newaetech/sonata-pcb/sonata-one/sonata_kicad_project/Analog_Conversion.kicad_sch

## KiCad design sonata-one/sonata_kicad_project/Analog_Conversion.kicad_sch (2025-01-31)

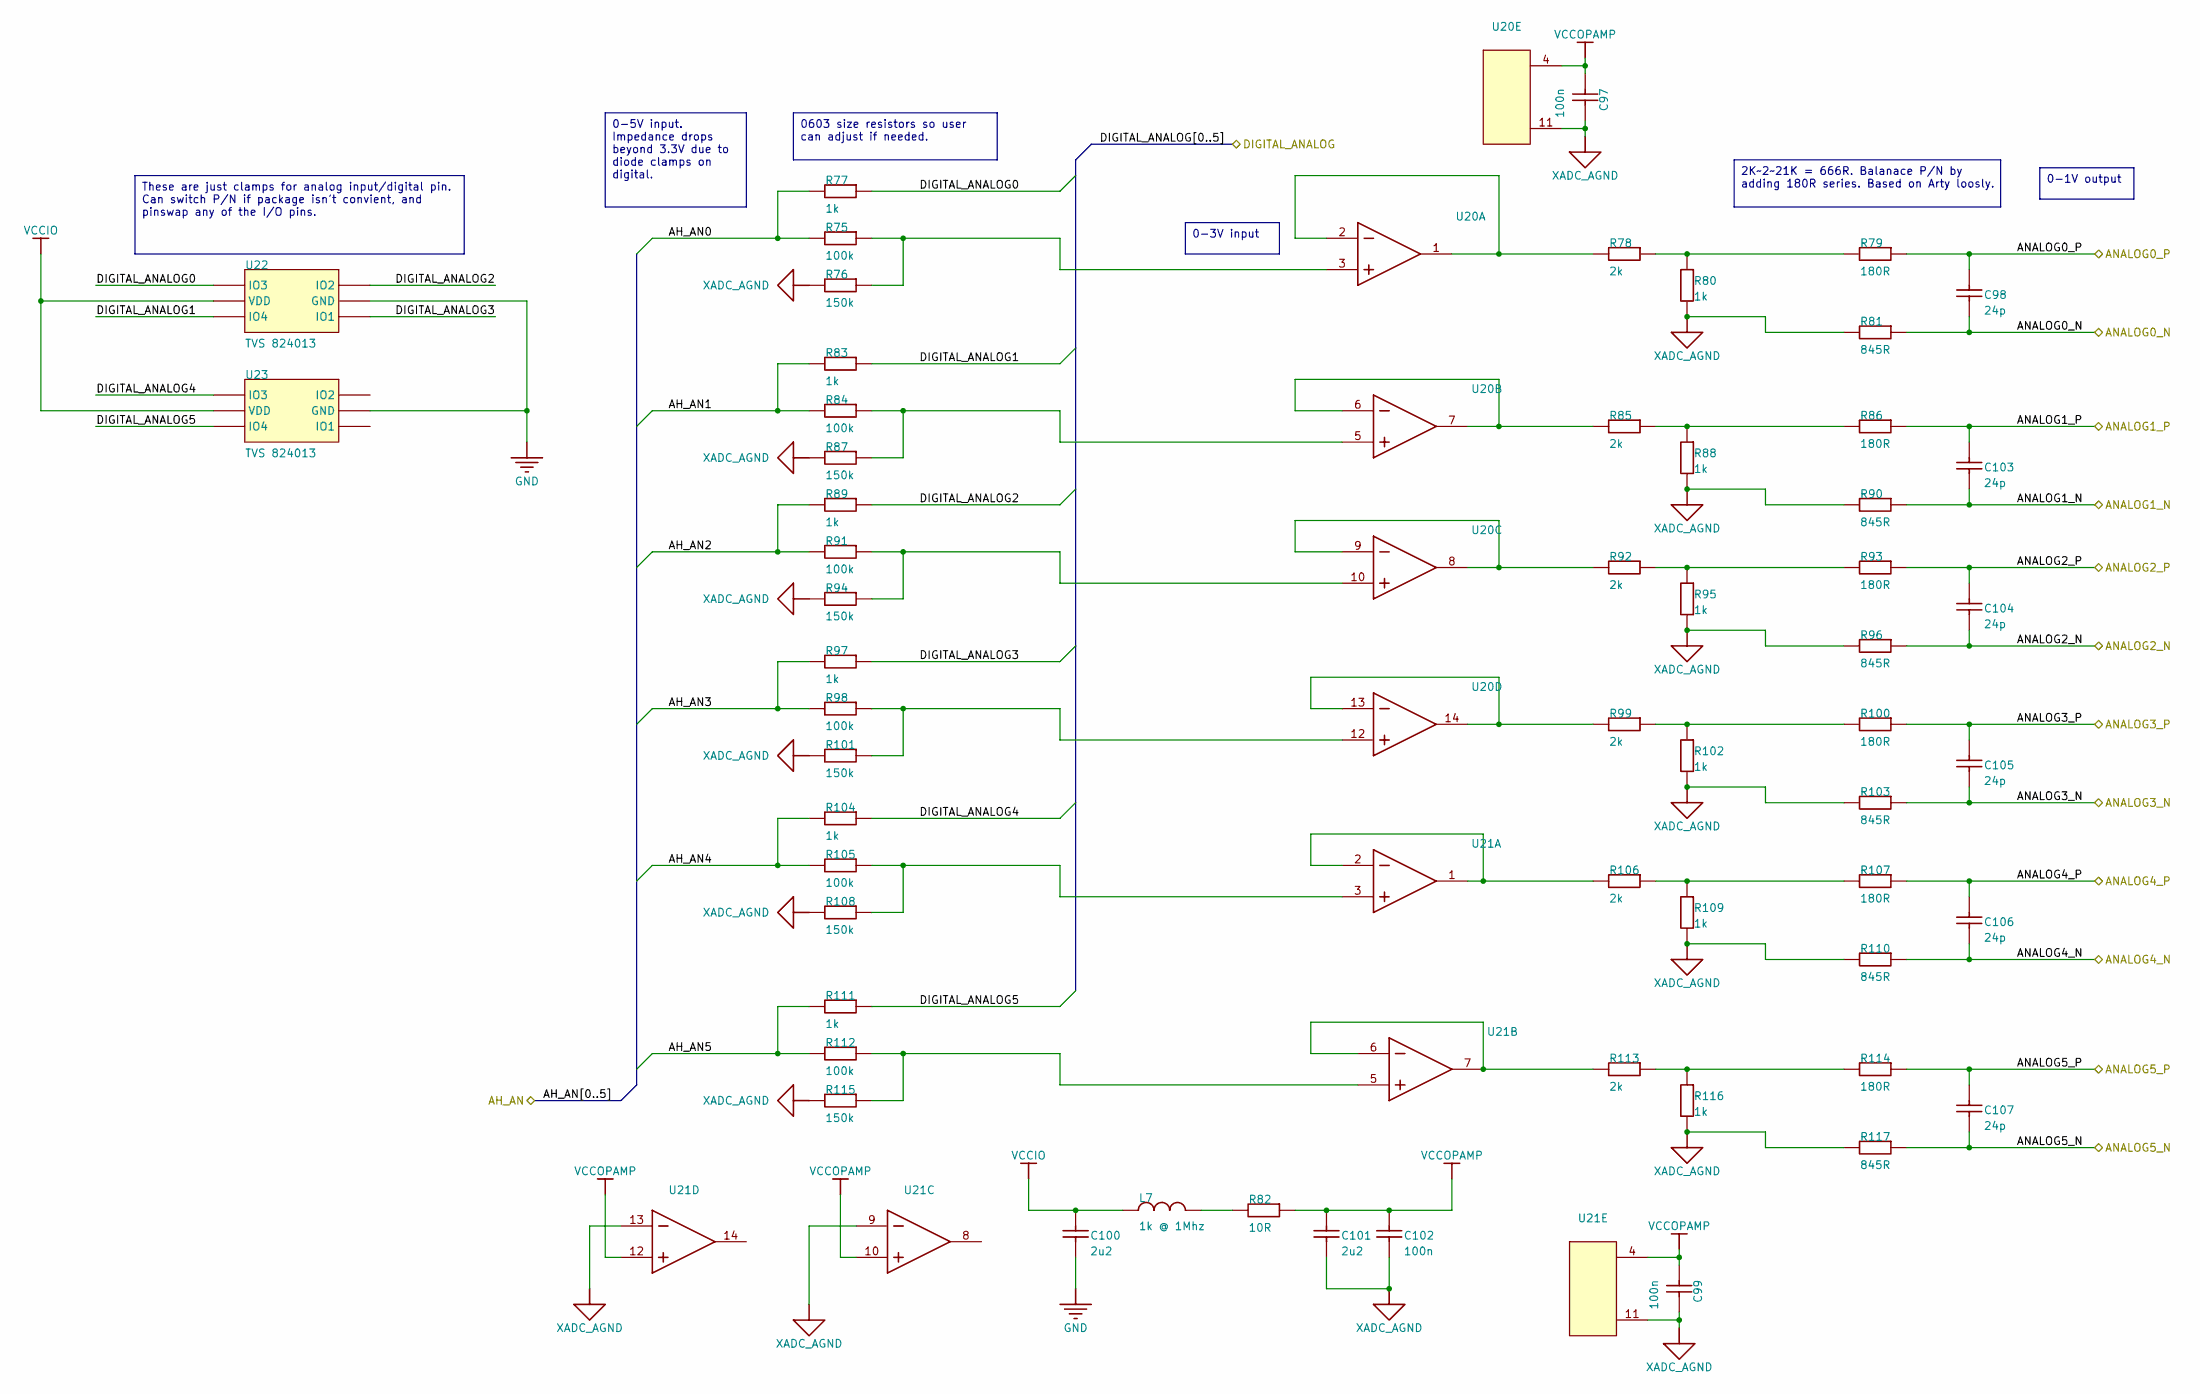
[picture p4: schematic Analog_Conversion.kicad_sch]

Parts:
C97, C99, C102: 100n; CAPC0402_M; MANUFACTURE PART NUMBER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 CGA2B3X7R1V104K050BB
C98, C103, C104, C105, C106, C107: 24p; CAPC0402_M; MANUFACTURE PART NUMBER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 GCM1555C1H240FA16D
C100, C101: 2u2; CAPC0603_M; MANUFACTURE PART NUMBER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 CL10B225KP8NNNC
L7: 1k @ 1Mhz; IND_0603; MANUFACTURE PART NUMBER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 FBMH1608HM102-T FBMH1608HM102-T FBMH160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
R75, R84, R91, R98, R105, R112: 100k; RESC1608X55N; MANUFACTURE PART NUMBER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 RC0603FR-07100KL
R76, R87, R94, R101, R108, R115: 150k; RESC1608X55N; MANUFACTURE PART NUMBER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 RC0603FR-07150KL
R77, R83, R89, R97, R104, R111: 1k; RESC1608X55N; MANUFACTURE PART NUMBER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 RC0603FR-071KL
R78, R85, R92, R99, R106, R113: 2k; RESC1005X40N; MANUFACTURE PART NUMBER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 RC0402FR-072KL
R79, R86, R93, R100, R107, R114: 180R; RESC1005X40N; MANUFACTURE PART NUMBER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 RC0402FR-07180RL
R80, R88, R95, R102, R109, R116: 1k; RESC1005X40N; MANUFACTURE PART NUMBER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 RC0402FR-071KL
R81, R90, R96, R103, R110, R117: 845R; RESC1005X40N; MANUFACTURE PART NUMBER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 RC0402FR-07845RL
R82: 10R; RESC1608X55N; MANUFACTURE PART NUMBER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 RC0603FR-0710RL
U20, U21: TSSOP-ST14_M
U22, U23: TVS 824013; SOT95P280X145-6N; MANUFACTURE PART NUMBER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 824013

Connections:
AH_AN0: R75.1, R77.1
AH_AN1: R83.1, R84.1
AH_AN2: R89.1, R91.1
AH_AN3: R97.1, R98.1
AH_AN4: R104.1, R105.1
AH_AN5: R111.1, R112.1
ANALOG0_N: C98.2, R81.2
ANALOG0_P: C98.1, R79.2
ANALOG1_N: C103.2, R90.2
ANALOG1_P: C103.1, R86.2
ANALOG2_N: C104.2, R96.2
ANALOG2_P: C104.1, R93.2
ANALOG3_N: C105.2, R103.2
ANALOG3_P: C105.1, R100.2
ANALOG4_N: C106.2, R110.2
ANALOG4_P: C106.1, R107.2
ANALOG5_N: C107.2, R117.2
ANALOG5_P: C107.1, R114.2
DIGITAL_ANALOG0: R77.2, U22.4 (IO3)
DIGITAL_ANALOG1: R83.2, U22.6 (IO4)
DIGITAL_ANALOG2: R89.2, U22.3 (IO2)
DIGITAL_ANALOG3: R97.2, U22.1 (IO1)
DIGITAL_ANALOG4: R104.2, U23.4 (IO3)
DIGITAL_ANALOG5: R111.2, U23.6 (IO4)
GND: C100.2, U22.2 (GND), U23.2 (GND)
unnamed: L7.2, R82.1
unnamed: R75.2, R76.2, U20.3 (VINA+)
unnamed: R78.1, U20.1 (VOUTA), U20.2 (VINA-)
unnamed: R78.2, R79.1, R80.1
unnamed: R84.2, R87.2, U20.5 (VINB+)
unnamed: R85.1, U20.6 (VINB-), U20.7 (VOUTB)
unnamed: R85.2, R86.1, R88.1
unnamed: R91.2, R94.2, U20.10 (VINC+)
unnamed: R92.1, U20.8 (VOUTC), U20.9 (VINC-)
unnamed: R92.2, R93.1, R95.1
unnamed: R99.1, U20.13 (VIND-), U20.14 (VOUTD)
unnamed: R99.2, R100.1, R102.1
unnamed: R98.2, R101.2, U20.12 (VIND+)
unnamed: R105.2, R108.2, U21.3 (VINA+)
unnamed: R106.1, U21.1 (VOUTA), U21.2 (VINA-)
unnamed: R106.2, R107.1, R109.1
unnamed: R112.2, R115.2, U21.5 (VINB+)
unnamed: R113.1, U21.6 (VINB-), U21.7 (VOUTB)
unnamed: R113.2, R114.1, R116.1
VCCIO: C100.1, L7.1, U22.5 (VDD), U23.5 (VDD)
VCCOPAMP: C97.1, C99.1, C101.1, C102.1, R82.2, U20.4 (Vin+), U21.4 (Vin+), U21.10 (VINC+), U21.12 (VIND+)
XADC_AGND: C97.2, C99.2, C101.2, C102.2, R76.1, R80.2, R81.1, R87.1, R88.2, R90.1, R94.1, R95.2, R96.1, R101.1, R102.2, R103.1, R108.1, R109.2, R110.1, R115.1, R116.2, R117.1, U20.11 (Vin-), U21.9 (VINC-), U21.11 (Vin-), U21.13 (VIND-)

Notes on the sheet:
0603 size resistors so user can adjust if needed.
2K~2~21K = 666R. Balanace P/N by adding 180R series. Based on Arty loosly.
0-3V input
These are just clamps for analog input/digital pin. Can switch P/N if package isn't convient, and pinswap any of the I/O pins.
0-1V output
0-5V input. Impedance drops beyond 3.3V due to diode clamps on digital.
