newaetech/sonata-pcb/sonata-one/sonata_kicad_project/ETHMAC.kicad_sch

## KiCad design sonata-one/sonata_kicad_project/ETHMAC.kicad_sch (2025-01-31)

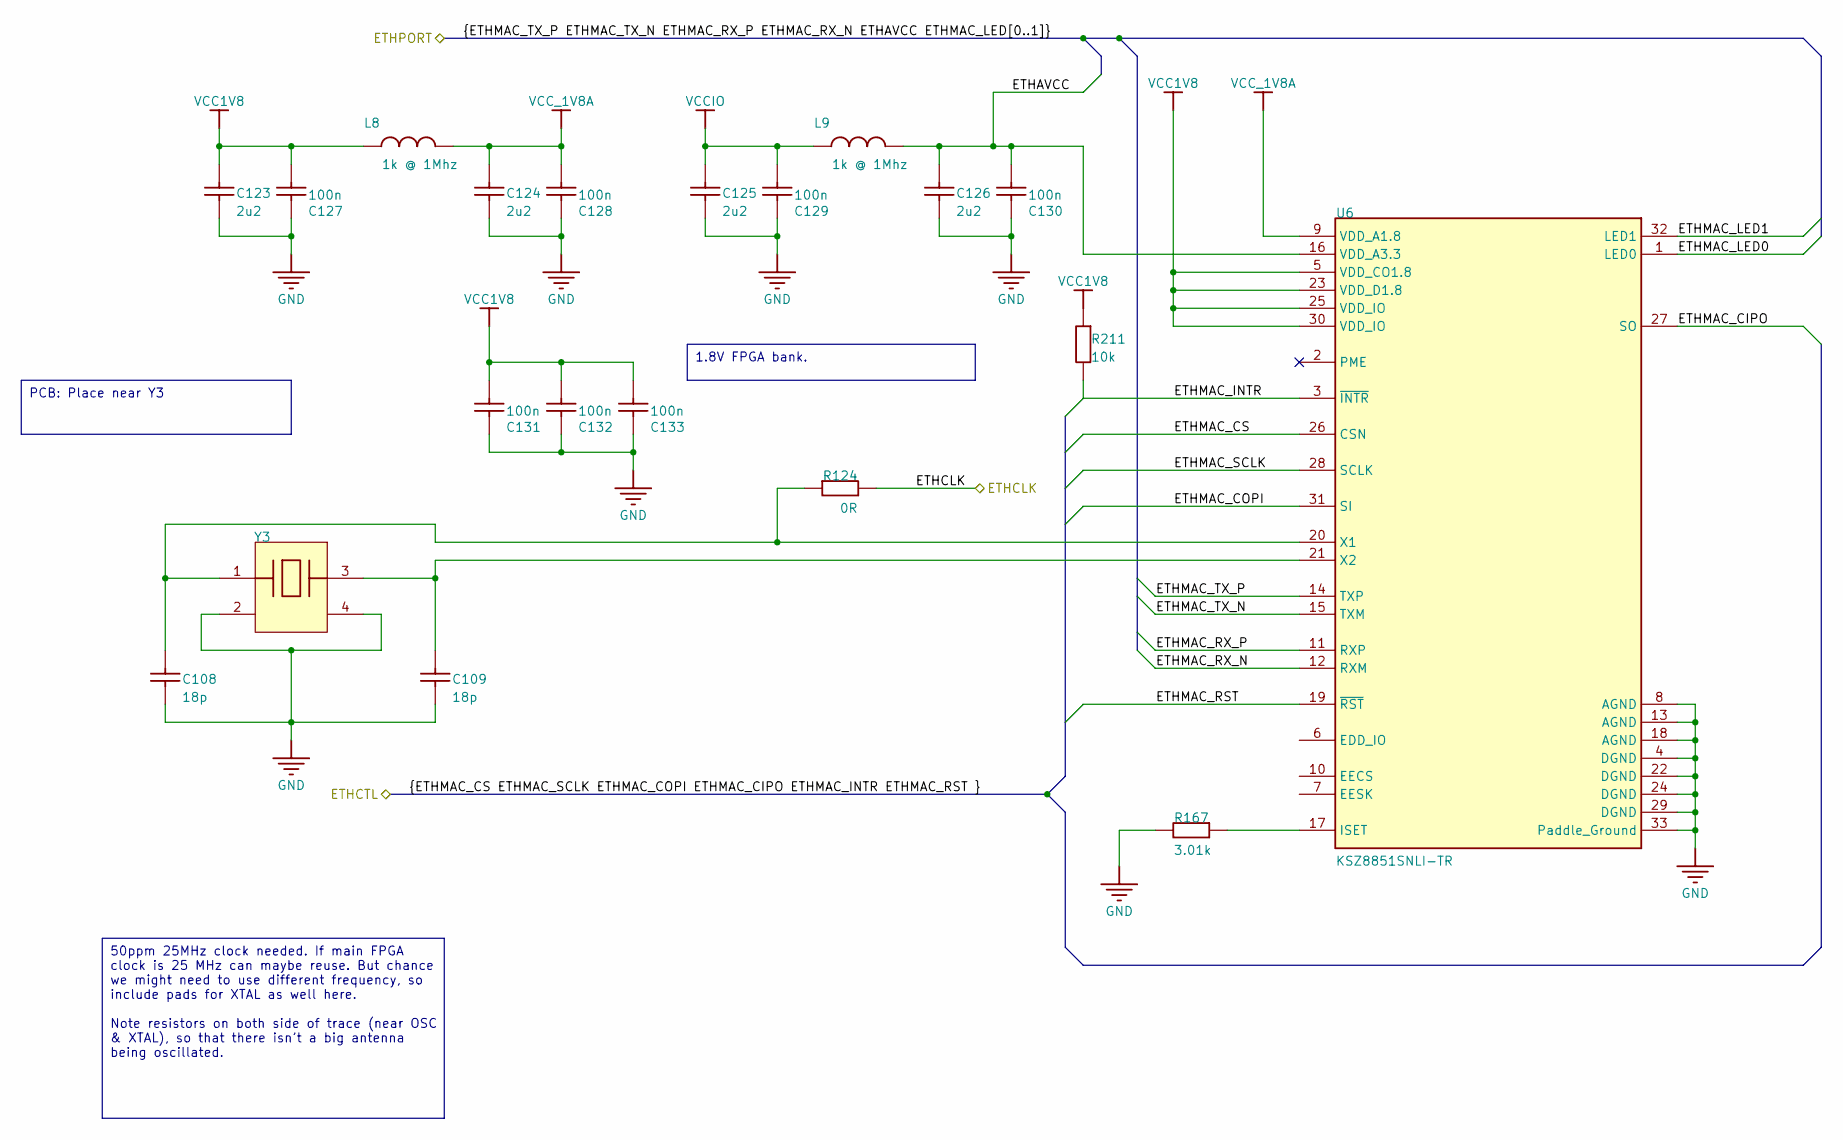
[picture p5: schematic ETHMAC.kicad_sch]

Parts:
C108, C109: 18p; CAPC0402_M; MANUFACTURE PART NUMBER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 GRM1555C1H180JA01D
C123, C124, C125, C126: 2u2; CAPC0603_M; MANUFACTURE PART NUMBER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 CL10B225KP8NNNC
C127, C128, C129, C130, C131, C132, C133: 100n; CAPC0402_M
L8, L9: 1k @ 1Mhz; IND_0603; MANUFACTURE PART NUMBER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 FBMH1608HM102-T FBMH1608HM102-T FBMH160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
R124: 0R; RESC1608X55N; MANUFACTURE PART NUMBER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 RC0603FR-070RL
R167: 3.01k; RESC1005X40N; MANUFACTURE PART NUMBER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 RC0402FR-073K01L
R211: 10k; RESC1005X40N; MANUFACTURE PART NUMBER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 RC0402FR-0710KL
U6: KSZ8851SNLI-TR; FP-QFN55-32LD-PL-5-IPC_C
Y3: H130B-12.000-16-2525-EXT-TR; 5x3.2MM XTAL; MANUFACTURE PART NUMBER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 H130B-25.000-18-1030-EXT-TR

Connections:
ETHAVCC: C126.1, C130.1, L9.2, U6.16 (VDD_A3.3)
ETHCLK: R124.1
ETHMAC_CIPO: U6.27 (SO)
ETHMAC_COPI: U6.31 (SI)
ETHMAC_CS: U6.26 (CSN)
ETHMAC_INTR: R211.2, U6.3 (~INTR)
ETHMAC_LED0: U6.1 (LED0)
ETHMAC_LED1: U6.32 (LED1)
ETHMAC_RST: U6.19 (~RST)
ETHMAC_RX_N: U6.12 (RXM)
ETHMAC_RX_P: U6.11 (RXP)
ETHMAC_SCLK: U6.28 (SCLK)
ETHMAC_TX_N: U6.15 (TXM)
ETHMAC_TX_P: U6.14 (TXP)
GND: C108.2, C109.2, C123.2, C124.2, C125.2, C126.2, C127.2, C128.2, C129.2, C130.2, C131.2, C132.2, C133.2, R167.1, U6.4 (DGND), U6.8 (AGND), U6.13 (AGND), U6.18 (AGND), U6.22 (DGND), U6.24 (DGND), U6.29 (DGND), U6.33 (Paddle_Ground), Y3.2, Y3.4
unnamed: C108.1, R124.2, U6.20 (X1), Y3.1
unnamed: C109.1, U6.21 (X2), Y3.3
unnamed: R167.2, U6.17 (ISET)
VCC1V8: C123.1, C127.1, C131.1, C132.1, C133.1, L8.1, R211.1, U6.5 (VDD_CO1.8), U6.23 (VDD_D1.8), U6.25 (VDD_IO), U6.30 (VDD_IO)
VCCIO: C125.1, C129.1, L9.1
VCC_1V8A: C124.1, C128.1, L8.2, U6.9 (VDD_A1.8)

Notes on the sheet:
50ppm 25MHz clock needed. If main FPGA clock is 25 MHz can maybe reuse. But chance we might need to use different frequency, so include pads for XTAL as well here. Note resistors on both side of trace (near OSC & XTAL), so that there isn't a big antenna being oscillated.
1.8V FPGA bank.
PCB: Place near Y3
