newaetech/sonata-pcb/sonata-one/sonata_kicad_project/FPGA_ANA_1.8V.kicad_sch

## KiCad design sonata-one/sonata_kicad_project/FPGA_ANA_1.8V.kicad_sch (2025-01-31)

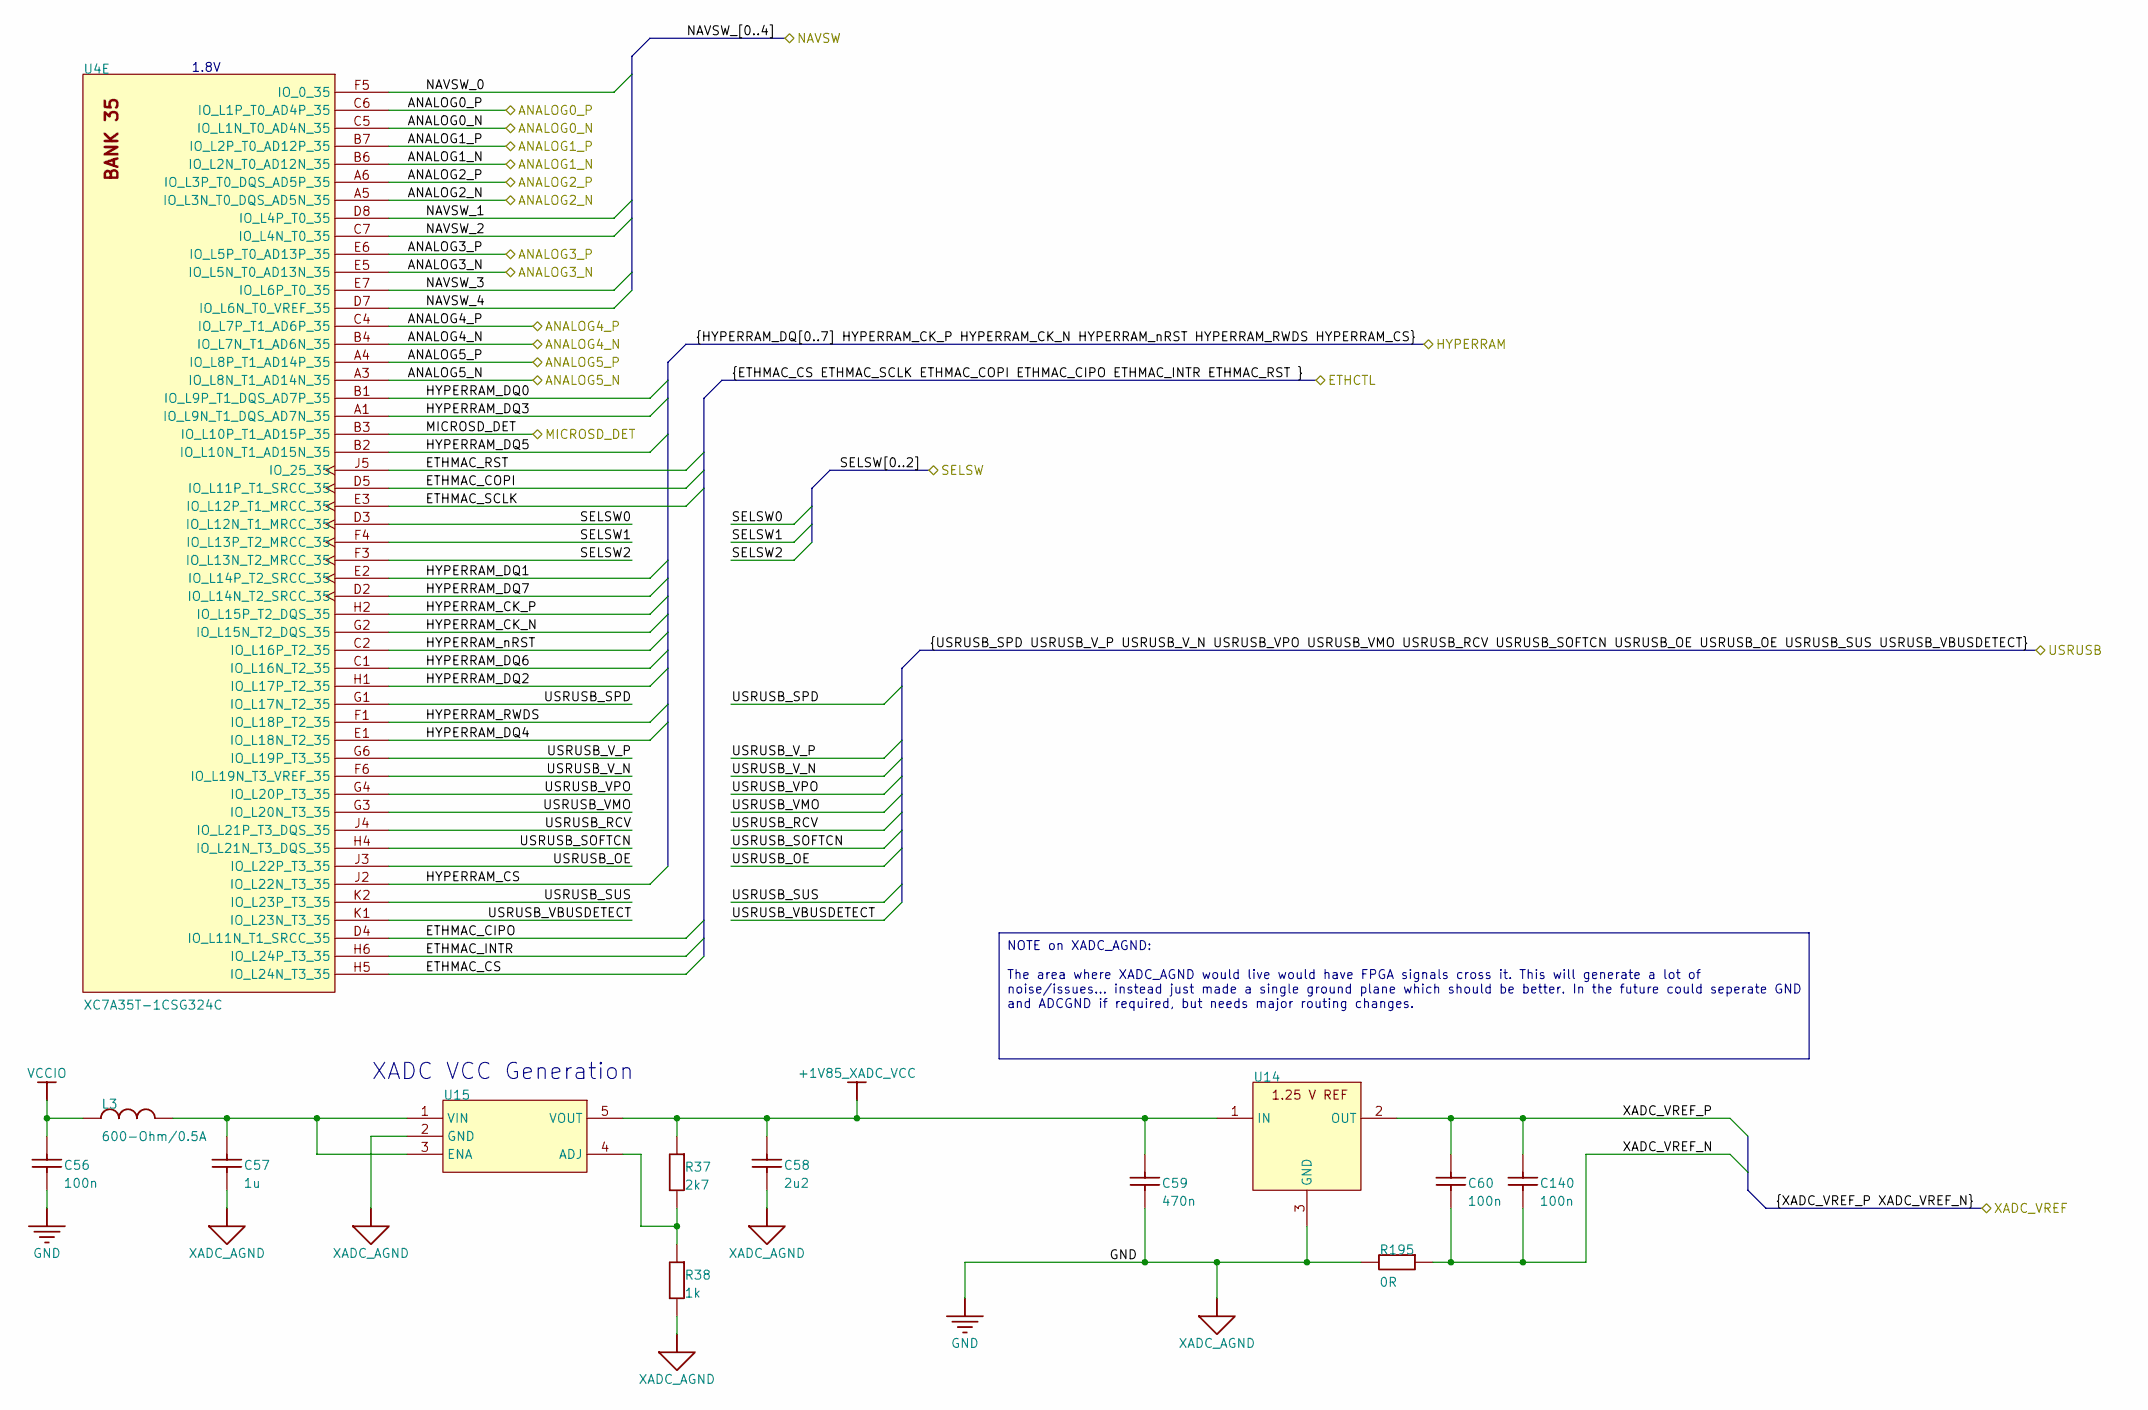
[picture p6: schematic FPGA_ANA_1.8V.kicad_sch]

Parts:
C56, C60, C140: 100n; CAPC0402_M; MANUFACTURE PART NUMBER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 CGA2B3X7R1V104K050BB
C57: 1u; CAPC0603_M; MANUFACTURE PART NUMBER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 CL10A105KB8NNNC
C58: 2u2; CAPC0603_M; MANUFACTURE PART NUMBER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 GRM188R61E225MA12D
C59: 470n; CAPC0603_M; MANUFACTURE PART NUMBER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 UMK107B7474KA-TR
L3: 600-Ohm/0.5A; IND_0603; MANUFACTURE PART NUMBER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 BLM18AG601SN1D
R37: 2k7; RESC1005X40N; MANUFACTURE PART NUMBER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 RC0402FR-072K7L
R38: 1k; RESC1005X40N; MANUFACTURE PART NUMBER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 RC0402FR-071KL
R195: 0R; RESC1005X40N; MANUFACTURE PART NUMBER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 RC0402FR-070RL
U4: XC7A35T-1CSG324C; CSG324
U14: REF3012AIDBZT; SOT95P237X112-3N; MANUFACTURE PART NUMBER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 REF3012AIDBZT
U15: Linear Voltage Regulator IC 1 Output 300mA TSOT-5; SOT23-5P95_285X145L45X40; MANUFACTURE PART NUMBER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 ADP123AUJZ-R7

Connections:
+1V85_XADC_VCC: C58.1, C59.1, R37.1, U14.1 (IN), U15.5 (VOUT)
ANALOG0_N: U4.C5 (IO_L1N_T0_AD4N_35)
ANALOG0_P: U4.C6 (IO_L1P_T0_AD4P_35)
ANALOG1_N: U4.B6 (IO_L2N_T0_AD12N_35)
ANALOG1_P: U4.B7 (IO_L2P_T0_AD12P_35)
ANALOG2_N: U4.A5 (IO_L3N_T0_DQS_AD5N_35)
ANALOG2_P: U4.A6 (IO_L3P_T0_DQS_AD5P_35)
ANALOG3_N: U4.E5 (IO_L5N_T0_AD13N_35)
ANALOG3_P: U4.E6 (IO_L5P_T0_AD13P_35)
ANALOG4_N: U4.B4 (IO_L7N_T1_AD6N_35)
ANALOG4_P: U4.C4 (IO_L7P_T1_AD6P_35)
ANALOG5_N: U4.A3 (IO_L8N_T1_AD14N_35)
ANALOG5_P: U4.A4 (IO_L8P_T1_AD14P_35)
ETHMAC_CIPO: U4.D4 (IO_L11N_T1_SRCC_35)
ETHMAC_COPI: U4.D5 (IO_L11P_T1_SRCC_35)
ETHMAC_CS: U4.H5 (IO_L24N_T3_35)
ETHMAC_INTR: U4.H6 (IO_L24P_T3_35)
ETHMAC_RST: U4.J5 (IO_25_35)
ETHMAC_SCLK: U4.E3 (IO_L12P_T1_MRCC_35)
GND: C56.2, C57.2, C58.2, C59.2, R38.2, R195.1, U14.3 (GND), U15.2 (GND)
HYPERRAM_CK_N: U4.G2 (IO_L15N_T2_DQS_35)
HYPERRAM_CK_P: U4.H2 (IO_L15P_T2_DQS_35)
HYPERRAM_CS: U4.J2 (IO_L22N_T3_35)
HYPERRAM_DQ0: U4.B1 (IO_L9P_T1_DQS_AD7P_35)
HYPERRAM_DQ1: U4.E2 (IO_L14P_T2_SRCC_35)
HYPERRAM_DQ2: U4.H1 (IO_L17P_T2_35)
HYPERRAM_DQ3: U4.A1 (IO_L9N_T1_DQS_AD7N_35)
HYPERRAM_DQ4: U4.E1 (IO_L18N_T2_35)
HYPERRAM_DQ5: U4.B2 (IO_L10N_T1_AD15N_35)
HYPERRAM_DQ6: U4.C1 (IO_L16N_T2_35)
HYPERRAM_DQ7: U4.D2 (IO_L14N_T2_SRCC_35)
HYPERRAM_RWDS: U4.F1 (IO_L18P_T2_35)
HYPERRAM_nRST: U4.C2 (IO_L16P_T2_35)
MICROSD_DET: U4.B3 (IO_L10P_T1_AD15P_35)
NAVSW_0: U4.F5 (IO_0_35)
NAVSW_1: U4.D8 (IO_L4P_T0_35)
NAVSW_2: U4.C7 (IO_L4N_T0_35)
NAVSW_3: U4.E7 (IO_L6P_T0_35)
NAVSW_4: U4.D7 (IO_L6N_T0_VREF_35)
unnamed: C57.1, L3.2, U15.1 (VIN), U15.3 (ENA)
unnamed: R37.2, R38.1, U15.4 (ADJ)
SELSW0: U4.D3 (IO_L12N_T1_MRCC_35)
SELSW1: U4.F4 (IO_L13P_T2_MRCC_35)
SELSW2: U4.F3 (IO_L13N_T2_MRCC_35)
USRUSB_OE: U4.J3 (IO_L22P_T3_35)
USRUSB_RCV: U4.J4 (IO_L21P_T3_DQS_35)
USRUSB_SOFTCN: U4.H4 (IO_L21N_T3_DQS_35)
USRUSB_SPD: U4.G1 (IO_L17N_T2_35)
USRUSB_SUS: U4.K2 (IO_L23P_T3_35)
USRUSB_VBUSDETECT: U4.K1 (IO_L23N_T3_35)
USRUSB_VMO: U4.G3 (IO_L20N_T3_35)
USRUSB_VPO: U4.G4 (IO_L20P_T3_35)
USRUSB_V_N: U4.F6 (IO_L19N_T3_VREF_35)
USRUSB_V_P: U4.G6 (IO_L19P_T3_35)
VCCIO: C56.1, L3.1
XADC_VREF_N: C60.2, C140.2, R195.2
XADC_VREF_P: C60.1, C140.1, U14.2 (OUT)

Notes on the sheet:
NOTE on XADC_AGND: The area where XADC_AGND would live would have FPGA signals cross it. This will generate a lot of noise/issues... instead just made a single ground plane which should be better. In the future could seperate GND and ADCGND if required, but needs major routing changes.
XADC VCC Generation
1.8V
