newaetech/sonata-pcb/sonata-one/sonata_kicad_project/FPGA_Config.kicad_sch

## KiCad design sonata-one/sonata_kicad_project/FPGA_Config.kicad_sch (2025-01-31)

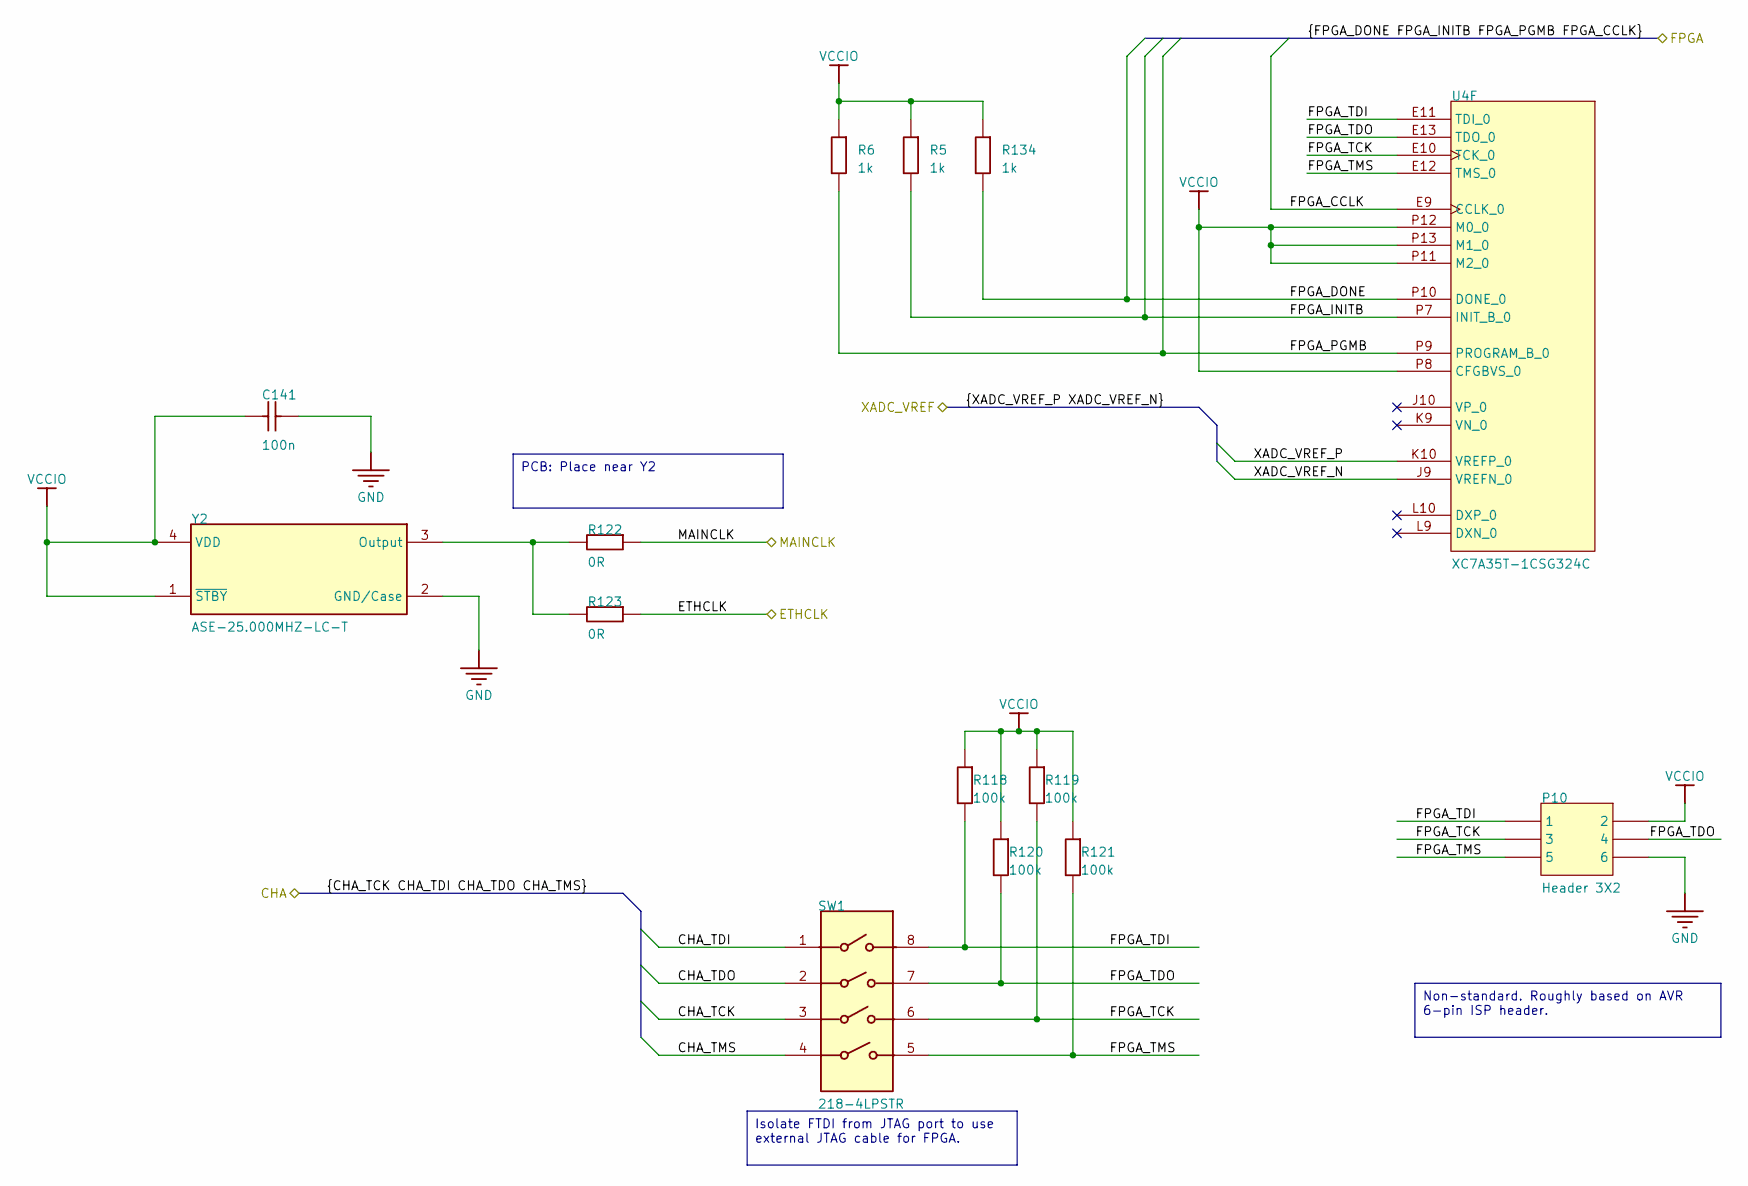
[picture p7: schematic FPGA_Config.kicad_sch]

Parts:
C141: 100n; CAPC0402_M; MANUFACTURE PART NUMBER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 CGA2B3X7R1V104K050BB
P10: Header 3X2; HDR2X3
R5, R6, R134: 1k; RESC1608X55N; MANUFACTURE PART NUMBER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 RC0603FR-071KL
R118, R119, R120, R121: 100k; RESC1005X40N; MANUFACTURE PART NUMBER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 RC0402FR-07100KL
R122, R123: 0R; RESC1608X55N; MANUFACTURE PART NUMBER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 RC0603FR-070RL
SW1: 218-4LPSTR; FP-218-4LPSTR-MFG
U4: XC7A35T-1CSG324C; CSG324
Y2: ASE-25.000MHZ-LC-T; FP-ASE-MFG

Connections:
CHA_TCK: SW1.3
CHA_TDI: SW1.1
CHA_TDO: SW1.2
CHA_TMS: SW1.4
ETHCLK: R123.2
FPGA_CCLK: U4.E9 (CCLK_0)
FPGA_DONE: R134.2, U4.P10 (DONE_0)
FPGA_INITB: R5.2, U4.P7 (INIT_B_0)
FPGA_PGMB: R6.2, U4.P9 (PROGRAM_B_0)
FPGA_TCK: P10.3, R119.2, SW1.6, U4.E10 (TCK_0)
FPGA_TDI: P10.1, R118.2, SW1.8, U4.E11 (TDI_0)
FPGA_TDO: P10.4, R120.2, SW1.7, U4.E13 (TDO_0)
FPGA_TMS: P10.5, R121.2, SW1.5, U4.E12 (TMS_0)
GND: C141.2, P10.6, Y2.2 (GND/Case)
MAINCLK: R122.2
unnamed: R122.1, R123.1, Y2.3 (Output)
VCCIO: C141.1, P10.2, R5.1, R6.1, R118.1, R119.1, R120.1, R121.1, R134.1, U4.P8 (CFGBVS_0), U4.P11 (M2_0), U4.P12 (M0_0), U4.P13 (M1_0), Y2.1 (~STBY), Y2.4 (VDD)
XADC_VREF_N: U4.J9 (VREFN_0)
XADC_VREF_P: U4.K10 (VREFP_0)

Notes on the sheet:
Non-standard. Roughly based on AVR 6-pin ISP header.
PCB: Place near Y2
Isolate FTDI from JTAG port to use external JTAG cable for FPGA.
