newaetech/sonata-pcb/sonata-one/sonata_kicad_project/FPGA_IO14_34_Flash.kicad_sch

## KiCad design sonata-one/sonata_kicad_project/FPGA_IO14_34_Flash.kicad_sch (2025-01-31)

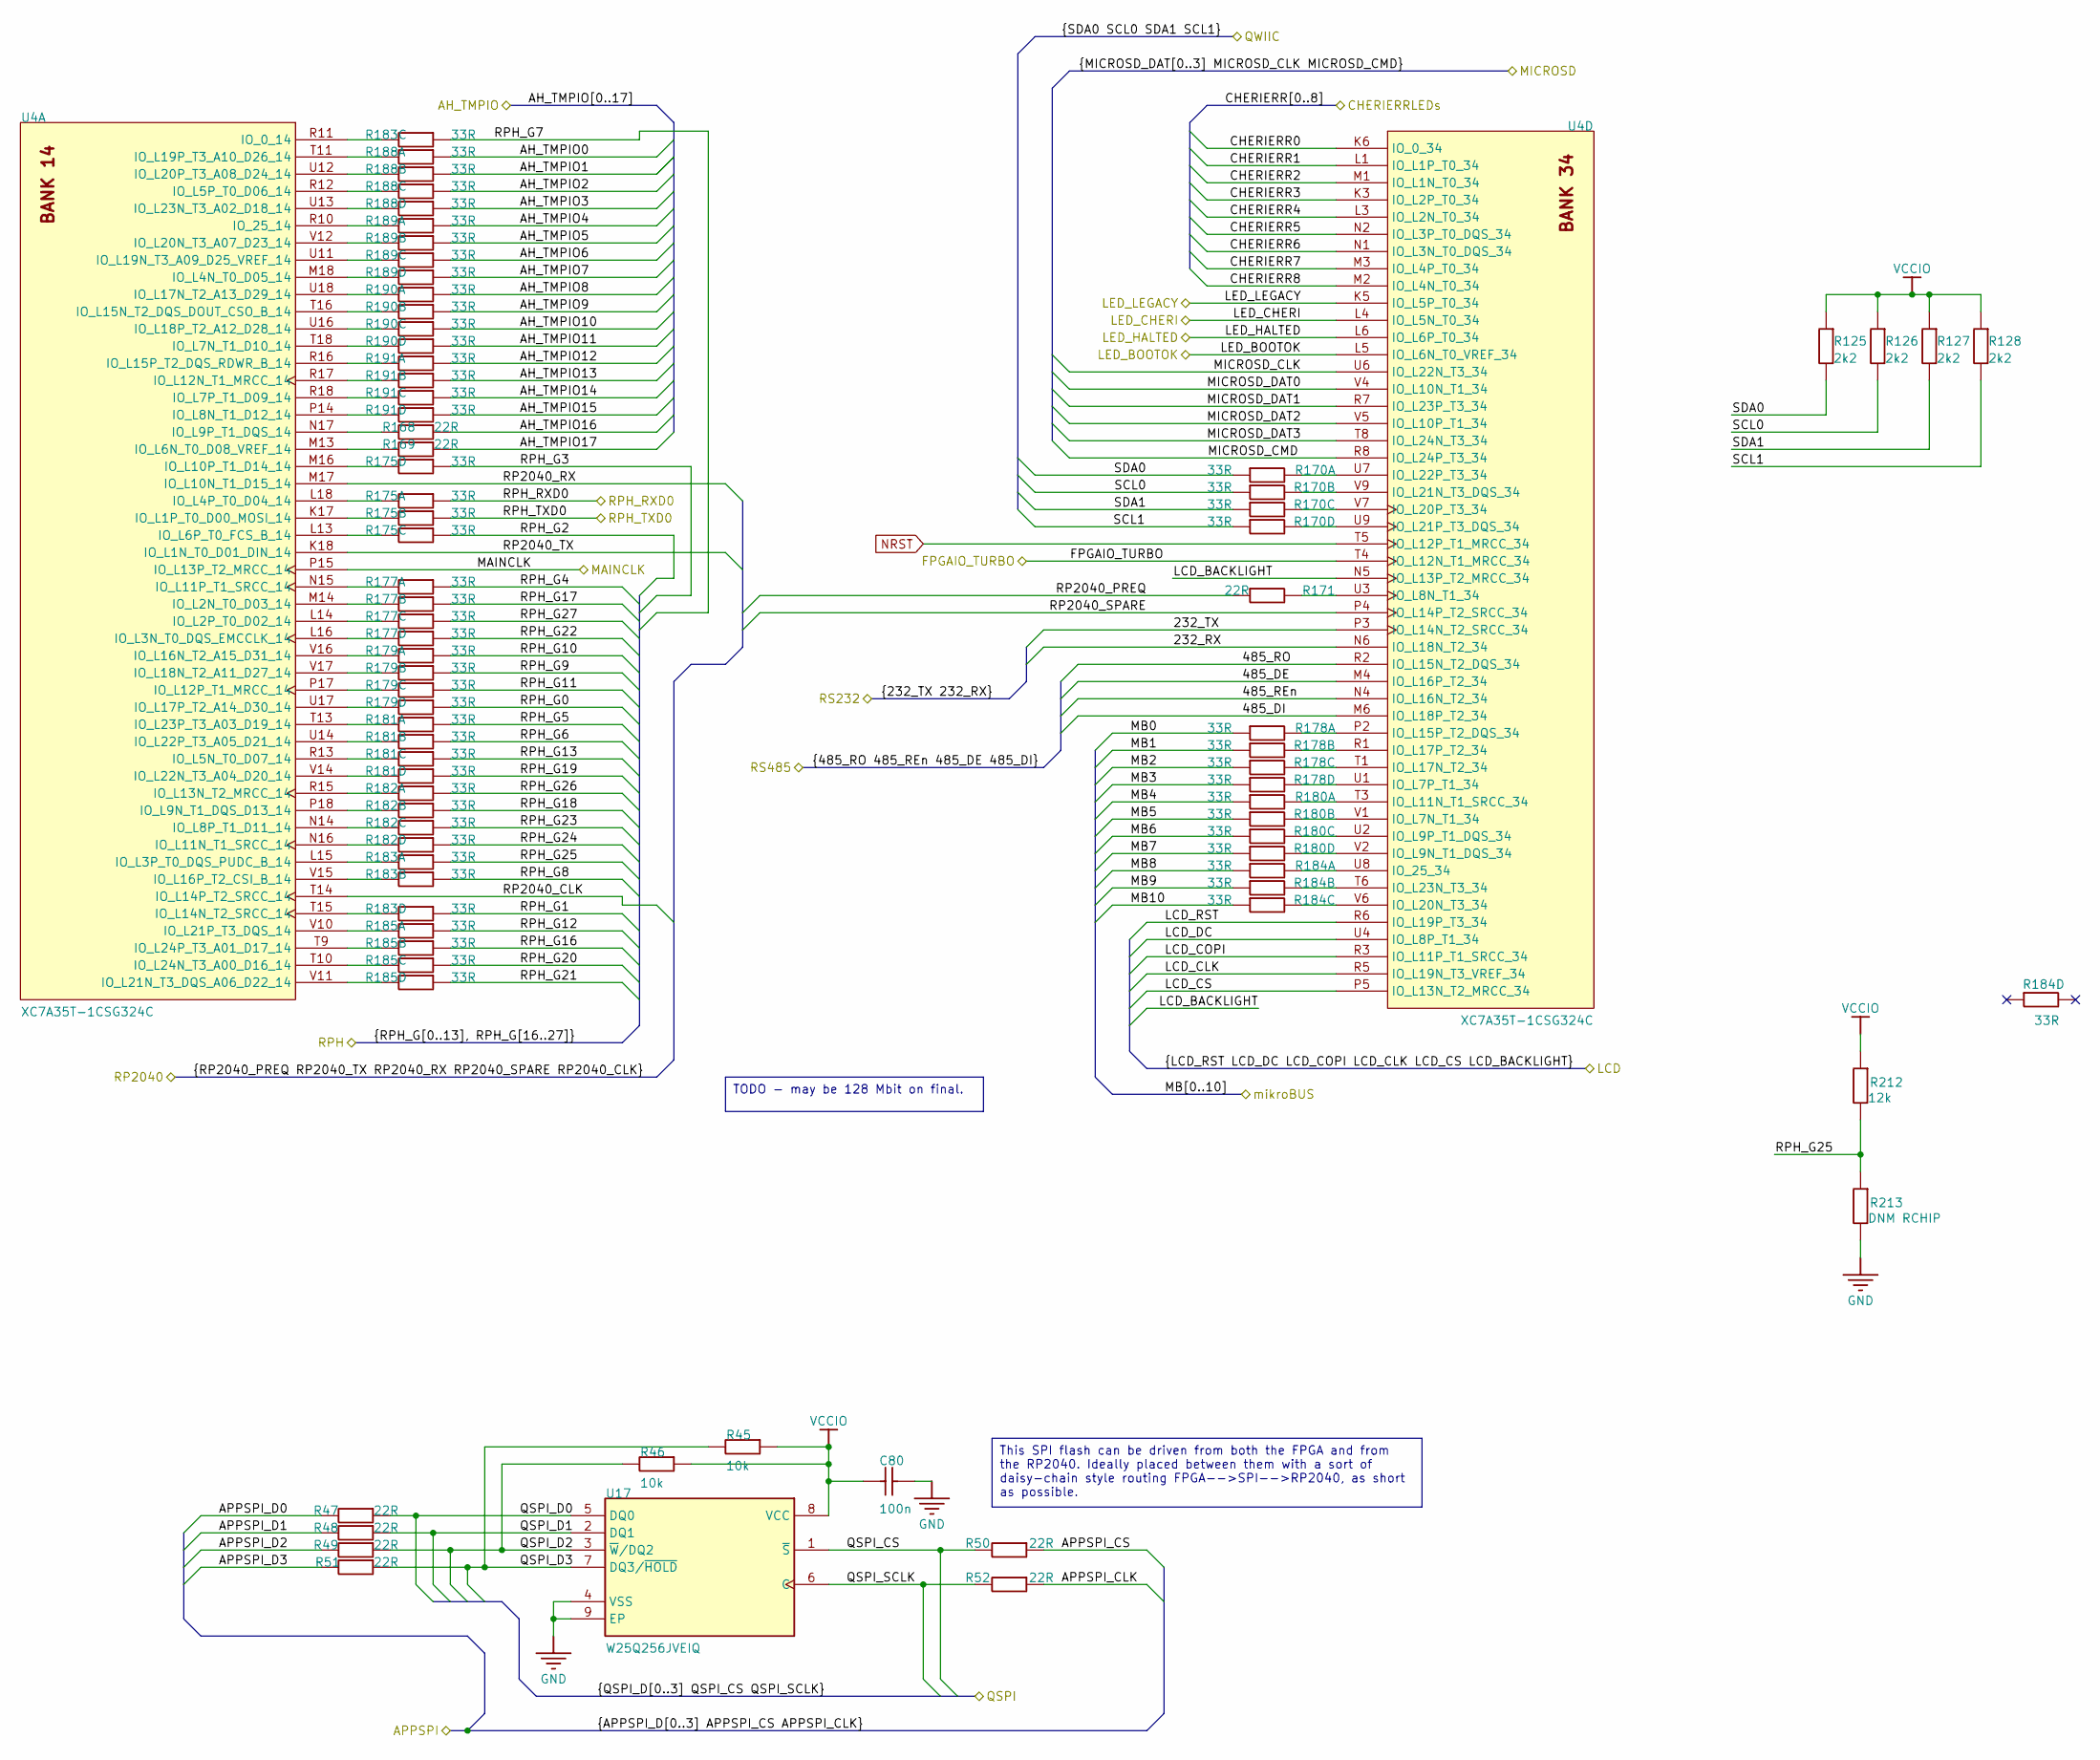
[picture p8: schematic FPGA_IO14_34_Flash.kicad_sch]

Parts:
C80: 100n; CAPC0402_M; MANUFACTURE PART NUMBER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 CGA2B3X7R1V104K050BB
R45, R46: 10k; RESC1005X40N; MANUFACTURE PART NUMBER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 RC0402FR-0710KL
R47, R48, R49, R50, R51, R52, R168, R169, R171: 22R; RESC1005X40N; MANUFACTURE PART NUMBER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 RC0402FR-0722RL
R125, R126, R127, R128: 2k2; RESC1608X55N; MANUFACTURE PART NUMBER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 RC0603FR-072K2L
R170, R175, R177, R178, R179, R180, R181, R182, R183, R184, R185, R188, R189, R190, R191: 33R; 741C083; MANUFACTURE PART NUMBER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 741C083330JP
R212: 12k; RESC1608X55N; MANUFACTURE PART NUMBER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 RC0603FR-0712KL
R213: DNM RCHIP; RESC1608X55N
U4: XC7A35T-1CSG324C; CSG324
U17: W25Q256JVEIQ; WSON68_Micron; MANUFACTURE PART NUMBER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 W25Q256JVEIQ

Connections:
232_RX: U4.N6 (IO_L18N_T2_34)
232_TX: U4.P3 (IO_L14N_T2_SRCC_34)
485_DE: U4.M4 (IO_L16P_T2_34)
485_DI: U4.M6 (IO_L18P_T2_34)
485_REn: U4.N4 (IO_L16N_T2_34)
485_RO: U4.R2 (IO_L15N_T2_DQS_34)
AH_TMPIO0: R188.1B
AH_TMPIO1: R188.2B
AH_TMPIO2: R188.3B
AH_TMPIO3: R188.4B
AH_TMPIO4: R189.1B
AH_TMPIO5: R189.2B
AH_TMPIO6: R189.3B
AH_TMPIO7: R189.4B
AH_TMPIO8: R190.1B
AH_TMPIO9: R190.2B
AH_TMPIO10: R190.3B
AH_TMPIO11: R190.4B
AH_TMPIO12: R191.1B
AH_TMPIO13: R191.2B
AH_TMPIO14: R191.3B
AH_TMPIO15: R191.4B
AH_TMPIO16: R168.2
AH_TMPIO17: R169.2
APPSPI_CLK: R52.2
APPSPI_CS: R50.2
APPSPI_D0: R47.1
APPSPI_D1: R48.1
APPSPI_D2: R49.1
APPSPI_D3: R51.1
CHERIERR0: U4.K6 (IO_0_34)
CHERIERR1: U4.L1 (IO_L1P_T0_34)
CHERIERR2: U4.M1 (IO_L1N_T0_34)
CHERIERR3: U4.K3 (IO_L2P_T0_34)
CHERIERR4: U4.L3 (IO_L2N_T0_34)
CHERIERR5: U4.N2 (IO_L3P_T0_DQS_34)
CHERIERR6: U4.N1 (IO_L3N_T0_DQS_34)
CHERIERR7: U4.M3 (IO_L4P_T0_34)
CHERIERR8: U4.M2 (IO_L4N_T0_34)
FPGAIO_TURBO: U4.T4 (IO_L12N_T1_MRCC_34)
GND: C80.2, R213.1, U17.4 (VSS), U17.9 (EP)
LCD_BACKLIGHT: U4.N5 (IO_L13P_T2_MRCC_34)
LCD_CLK: U4.R5 (IO_L19N_T3_VREF_34)
LCD_COPI: U4.R3 (IO_L11P_T1_SRCC_34)
LCD_CS: U4.P5 (IO_L13N_T2_MRCC_34)
LCD_DC: U4.U4 (IO_L8P_T1_34)
LCD_RST: U4.R6 (IO_L19P_T3_34)
LED_BOOTOK: U4.L5 (IO_L6N_T0_VREF_34)
LED_CHERI: U4.L4 (IO_L5N_T0_34)
LED_HALTED: U4.L6 (IO_L6P_T0_34)
LED_LEGACY: U4.K5 (IO_L5P_T0_34)
MAINCLK: U4.P15 (IO_L13P_T2_MRCC_14)
MB0: R178.1B
MB1: R178.2B
MB2: R178.3B
MB3: R178.4B
MB4: R180.1B
MB5: R180.2B
MB6: R180.3B
MB7: R180.4B
MB8: R184.1B
MB9: R184.2B
MB10: R184.3B
MICROSD_CLK: U4.U6 (IO_L22N_T3_34)
MICROSD_CMD: U4.R8 (IO_L24P_T3_34)
MICROSD_DAT0: U4.V4 (IO_L10N_T1_34)
MICROSD_DAT1: U4.R7 (IO_L23P_T3_34)
MICROSD_DAT2: U4.V5 (IO_L10P_T1_34)
MICROSD_DAT3: U4.T8 (IO_L24N_T3_34)
NRST: U4.T5 (IO_L12P_T1_MRCC_34)
unnamed: R168.1, U4.N17 (IO_L9P_T1_DQS_14)
unnamed: R169.1, U4.M13 (IO_L6N_T0_D08_VREF_14)
unnamed: R170.1A, U4.U7 (IO_L22P_T3_34)
unnamed: R170.2A, U4.V9 (IO_L21N_T3_DQS_34)
unnamed: R170.3A, U4.V7 (IO_L20P_T3_34)
unnamed: R170.4A, U4.U9 (IO_L21P_T3_DQS_34)
unnamed: R171.1, U4.U3 (IO_L8N_T1_34)
unnamed: R175.1A, U4.L18 (IO_L4P_T0_D04_14)
unnamed: R175.2A, U4.K17 (IO_L1P_T0_D00_MOSI_14)
unnamed: R175.3A, U4.L13 (IO_L6P_T0_FCS_B_14)
unnamed: R175.4A, U4.M16 (IO_L10P_T1_D14_14)
unnamed: R177.1A, U4.N15 (IO_L11P_T1_SRCC_14)
unnamed: R177.2A, U4.M14 (IO_L2N_T0_D03_14)
unnamed: R177.3A, U4.L14 (IO_L2P_T0_D02_14)
unnamed: R177.4A, U4.L16 (IO_L3N_T0_DQS_EMCCLK_14)
unnamed: R178.1A, U4.P2 (IO_L15P_T2_DQS_34)
unnamed: R178.2A, U4.R1 (IO_L17P_T2_34)
unnamed: R178.3A, U4.T1 (IO_L17N_T2_34)
unnamed: R178.4A, U4.U1 (IO_L7P_T1_34)
unnamed: R179.1A, U4.V16 (IO_L16N_T2_A15_D31_14)
unnamed: R179.2A, U4.V17 (IO_L18N_T2_A11_D27_14)
unnamed: R179.3A, U4.P17 (IO_L12P_T1_MRCC_14)
unnamed: R179.4A, U4.U17 (IO_L17P_T2_A14_D30_14)
unnamed: R180.1A, U4.T3 (IO_L11N_T1_SRCC_34)
unnamed: R180.2A, U4.V1 (IO_L7N_T1_34)
unnamed: R180.3A, U4.U2 (IO_L9P_T1_DQS_34)
unnamed: R180.4A, U4.V2 (IO_L9N_T1_DQS_34)
unnamed: R181.1A, U4.T13 (IO_L23P_T3_A03_D19_14)
unnamed: R181.2A, U4.U14 (IO_L22P_T3_A05_D21_14)
unnamed: R181.3A, U4.R13 (IO_L5N_T0_D07_14)
unnamed: R181.4A, U4.V14 (IO_L22N_T3_A04_D20_14)
unnamed: R182.1A, U4.R15 (IO_L13N_T2_MRCC_14)
unnamed: R182.2A, U4.P18 (IO_L9N_T1_DQS_D13_14)
unnamed: R182.3A, U4.N14 (IO_L8P_T1_D11_14)
unnamed: R182.4A, U4.N16 (IO_L11N_T1_SRCC_14)
unnamed: R183.1A, U4.L15 (IO_L3P_T0_DQS_PUDC_B_14)
unnamed: R183.2A, U4.V15 (IO_L16P_T2_CSI_B_14)
unnamed: R183.3A, U4.R11 (IO_0_14)
unnamed: R183.4A, U4.T15 (IO_L14N_T2_SRCC_14)
unnamed: R184.1A, U4.U8 (IO_25_34)
unnamed: R184.2A, U4.T6 (IO_L23N_T3_34)
unnamed: R184.3A, U4.V6 (IO_L20N_T3_34)
unnamed: R185.1A, U4.V10 (IO_L21P_T3_DQS_14)
unnamed: R185.2A, U4.T9 (IO_L24P_T3_A01_D17_14)
unnamed: R185.3A, U4.T10 (IO_L24N_T3_A00_D16_14)
unnamed: R185.4A, U4.V11 (IO_L21N_T3_DQS_A06_D22_14)
unnamed: R188.1A, U4.T11 (IO_L19P_T3_A10_D26_14)
unnamed: R188.2A, U4.U12 (IO_L20P_T3_A08_D24_14)
unnamed: R188.3A, U4.R12 (IO_L5P_T0_D06_14)
unnamed: R188.4A, U4.U13 (IO_L23N_T3_A02_D18_14)
unnamed: R189.1A, U4.R10 (IO_25_14)
unnamed: R189.2A, U4.V12 (IO_L20N_T3_A07_D23_14)
unnamed: R189.3A, U4.U11 (IO_L19N_T3_A09_D25_VREF_14)
unnamed: R189.4A, U4.M18 (IO_L4N_T0_D05_14)
unnamed: R190.1A, U4.U18 (IO_L17N_T2_A13_D29_14)
unnamed: R190.2A, U4.T16 (IO_L15N_T2_DQS_DOUT_CSO_B_14)
unnamed: R190.3A, U4.U16 (IO_L18P_T2_A12_D28_14)
unnamed: R190.4A, U4.T18 (IO_L7N_T1_D10_14)
unnamed: R191.1A, U4.R16 (IO_L15P_T2_DQS_RDWR_B_14)
unnamed: R191.2A, U4.R17 (IO_L12N_T1_MRCC_14)
unnamed: R191.3A, U4.R18 (IO_L7P_T1_D09_14)
unnamed: R191.4A, U4.P14 (IO_L8N_T1_D12_14)
QSPI_CS: R50.1, U17.1 (~S)
QSPI_D0: R47.2, U17.5 (DQ0)
QSPI_D1: R48.2, U17.2 (DQ1)
QSPI_D2: R46.2, R49.2, U17.3 (~W/DQ2)
QSPI_D3: R45.2, R51.2, U17.7 (DQ3/~HOLD)
QSPI_SCLK: R52.1, U17.6 (C)
RP2040_CLK: U4.T14 (IO_L14P_T2_SRCC_14)
RP2040_PREQ: R171.2
RP2040_RX: U4.M17 (IO_L10N_T1_D15_14)
RP2040_SPARE: U4.P4 (IO_L14P_T2_SRCC_34)
RP2040_TX: U4.K18 (IO_L1N_T0_D01_DIN_14)
RPH_G0: R179.4B
RPH_G1: R183.4B
RPH_G2: R175.3B
RPH_G3: R175.4B
RPH_G4: R177.1B
RPH_G5: R181.1B
RPH_G6: R181.2B
RPH_G7: R183.3B
RPH_G8: R183.2B
RPH_G9: R179.2B
RPH_G10: R179.1B
RPH_G11: R179.3B
RPH_G12: R185.1B
RPH_G13: R181.3B
RPH_G16: R185.2B
RPH_G17: R177.2B
RPH_G18: R182.2B
RPH_G19: R181.4B
RPH_G20: R185.3B
RPH_G21: R185.4B
RPH_G22: R177.4B
RPH_G23: R182.3B
RPH_G24: R182.4B
RPH_G25: R183.1B, R212.1, R213.2
RPH_G26: R182.1B
RPH_G27: R177.3B
RPH_RXD0: R175.1B
RPH_TXD0: R175.2B
SCL0: R126.2, R170.2B
SCL1: R128.2, R170.4B
SDA0: R125.2, R170.1B
SDA1: R127.2, R170.3B
VCCIO: C80.1, R45.1, R46.1, R125.1, R126.1, R127.1, R128.1, R212.2, U17.8 (VCC)

Notes on the sheet:
TODO - may be 128 Mbit on final.
This SPI flash can be driven from both the FPGA and from the RP2040. Ideally placed between them with a sort of daisy-chain style routing FPGA-->SPI-->RP2040, as short as possible.
