newaetech/sonata-pcb/sonata-one/sonata_kicad_project/FPGA_IO15_16.kicad_sch

## KiCad design sonata-one/sonata_kicad_project/FPGA_IO15_16.kicad_sch (2025-01-31)

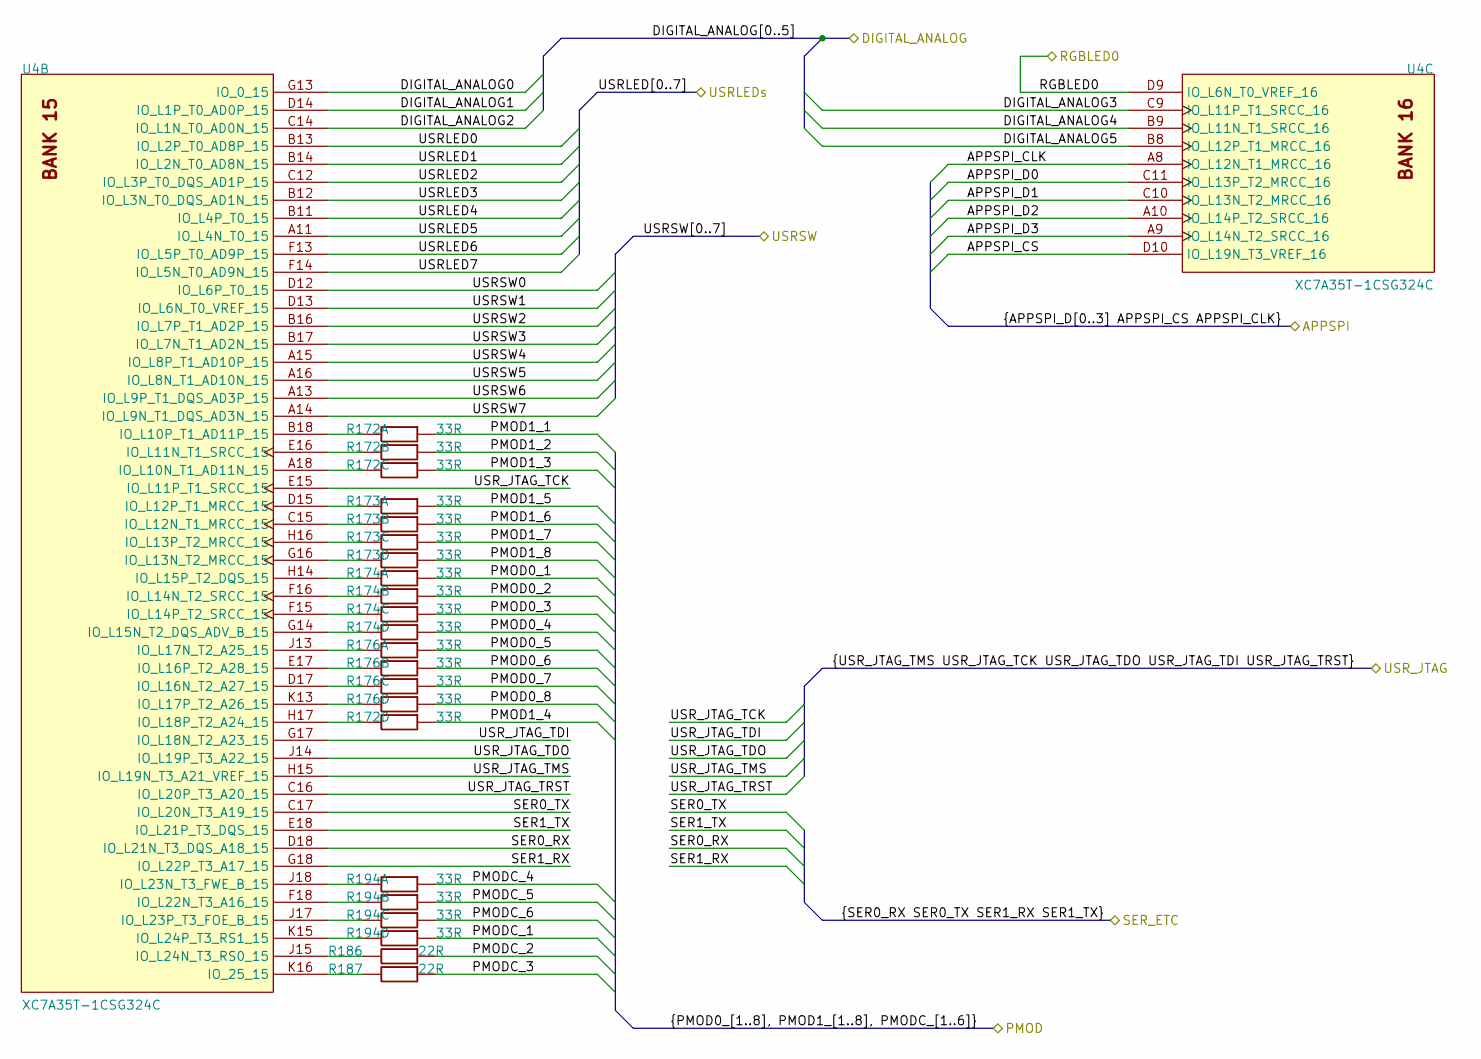
[picture p9: schematic FPGA_IO15_16.kicad_sch]

Parts:
R172, R173, R174, R176, R194: 33R; 741C083; MANUFACTURE PART NUMBER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 741C083330JP
R186, R187: 22R; RESC1005X40N; MANUFACTURE PART NUMBER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 RC0402FR-0722RL
U4: XC7A35T-1CSG324C; CSG324

Connections:
APPSPI_CLK: U4.A8 (IO_L12N_T1_MRCC_16)
APPSPI_CS: U4.D10 (IO_L19N_T3_VREF_16)
APPSPI_D0: U4.C11 (IO_L13P_T2_MRCC_16)
APPSPI_D1: U4.C10 (IO_L13N_T2_MRCC_16)
APPSPI_D2: U4.A10 (IO_L14P_T2_SRCC_16)
APPSPI_D3: U4.A9 (IO_L14N_T2_SRCC_16)
DIGITAL_ANALOG0: U4.G13 (IO_0_15)
DIGITAL_ANALOG1: U4.D14 (IO_L1P_T0_AD0P_15)
DIGITAL_ANALOG2: U4.C14 (IO_L1N_T0_AD0N_15)
DIGITAL_ANALOG3: U4.C9 (IO_L11P_T1_SRCC_16)
DIGITAL_ANALOG4: U4.B9 (IO_L11N_T1_SRCC_16)
DIGITAL_ANALOG5: U4.B8 (IO_L12P_T1_MRCC_16)
unnamed: R172.1A, U4.B18 (IO_L10P_T1_AD11P_15)
unnamed: R172.2A, U4.E16 (IO_L11N_T1_SRCC_15)
unnamed: R172.3A, U4.A18 (IO_L10N_T1_AD11N_15)
unnamed: R172.4A, U4.H17 (IO_L18P_T2_A24_15)
unnamed: R173.1A, U4.D15 (IO_L12P_T1_MRCC_15)
unnamed: R173.2A, U4.C15 (IO_L12N_T1_MRCC_15)
unnamed: R173.3A, U4.H16 (IO_L13P_T2_MRCC_15)
unnamed: R173.4A, U4.G16 (IO_L13N_T2_MRCC_15)
unnamed: R174.1A, U4.H14 (IO_L15P_T2_DQS_15)
unnamed: R174.2A, U4.F16 (IO_L14N_T2_SRCC_15)
unnamed: R174.3A, U4.F15 (IO_L14P_T2_SRCC_15)
unnamed: R174.4A, U4.G14 (IO_L15N_T2_DQS_ADV_B_15)
unnamed: R176.1A, U4.J13 (IO_L17N_T2_A25_15)
unnamed: R176.2A, U4.E17 (IO_L16P_T2_A28_15)
unnamed: R176.3A, U4.D17 (IO_L16N_T2_A27_15)
unnamed: R176.4A, U4.K13 (IO_L17P_T2_A26_15)
unnamed: R186.1, U4.J15 (IO_L24N_T3_RS0_15)
unnamed: R187.1, U4.K16 (IO_25_15)
unnamed: R194.1A, U4.J18 (IO_L23N_T3_FWE_B_15)
unnamed: R194.2A, U4.F18 (IO_L22N_T3_A16_15)
unnamed: R194.3A, U4.J17 (IO_L23P_T3_FOE_B_15)
unnamed: R194.4A, U4.K15 (IO_L24P_T3_RS1_15)
PMOD0_1: R174.1B
PMOD0_2: R174.2B
PMOD0_3: R174.3B
PMOD0_4: R174.4B
PMOD0_5: R176.1B
PMOD0_6: R176.2B
PMOD0_7: R176.3B
PMOD0_8: R176.4B
PMOD1_1: R172.1B
PMOD1_2: R172.2B
PMOD1_3: R172.3B
PMOD1_4: R172.4B
PMOD1_5: R173.1B
PMOD1_6: R173.2B
PMOD1_7: R173.3B
PMOD1_8: R173.4B
PMODC_1: R194.4B
PMODC_2: R186.2
PMODC_3: R187.2
PMODC_4: R194.1B
PMODC_5: R194.2B
PMODC_6: R194.3B
RGBLED0: U4.D9 (IO_L6N_T0_VREF_16)
SER0_RX: U4.D18 (IO_L21N_T3_DQS_A18_15)
SER0_TX: U4.C17 (IO_L20N_T3_A19_15)
SER1_RX: U4.G18 (IO_L22P_T3_A17_15)
SER1_TX: U4.E18 (IO_L21P_T3_DQS_15)
USRLED0: U4.B13 (IO_L2P_T0_AD8P_15)
USRLED1: U4.B14 (IO_L2N_T0_AD8N_15)
USRLED2: U4.C12 (IO_L3P_T0_DQS_AD1P_15)
USRLED3: U4.B12 (IO_L3N_T0_DQS_AD1N_15)
USRLED4: U4.B11 (IO_L4P_T0_15)
USRLED5: U4.A11 (IO_L4N_T0_15)
USRLED6: U4.F13 (IO_L5P_T0_AD9P_15)
USRLED7: U4.F14 (IO_L5N_T0_AD9N_15)
USRSW0: U4.D12 (IO_L6P_T0_15)
USRSW1: U4.D13 (IO_L6N_T0_VREF_15)
USRSW2: U4.B16 (IO_L7P_T1_AD2P_15)
USRSW3: U4.B17 (IO_L7N_T1_AD2N_15)
USRSW4: U4.A15 (IO_L8P_T1_AD10P_15)
USRSW5: U4.A16 (IO_L8N_T1_AD10N_15)
USRSW6: U4.A13 (IO_L9P_T1_DQS_AD3P_15)
USRSW7: U4.A14 (IO_L9N_T1_DQS_AD3N_15)
USR_JTAG_TCK: U4.E15 (IO_L11P_T1_SRCC_15)
USR_JTAG_TDI: U4.G17 (IO_L18N_T2_A23_15)
USR_JTAG_TDO: U4.J14 (IO_L19P_T3_A22_15)
USR_JTAG_TMS: U4.H15 (IO_L19N_T3_A21_VREF_15)
USR_JTAG_TRST: U4.C16 (IO_L20P_T3_A20_15)
