newaetech/sonata-pcb/sonata-one/sonata_kicad_project/FPGA_PWR.kicad_sch

## KiCad design sonata-one/sonata_kicad_project/FPGA_PWR.kicad_sch (2025-01-31)

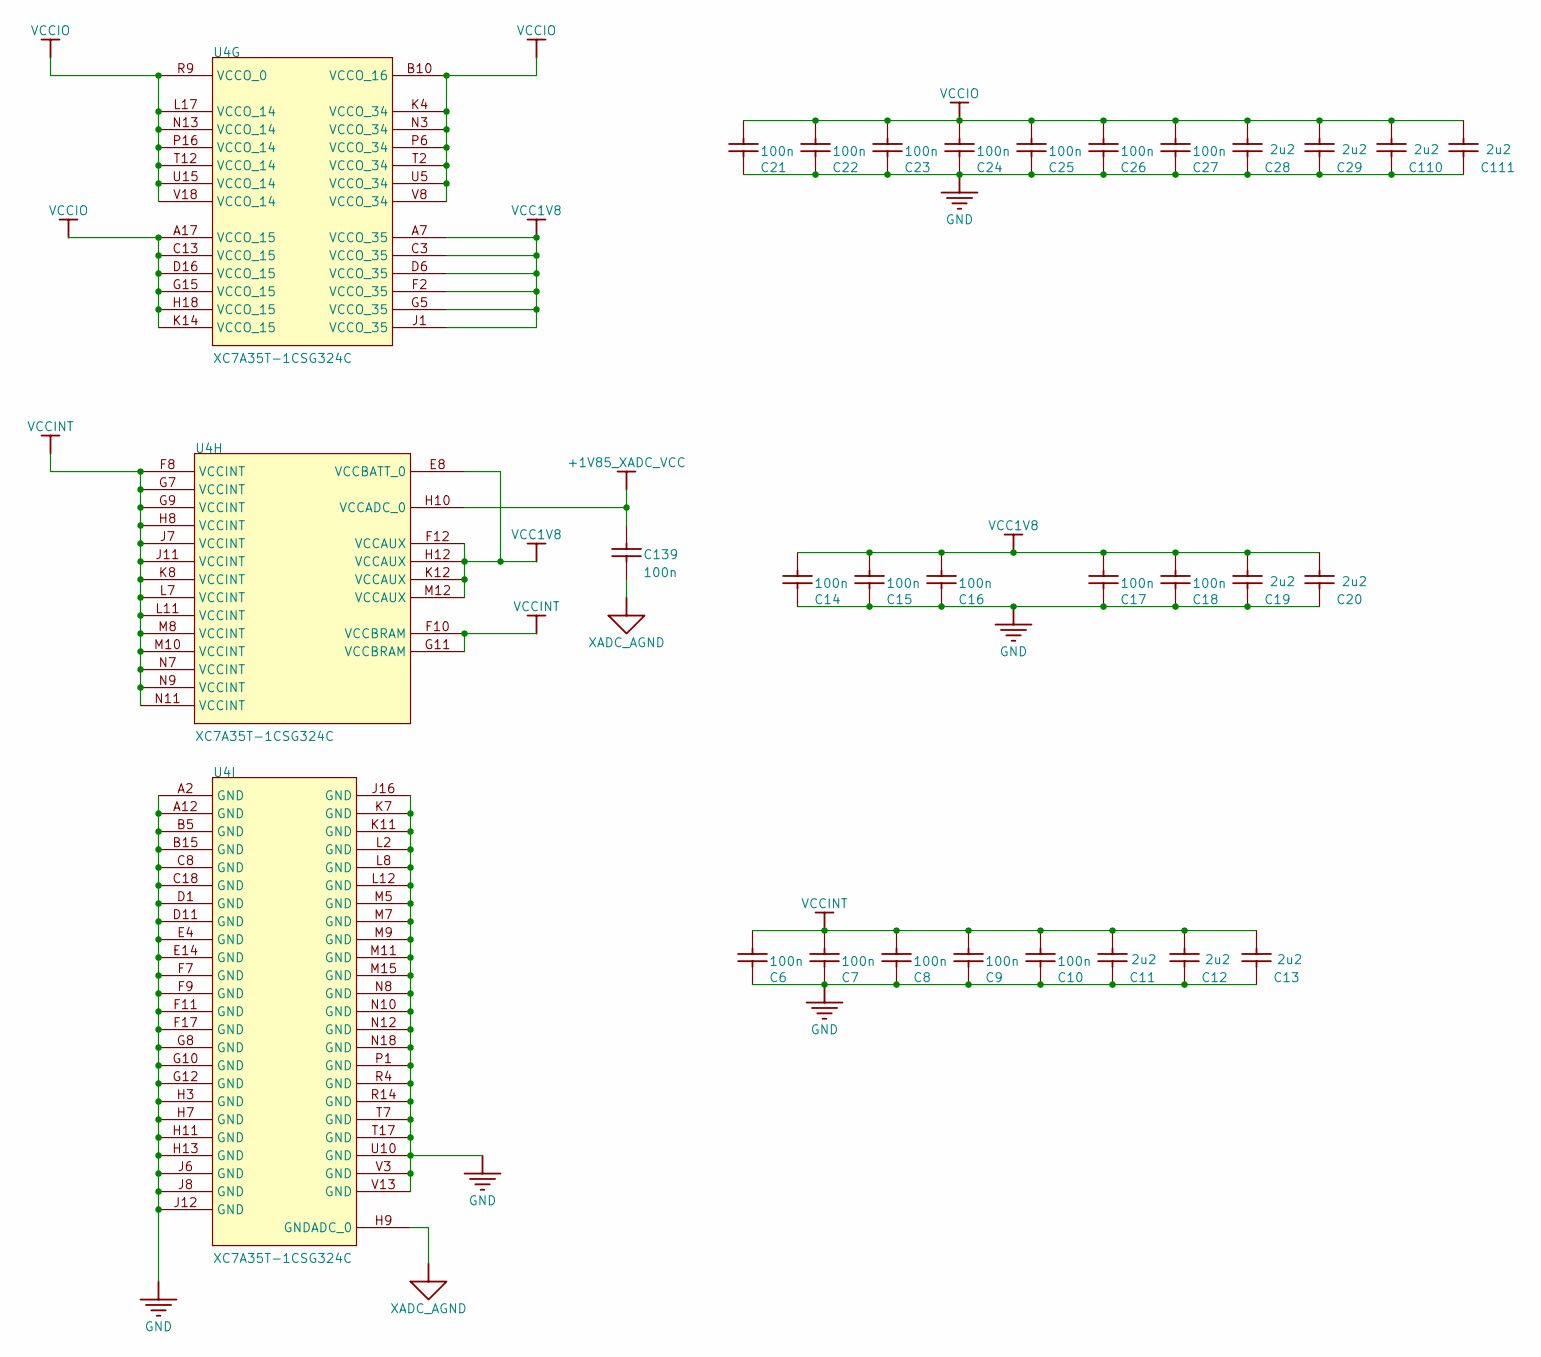
[picture p10: schematic FPGA_PWR.kicad_sch]

Parts:
C6, C7, C8, C9, C10, C14, C15, C16, C17, C18, C21, C22, C23, C24, C25, C26, C27, C139: 100n; CAPC0402_M; MANUFACTURE PART NUMBER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 CGA2B3X7R1V104K050BB
C11, C12, C13, C19, C20, C28, C29, C110, C111: 2u2; CAPC0603_M; MANUFACTURE PART NUMBER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 CL10B225KP8NNNC
U4: XC7A35T-1CSG324C; CSG324

Connections:
+1V85_XADC_VCC: C139.1, U4.H10 (VCCADC_0)
GND: C6.2, C7.2, C8.2, C9.2, C10.2, C11.2, C12.2, C13.2, C14.2, C15.2, C16.2, C17.2, C18.2, C19.2, C20.2, C21.2, C22.2, C23.2, C24.2, C25.2, C26.2, C27.2, C28.2, C29.2, C110.2, C111.2, U4.A2 (GND), U4.A12 (GND), U4.B5 (GND), U4.B15 (GND), U4.C8 (GND), U4.C18 (GND), U4.D1 (GND), U4.D11 (GND), U4.E4 (GND), U4.E14 (GND), U4.F7 (GND), U4.F9 (GND), U4.F11 (GND), U4.F17 (GND), U4.G8 (GND), U4.G10 (GND), U4.G12 (GND), U4.H3 (GND), U4.H7 (GND), U4.H11 (GND), U4.H13 (GND), U4.J6 (GND), U4.J8 (GND), U4.J12 (GND), U4.J16 (GND), U4.K7 (GND), U4.K11 (GND), U4.L2 (GND), U4.L8 (GND), U4.L12 (GND), U4.M5 (GND), U4.M7 (GND), U4.M9 (GND), U4.M11 (GND), U4.M15 (GND), U4.N8 (GND), U4.N10 (GND), U4.N12 (GND), U4.N18 (GND), U4.P1 (GND), U4.R4 (GND), U4.R14 (GND), U4.T7 (GND), U4.T17 (GND), U4.U10 (GND), U4.V3 (GND), U4.V13 (GND)
VCC1V8: C14.1, C15.1, C16.1, C17.1, C18.1, C19.1, C20.1, U4.A7 (VCCO_35), U4.C3 (VCCO_35), U4.D6 (VCCO_35), U4.E8 (VCCBATT_0), U4.F2 (VCCO_35), U4.F12 (VCCAUX), U4.G5 (VCCO_35), U4.H12 (VCCAUX), U4.J1 (VCCO_35), U4.K12 (VCCAUX), U4.M12 (VCCAUX)
VCCINT: C6.1, C7.1, C8.1, C9.1, C10.1, C11.1, C12.1, C13.1, U4.F8 (VCCINT), U4.F10 (VCCBRAM), U4.G7 (VCCINT), U4.G9 (VCCINT), U4.G11 (VCCBRAM), U4.H8 (VCCINT), U4.J7 (VCCINT), U4.J11 (VCCINT), U4.K8 (VCCINT), U4.L7 (VCCINT), U4.L11 (VCCINT), U4.M8 (VCCINT), U4.M10 (VCCINT), U4.N7 (VCCINT), U4.N9 (VCCINT), U4.N11 (VCCINT)
VCCIO: C21.1, C22.1, C23.1, C24.1, C25.1, C26.1, C27.1, C28.1, C29.1, C110.1, C111.1, U4.A17 (VCCO_15), U4.B10 (VCCO_16), U4.C13 (VCCO_15), U4.D16 (VCCO_15), U4.G15 (VCCO_15), U4.H18 (VCCO_15), U4.K4 (VCCO_34), U4.K14 (VCCO_15), U4.L17 (VCCO_14), U4.N3 (VCCO_34), U4.N13 (VCCO_14), U4.P6 (VCCO_34), U4.P16 (VCCO_14), U4.R9 (VCCO_0), U4.T2 (VCCO_34), U4.T12 (VCCO_14), U4.U5 (VCCO_34), U4.U15 (VCCO_14), U4.V8 (VCCO_34), U4.V18 (VCCO_14)
XADC_AGND: C139.2, U4.H9 (GNDADC_0)
