newaetech/sonata-pcb/sonata-one/sonata_kicad_project/FTDI_Debug.kicad_sch

## KiCad design sonata-one/sonata_kicad_project/FTDI_Debug.kicad_sch (2025-01-31)

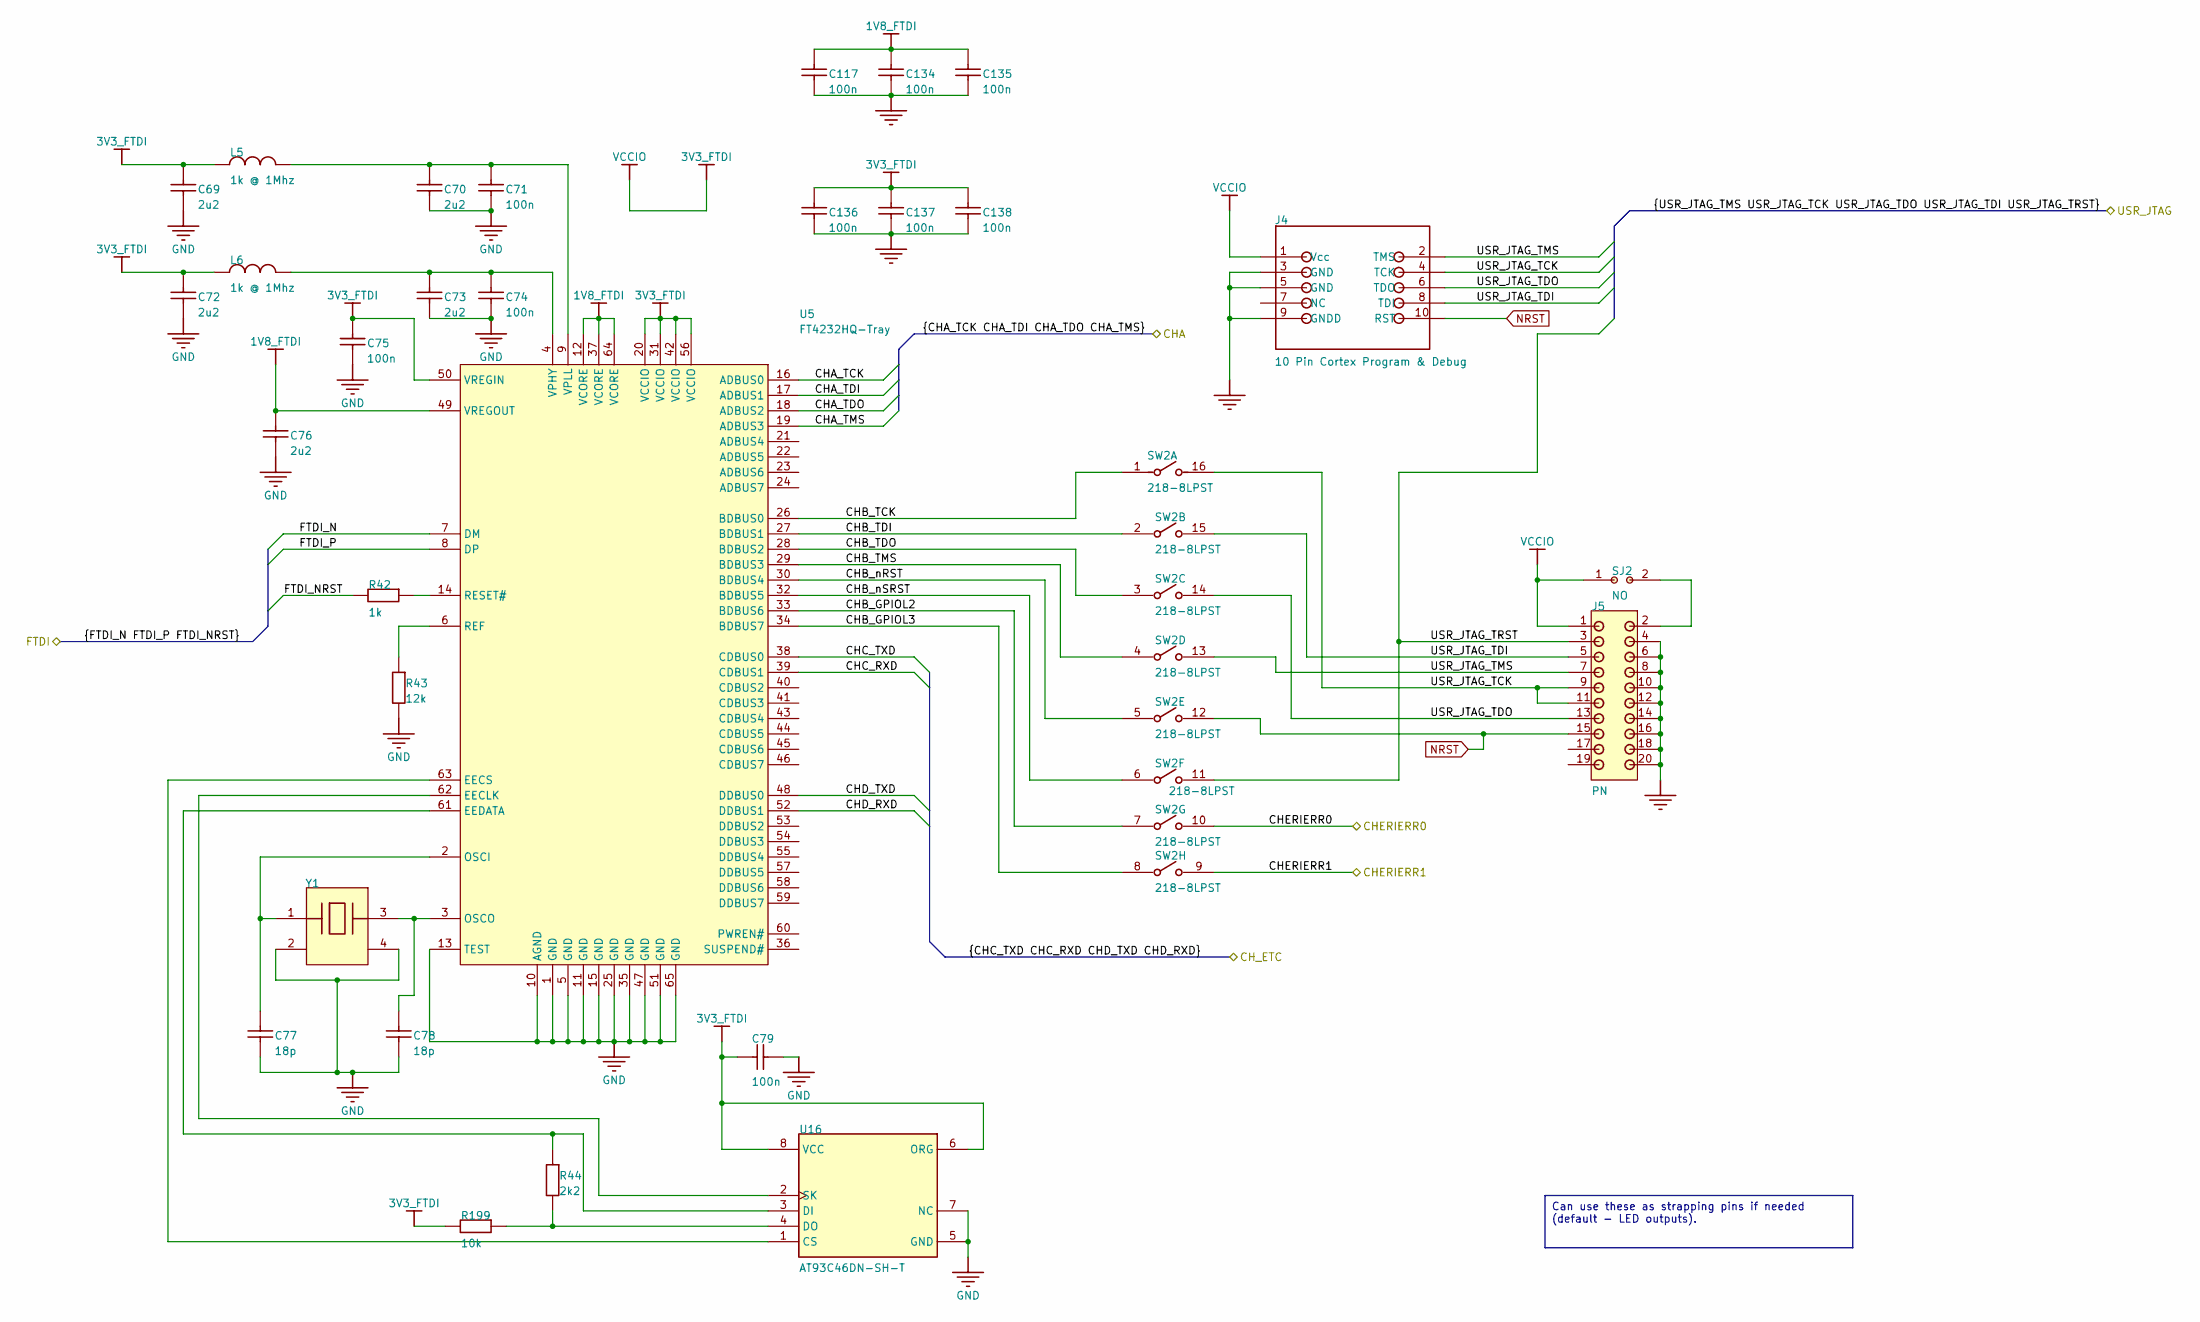
[picture p11: schematic FTDI_Debug.kicad_sch]

Parts:
C69, C70, C72, C73, C76: 2u2; CAPC0603_M; MANUFACTURE PART NUMBER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 CL10B225KP8NNNC
C71, C74, C75, C79, C117, C134, C135, C136, C137, C138: 100n; CAPC0402_M; MANUFACTURE PART NUMBER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 CGA2B3X7R1V104K050BB
C77, C78: 18p; CAPC0402_M; MANUFACTURE PART NUMBER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 GRM1555C1H180JA01D
J4: 10 Pin Cortex Program & Debug; 0.5mm_SMD_Header_5x2; MANUFACTURE PART NUMBER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 20021121-00010C4LF
J5: PN; CONN_10x2_SHROUDED_2.54mm
L5, L6: 1k @ 1Mhz; IND_0603; MANUFACTURE PART NUMBER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 FBMH1608HM102-T FBMH1608HM102-T FBMH160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
R42: 1k; RESC1005X40N; MANUFACTURE PART NUMBER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 RC0402FR-071KL
R43: 12k; RESC1608X55N; MANUFACTURE PART NUMBER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 RC0603FR-0712KL
R44: 2k2; RESC1005X40N; MANUFACTURE PART NUMBER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 RC0402FR-072K2L
R199: 10k; RESC1005X40N; MANUFACTURE PART NUMBER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 RC0402FR-0710KL
SJ2: NO; SJ_2S_NO
SW2: 218-8LPST; FP-218-8LPST-MFG
U5: FT4232HQ-Tray; QFN64_2_N
U16: AT93C46DN-SH-T; FP-C04-057-SN-MFG
Y1: H130B-12.000-16-2525-EXT-TR; 5x3.2MM XTAL; MANUFACTURE PART NUMBER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 H130B-12.000-16-2525-EXT-TR

Connections:
1V8_FTDI: C76.1, C117.1, C134.1, C135.1, U5.12 (VCORE), U5.37 (VCORE), U5.49 (VREGOUT), U5.64 (VCORE)
3V3_FTDI: C69.1, C72.1, C75.1, C79.1, C136.1, C137.1, C138.1, J4.1 (Vcc), J5.1, L5.1, L6.1, R199.1, SJ2.1, U5.20 (VCCIO), U5.31 (VCCIO), U5.42 (VCCIO), U5.50 (VREGIN), U5.56 (VCCIO), U16.6 (ORG), U16.8 (VCC)
CHA_TCK: U5.16 (ADBUS0)
CHA_TDI: U5.17 (ADBUS1)
CHA_TDO: U5.18 (ADBUS2)
CHA_TMS: U5.19 (ADBUS3)
CHB_GPIOL2: SW2.7, U5.33 (BDBUS6)
CHB_GPIOL3: SW2.8, U5.34 (BDBUS7)
CHB_TCK: SW2.1, U5.26 (BDBUS0)
CHB_TDI: SW2.2, U5.27 (BDBUS1)
CHB_TDO: SW2.3, U5.28 (BDBUS2)
CHB_TMS: SW2.4, U5.29 (BDBUS3)
CHB_nRST: SW2.5, U5.30 (BDBUS4)
CHB_nSRST: SW2.6, U5.32 (BDBUS5)
CHC_RXD: U5.39 (CDBUS1)
CHC_TXD: U5.38 (CDBUS0)
CHD_RXD: U5.52 (DDBUS1)
CHD_TXD: U5.48 (DDBUS0)
CHERIERR0: SW2.10
CHERIERR1: SW2.9
FTDI_N: U5.7 (DM)
FTDI_NRST: R42.2
FTDI_P: U5.8 (DP)
GND: C69.2, C70.2, C71.2, C72.2, C73.2, C74.2, C75.2, C76.2, C77.2, C78.2, C79.2, C117.2, C134.2, C135.2, C136.2, C137.2, C138.2, J4.3 (GND), J4.5 (GND), J4.9 (GNDD), J5.4, J5.6, J5.8, J5.10, J5.12 (10), J5.14 (10), J5.16 (10), J5.18 (10), J5.20 (10), R43.2, U5.1 (GND), U5.5 (GND), U5.10 (AGND), U5.11 (GND), U5.13 (TEST), U5.15 (GND), U5.25 (GND), U5.35 (GND), U5.47 (GND), U5.51 (GND), U5.65 (GND), U16.5 (GND), U16.7 (NC), Y1.2, Y1.4
NRST: J4.10 (RST), J5.15 (9), SW2.12
unnamed: C70.1, C71.1, L5.2, U5.9 (VPLL)
unnamed: C73.1, C74.1, L6.2, U5.4 (VPHY)
unnamed: C77.1, U5.2 (OSCI), Y1.1
unnamed: C78.1, U5.3 (OSCO), Y1.3
unnamed: J5.2, SJ2.2
unnamed: R42.1, U5.14 (RESET#)
unnamed: R43.1, U5.6 (REF)
unnamed: R44.1, U5.61 (EEDATA), U16.3 (DI)
unnamed: R44.2, R199.2, U16.4 (DO)
unnamed: U5.63 (EECS), U16.1 (CS)
unnamed: U5.62 (EECLK), U16.2 (SK)
USR_JTAG_TCK: J4.4 (TCK), J5.9, J5.11 (9), SW2.16
USR_JTAG_TDI: J4.8 (TDI), J5.5, SW2.15
USR_JTAG_TDO: J4.6 (TDO), J5.13 (9), SW2.14
USR_JTAG_TMS: J4.2 (TMS), J5.7, SW2.13
USR_JTAG_TRST: J5.3, SW2.11

Notes on the sheet:
Can use these as strapping pins if needed (default - LED outputs).
