newaetech/sonata-pcb/sonata-one/sonata_kicad_project/Header_Pins.kicad_sch

## KiCad design sonata-one/sonata_kicad_project/Header_Pins.kicad_sch (2025-01-31)

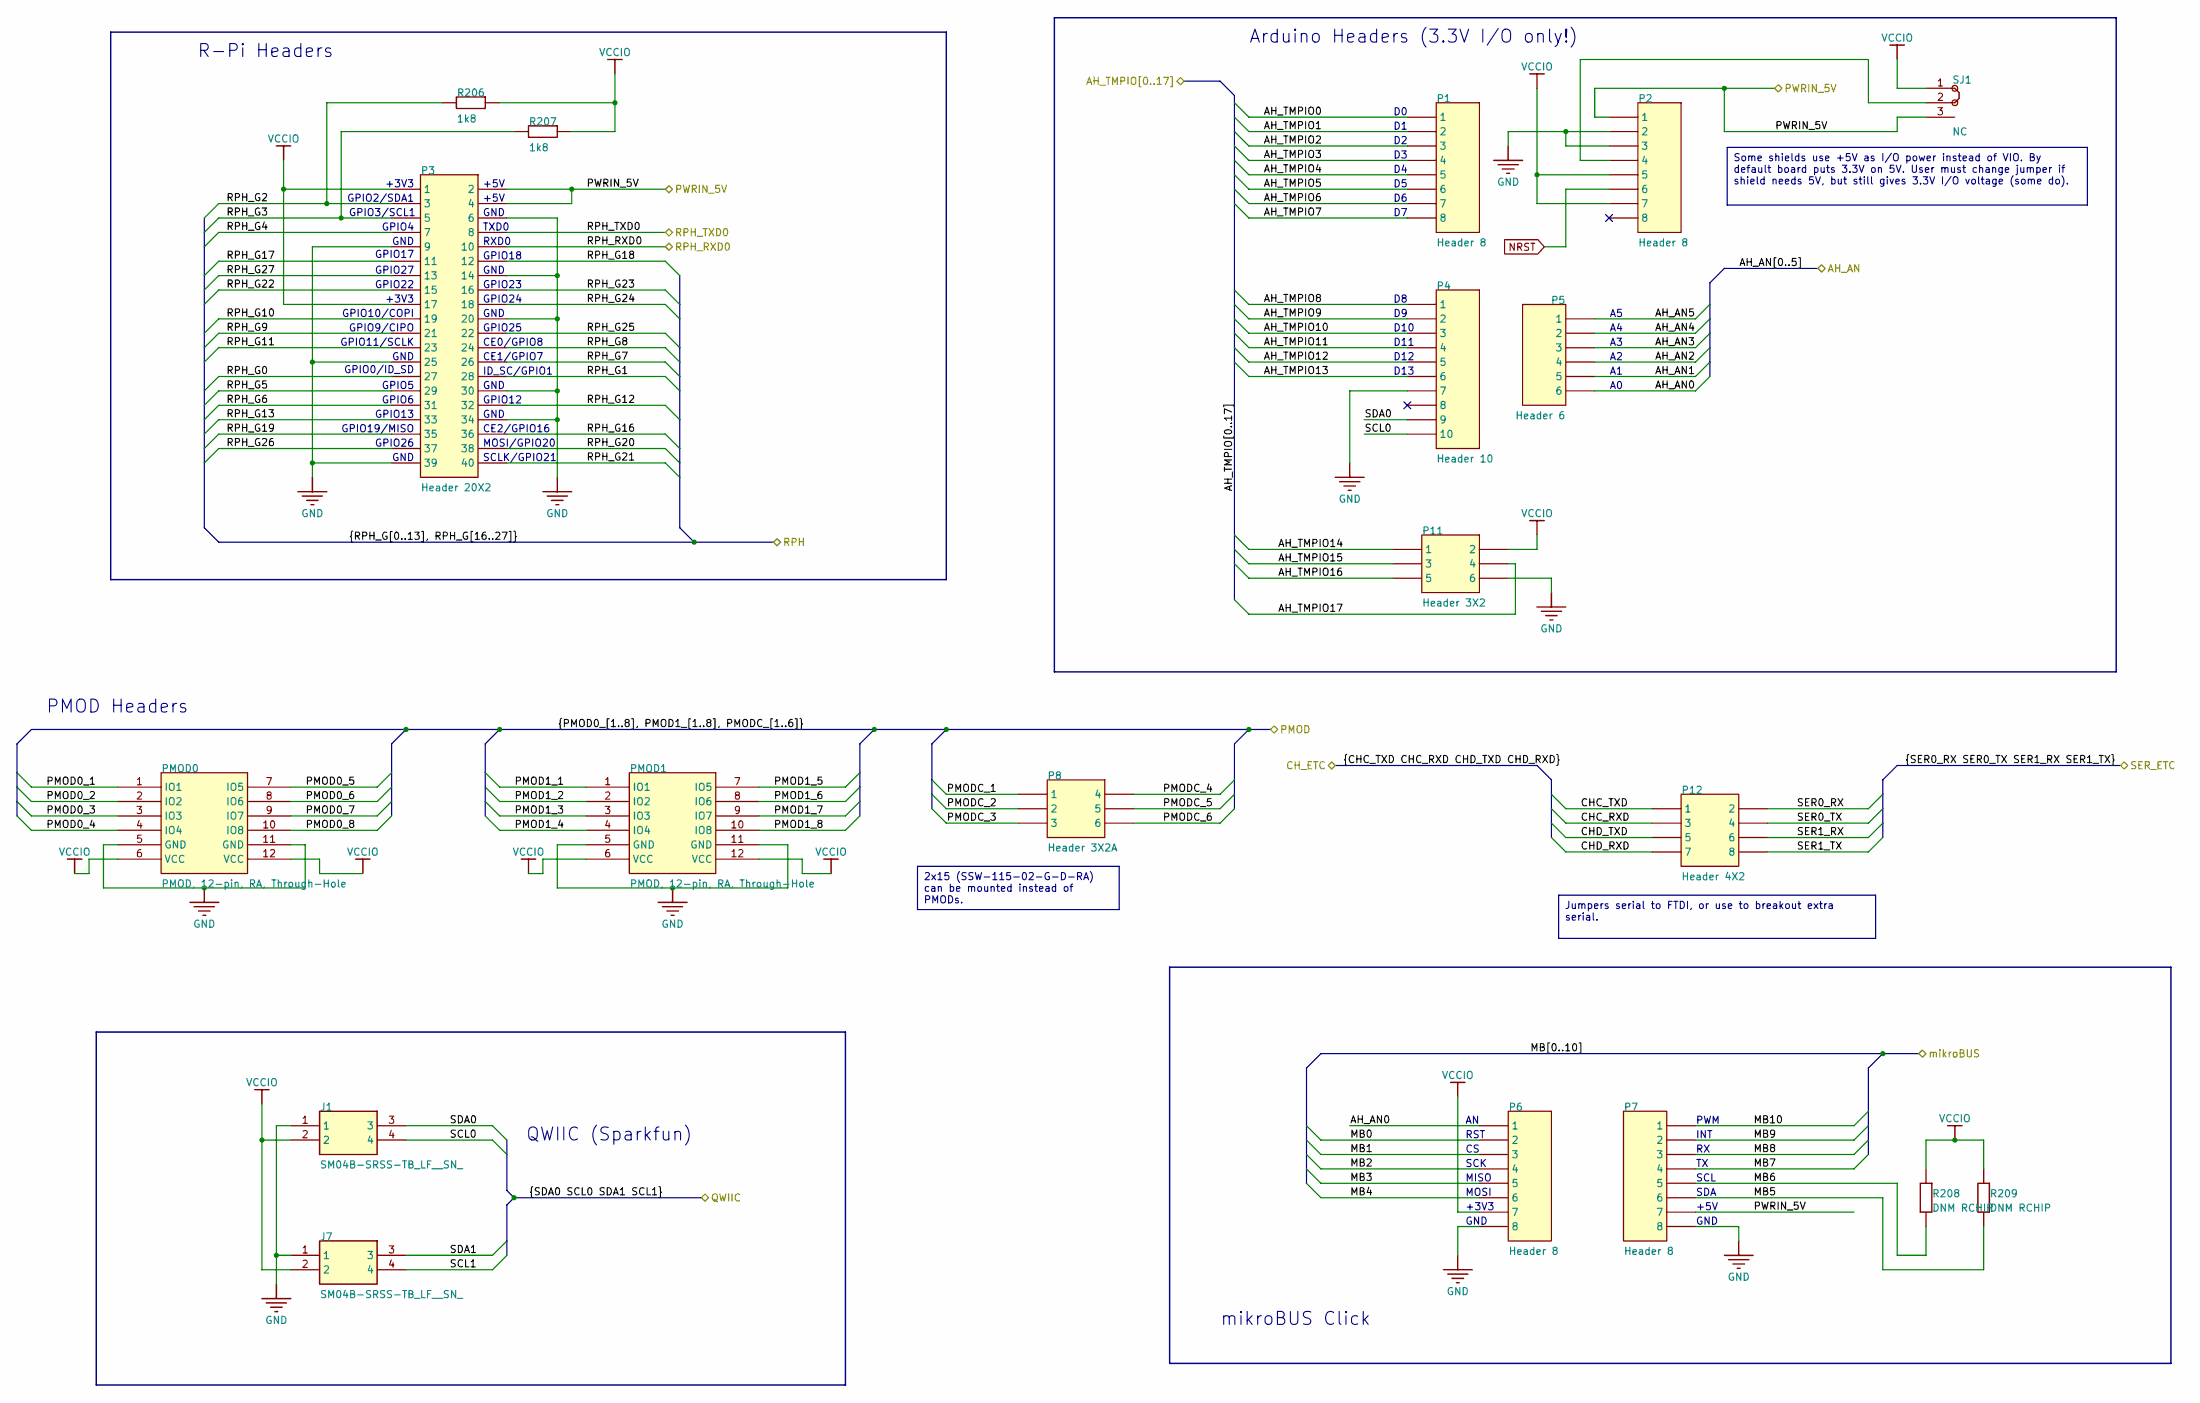
[picture p12: schematic Header_Pins.kicad_sch]

Parts:
J1, J7: SM04B-SRSS-TB_LF__SN_; SM04B-SRSS-TB(LFSN)
P1, P2, P6, P7: Header 8; HDR1X8_SLW-108-01-T-S
P3: Header 20X2; HDR2X20_861400402YO2LF
P4: Header 10; HDR1X10_SLW-110-01-T-S
P5: Header 6; HDR1X6_SLW-106-01-T-S
P8: Header 3X2A; HDR2X3_CEN
P11: Header 3X2; HDR2X3_XG8T-0641
P12: Header 4X2; HDR2X4_XG8T-0841
PMOD0, PMOD1: PMOD, 12-pin, RA, Through-Hole; SAMTEC_SSW_106_02_X_D_RA_PMOD
R206, R207: 1k8; RESC1608X55N; MANUFACTURE PART NUMBER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 RC0603FR-071K8L
R208, R209: DNM RCHIP; RESC1608X55N
SJ1: NC; SJ_3S_NC12

Connections:
AH_AN0: P5.6, P6.1
AH_AN1: P5.5
AH_AN2: P5.4
AH_AN3: P5.3
AH_AN4: P5.2
AH_AN5: P5.1
AH_TMPIO0: P1.1
AH_TMPIO1: P1.2
AH_TMPIO2: P1.3
AH_TMPIO3: P1.4
AH_TMPIO4: P1.5
AH_TMPIO5: P1.6
AH_TMPIO6: P1.7
AH_TMPIO7: P1.8
AH_TMPIO8: P4.1
AH_TMPIO9: P4.2
AH_TMPIO10: P4.3
AH_TMPIO11: P4.4
AH_TMPIO12: P4.5
AH_TMPIO13: P4.6
AH_TMPIO14: P11.1
AH_TMPIO15: P11.3
AH_TMPIO16: P11.5
AH_TMPIO17: P11.4
CHC_RXD: P12.3
CHC_TXD: P12.1
CHD_RXD: P12.7
CHD_TXD: P12.5
GND: J1.1, J7.1, P2.2, P2.3, P3.6, P3.9, P3.14, P3.20, P3.25, P3.30, P3.34, P3.39, P4.7, P6.8, P7.8, P11.6, PMOD0.5 (GND), PMOD0.11 (GND), PMOD1.5 (GND), PMOD1.11 (GND)
MB0: P6.2
MB1: P6.3
MB2: P6.4
MB3: P6.5
MB4: P6.6
MB5: P7.6, R209.2
MB6: P7.5, R208.2
MB7: P7.4
MB8: P7.3
MB9: P7.2
MB10: P7.1
NRST: P2.6
unnamed: P2.4, SJ1.2
PMOD0_1: PMOD0.1 (IO1)
PMOD0_2: PMOD0.2 (IO2)
PMOD0_3: PMOD0.3 (IO3)
PMOD0_4: PMOD0.4 (IO4)
PMOD0_5: PMOD0.7 (IO5)
PMOD0_6: PMOD0.8 (IO6)
PMOD0_7: PMOD0.9 (IO7)
PMOD0_8: PMOD0.10 (IO8)
PMOD1_1: PMOD1.1 (IO1)
PMOD1_2: PMOD1.2 (IO2)
PMOD1_3: PMOD1.3 (IO3)
PMOD1_4: PMOD1.4 (IO4)
PMOD1_5: PMOD1.7 (IO5)
PMOD1_6: PMOD1.8 (IO6)
PMOD1_7: PMOD1.9 (IO7)
PMOD1_8: PMOD1.10 (IO8)
PMODC_1: P8.1
PMODC_2: P8.2
PMODC_3: P8.3
PMODC_4: P8.4
PMODC_5: P8.5
PMODC_6: P8.6
PWRIN_5V: P2.1, P3.2, P3.4, P7.7, SJ1.3
RPH_G0: P3.27
RPH_G1: P3.28
RPH_G2: P3.3, R206.1
RPH_G3: P3.5, R207.1
RPH_G4: P3.7
RPH_G5: P3.29
RPH_G6: P3.31
RPH_G7: P3.26
RPH_G8: P3.24
RPH_G9: P3.21
RPH_G10: P3.19
RPH_G11: P3.23
RPH_G12: P3.32
RPH_G13: P3.33
RPH_G16: P3.36
RPH_G17: P3.11
RPH_G18: P3.12
RPH_G19: P3.35
RPH_G20: P3.38
RPH_G21: P3.40
RPH_G22: P3.15
RPH_G23: P3.16
RPH_G24: P3.18
RPH_G25: P3.22
RPH_G26: P3.37
RPH_G27: P3.13
RPH_RXD0: P3.10
RPH_TXD0: P3.8
SCL0: J1.4, P4.10
SCL1: J7.4
SDA0: J1.3, P4.9
SDA1: J7.3
SER0_RX: P12.2
SER0_TX: P12.4
SER1_RX: P12.6
SER1_TX: P12.8
VCCIO: J1.2, J7.2, P2.5, P2.7, P3.1, P3.17, P6.7, P11.2, PMOD0.6 (VCC), PMOD0.12 (VCC), PMOD1.6 (VCC), PMOD1.12 (VCC), R206.2, R207.2, R208.1, R209.1, SJ1.1

Notes on the sheet:
Jumpers serial to FTDI, or use to breakout extra serial.
2x15 (SSW-115-02-G-D-RA) can be mounted instead of PMODs.
Some shields use +5V as I/O power instead of VIO. By default board puts 3.3V on 5V. User must change jumper if shield needs 5V, but still gives 3.3V I/O voltage (some do).
GPIO4
+3V3
GPIO26
SDA
TXD0
RST
GPIO5
GND
GPIO9/CIPO
SCL
SCK
PMOD Headers
QWIIC (Sparkfun)
GPIO10/COPI
GPIO25
R-Pi Headers
GPIO2/SDA1
CE2/GPIO16
GPIO3/SCL1
GPIO18
PWM
mikroBUS Click
GPIO19/MISO
RXD0
MISO
GPIO6
GPIO13
INT
D10
GPIO23
GPIO12
CE0/GPIO8
Arduino Headers (3.3V I/O only!)
D12
CE1/GPIO7
+5V
D13
GPIO17
SCLK/GPIO21
GPIO24
GPIO0/ID_SD
MOSI
ID_SC/GPIO1
D11
GPIO11/SCLK
MOSI/GPIO20
GPIO22
GPIO27
