newaetech/sonata-pcb/sonata-one/sonata_kicad_project/HyperRAM.kicad_sch

## KiCad design sonata-one/sonata_kicad_project/HyperRAM.kicad_sch (2025-01-31)

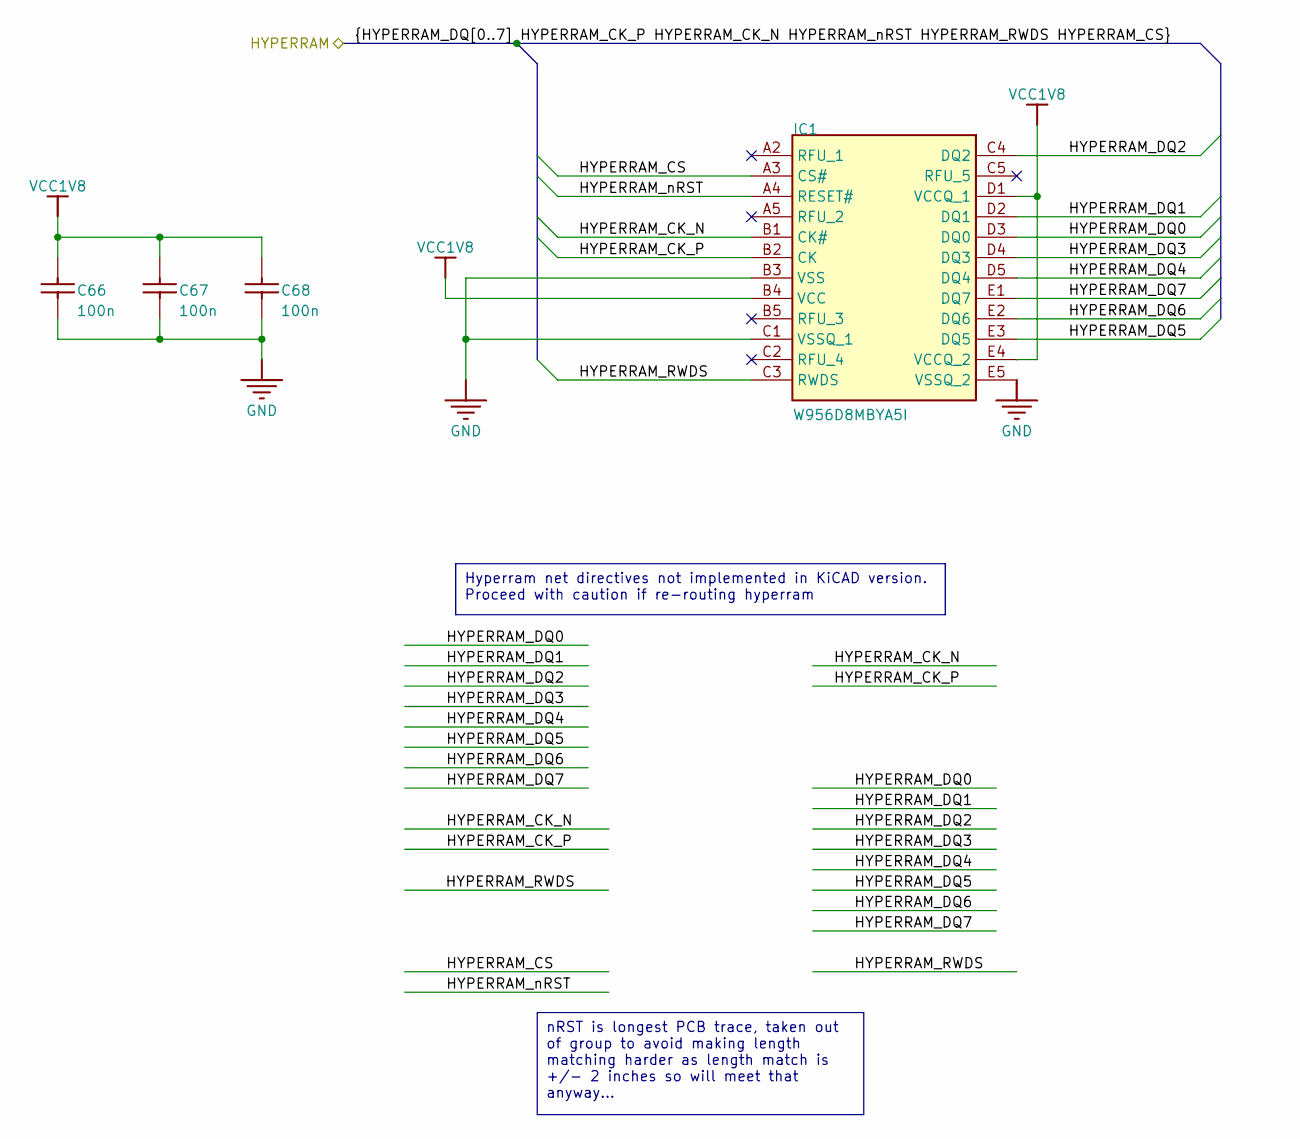
[picture p13: schematic HyperRAM.kicad_sch]

Parts:
C66, C67, C68: 100n; CAPC0402_M; MANUFACTURE PART NUMBER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 CGA2B3X7R1V104K050BB
IC1: W956D8MBYA5I; BGA24C100P5X5_600X800X120

Connections:
GND: C66.2, C67.2, C68.2, IC1.B3 (VSS), IC1.C1 (VSSQ_1), IC1.E5 (VSSQ_2)
HYPERRAM_CK_N: IC1.B1 (CK#)
HYPERRAM_CK_P: IC1.B2 (CK)
HYPERRAM_CS: IC1.A3 (CS#)
HYPERRAM_DQ0: IC1.D3 (DQ0)
HYPERRAM_DQ1: IC1.D2 (DQ1)
HYPERRAM_DQ2: IC1.C4 (DQ2)
HYPERRAM_DQ3: IC1.D4 (DQ3)
HYPERRAM_DQ4: IC1.D5 (DQ4)
HYPERRAM_DQ5: IC1.E3 (DQ5)
HYPERRAM_DQ6: IC1.E2 (DQ6)
HYPERRAM_DQ7: IC1.E1 (DQ7)
HYPERRAM_RWDS: IC1.C3 (RWDS)
HYPERRAM_nRST: IC1.A4 (RESET#)
VCC1V8: C66.1, C67.1, C68.1, IC1.B4 (VCC), IC1.D1 (VCCQ_1), IC1.E4 (VCCQ_2)

Notes on the sheet:
Hyperram net directives not implemented in KiCAD version. Proceed with caution if re-routing hyperram
nRST is longest PCB trace, taken out of group to avoid making length matching harder as length match is +/- 2 inches so will meet that anyway...
