newaetech/sonata-pcb/sonata-one/sonata_kicad_project/LCD.kicad_sch

## KiCad design sonata-one/sonata_kicad_project/LCD.kicad_sch (2025-01-31)

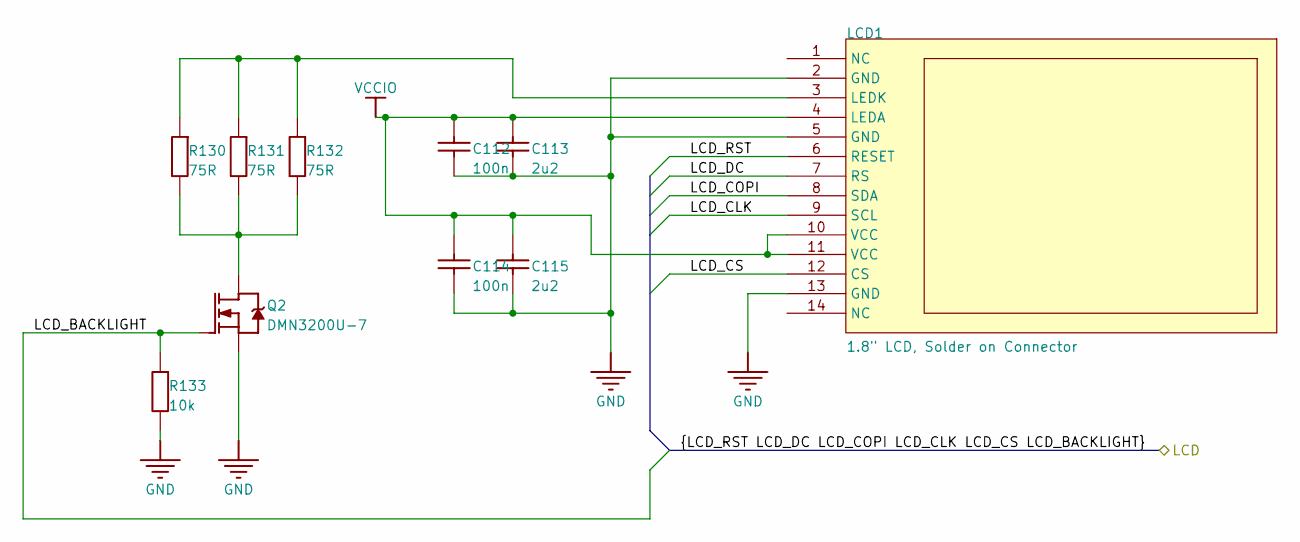
[picture p14: schematic LCD.kicad_sch]

Parts:
C112, C114: 100n; CAPC0402_M; MANUFACTURE PART NUMBER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 CGA2B3X7R1V104K050BB
C113, C115: 2u2; CAPC0603_M; MANUFACTURE PART NUMBER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 EMK107BJ225KA-T
LCD1: 1.8" LCD, Solder on Connector; ADAFRUIT618
Q2: DMN3200U-7; SOT95P245X110-3M; MANUFACTURE PART NUMBER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 DMN3200U-7
R130, R131, R132: 75R; RESC2012X70N; MANUFACTURE PART NUMBER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 RC0805FR-0775RL
R133: 10k; RESC1005X40N; MANUFACTURE PART NUMBER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 RC0402FR-0710KL

Connections:
GND: C112.2, C113.2, C114.2, C115.2, LCD1.2 (GND), LCD1.5 (GND), LCD1.13 (GND), Q2.2 (S), R133.2
LCD_BACKLIGHT: Q2.1 (G), R133.1
LCD_CLK: LCD1.9 (SCL)
LCD_COPI: LCD1.8 (SDA)
LCD_CS: LCD1.12 (CS)
LCD_DC: LCD1.7 (RS)
LCD_RST: LCD1.6 (RESET)
unnamed: LCD1.3 (LEDK), R130.1, R131.1, R132.1
unnamed: Q2.3 (D), R130.2, R131.2, R132.2
VCCIO: C112.1, C113.1, C114.1, C115.1, LCD1.4 (LEDA), LCD1.10 (VCC), LCD1.11 (VCC)
