newaetech/sonata-pcb/sonata-one/sonata_kicad_project/LEDs_Switches.kicad_sch

## KiCad design sonata-one/sonata_kicad_project/LEDs_Switches.kicad_sch (2025-01-31)

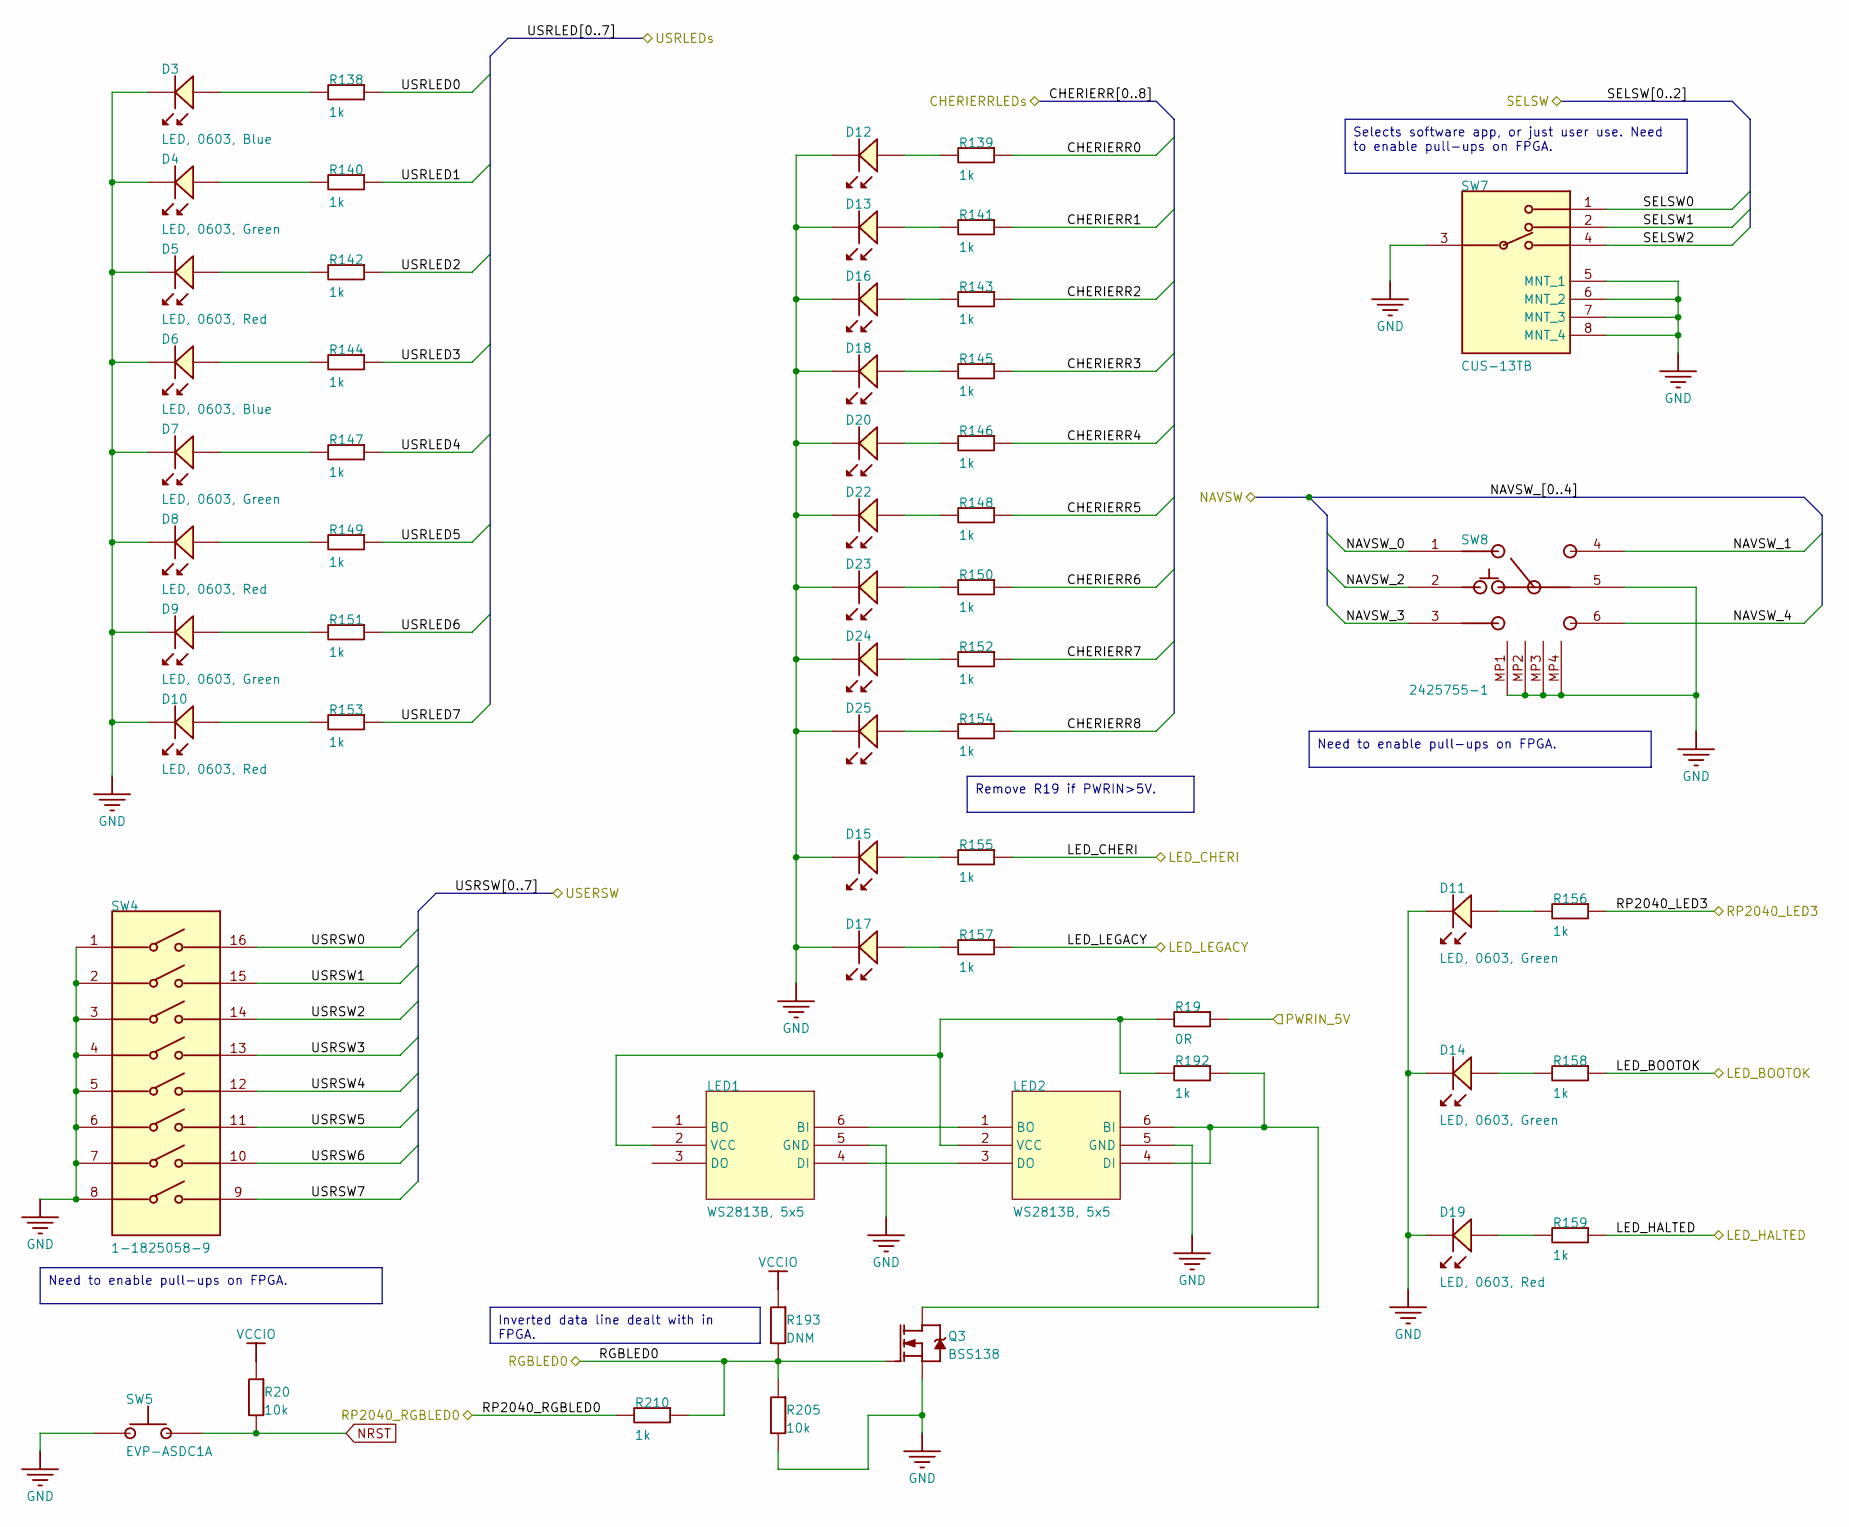
[picture p15: schematic LEDs_Switches.kicad_sch]

Parts:
D3, D6: LED, 0603, Blue; LED-0603-BLUE; MANUFACTURE PART NUMBER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 APT1608QBC/D
D4, D7, D9, D11, D14, D15: LED, 0603, Green; LED-0603-GREEN; MANUFACTURE PART NUMBER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 APT1608CGCK
D5, D8, D10, D12, D13, D16, D17, D18, D19, D20, D22, D23, D24, D25: LED, 0603, Red; LED-0603-RED; MANUFACTURE PART NUMBER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 APT1608SURCK
LED1, LED2: WS2813B, 5x5; WS2813B_5x5; MANUFACTURE PART NUMBER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 601000200
Q3: BSS138; SOT95P245X110-3M; MANUFACTURE PART NUMBER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 BSS138
R19: 0R; RESC1608X55N; MANUFACTURE PART NUMBER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 RC0603FR-070RL
R20, R205: 10k; RESC1005X40N; MANUFACTURE PART NUMBER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 RC0402FR-0710KL
R138, R139, R140, R141, R142, R143, R144, R145, R146, R147, R148, R149, R150, R151, R152, R153, R154, R155, R156, R157, R158, R159, R192, R210: 1k; RESC1005X40N; MANUFACTURE PART NUMBER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 RC0402FR-071KL
R193: DNM; RESC1005X40N
SW4: 1-1825058-9; FP-1-1825058-9-MFG
SW5: EVP-ASDC1A; EVPAS; MANUFACTURE PART NUMBER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 EVP-ASDC1A
SW7: CUS-13TB; FP-CUS-13TB-MFG
SW8: 2425755-1; MANUFACTURE PART NUMBER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 2425755-1

Connections:
CHERIERR0: R139.1
CHERIERR1: R141.1
CHERIERR2: R143.1
CHERIERR3: R145.1
CHERIERR4: R146.1
CHERIERR5: R148.1
CHERIERR6: R150.1
CHERIERR7: R152.1
CHERIERR8: R154.1
GND: D3.K, D4.K, D5.K, D6.K, D7.K, D8.K, D9.K, D10.K, D11.K, D12.K, D13.K, D14.K, D15.K, D16.K, D17.K, D18.K, D19.K, D20.K, D22.K, D23.K, D24.K, D25.K, LED1.5 (GND), LED2.5 (GND), Q3.2 (S), R205.2, SW4.1, SW4.2, SW4.3, SW4.4, SW4.5, SW4.6, SW4.7, SW4.8, SW5.1, SW7.3 (C), SW7.5 (MNT_1), SW7.6 (MNT_2), SW7.7 (MNT_3), SW7.8 (MNT_4), SW8.5, SW8.MP1, SW8.MP2, SW8.MP3, SW8.MP4
LED_BOOTOK: R158.1
LED_CHERI: R155.1
LED_HALTED: R159.1
LED_LEGACY: R157.1
NAVSW_0: SW8.1
NAVSW_1: SW8.4
NAVSW_2: SW8.2
NAVSW_3: SW8.3
NAVSW_4: SW8.6
NRST: R20.2, SW5.2
unnamed: D3.A, R138.2
unnamed: D4.A, R140.2
unnamed: D5.A, R142.2
unnamed: D6.A, R144.2
unnamed: D7.A, R147.2
unnamed: D8.A, R149.2
unnamed: D9.A, R151.2
unnamed: D10.A, R153.2
unnamed: D11.A, R156.2
unnamed: D12.A, R139.2
unnamed: D13.A, R141.2
unnamed: D14.A, R158.2
unnamed: D15.A, R155.2
unnamed: D16.A, R143.2
unnamed: D17.A, R157.2
unnamed: D18.A, R145.2
unnamed: D19.A, R159.2
unnamed: D20.A, R146.2
unnamed: D22.A, R148.2
unnamed: D23.A, R150.2
unnamed: D24.A, R152.2
unnamed: D25.A, R154.2
unnamed: LED1.2 (VCC), LED2.2 (VCC), R19.1, R192.1
unnamed: LED1.4 (DI), LED2.3 (DO)
unnamed: LED1.6 (BI), LED2.1 (BO)
unnamed: LED2.4 (DI), LED2.6 (BI), Q3.3 (D), R192.2
PWRIN_5V: R19.2
RGBLED0: Q3.1 (G), R193.2, R205.1, R210.1
RP2040_LED3: R156.1
RP2040_RGBLED0: R210.2
SELSW0: SW7.1
SELSW1: SW7.2
SELSW2: SW7.4
USRLED0: R138.1
USRLED1: R140.1
USRLED2: R142.1
USRLED3: R144.1
USRLED4: R147.1
USRLED5: R149.1
USRLED6: R151.1
USRLED7: R153.1
USRSW0: SW4.16
USRSW1: SW4.15
USRSW2: SW4.14
USRSW3: SW4.13
USRSW4: SW4.12
USRSW5: SW4.11
USRSW6: SW4.10
USRSW7: SW4.9
VCCIO: R20.1, R193.1

Notes on the sheet:
Need to enable pull-ups on FPGA.
Inverted data line dealt with in FPGA.
Remove R19 if PWRIN>5V.
Selects software app, or just user use. Need to enable pull-ups on FPGA.
