newaetech/sonata-pcb/sonata-one/sonata_kicad_project/Main_USB.kicad_sch

## KiCad design sonata-one/sonata_kicad_project/Main_USB.kicad_sch (2025-01-31)

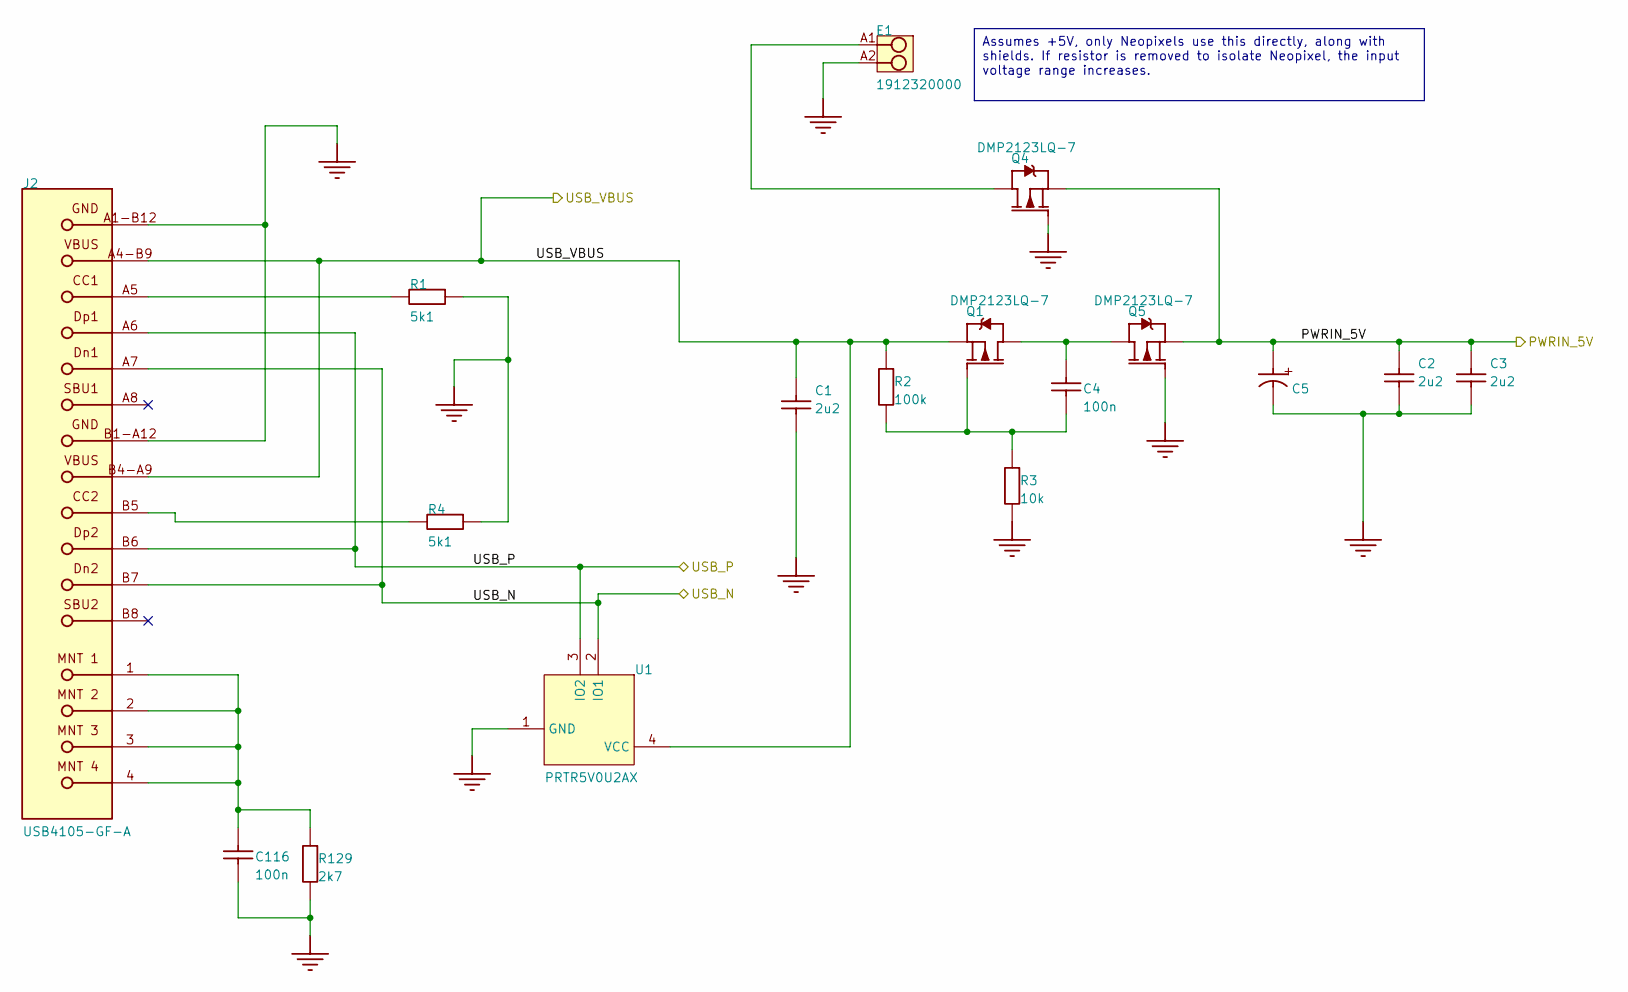
[picture p16: schematic Main_USB.kicad_sch]

Parts:
C1, C2, C3: 2u2; CAPC0603_M; MANUFACTURE PART NUMBER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 CL10B225KP8NNNC
C4, C116: 100n; CAPC0402_M; MANUFACTURE PART NUMBER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 CGA2B3X7R1V104K050BB
C5: 680uF; Cap_16v_680uF
E1: 1912320000; PS_3_5_90_02
J2: USB4105-GF-A; FP-USB4105-GF-A-MFG
Q1, Q4, Q5: DMP2123LQ-7; SOT95P245X110-3M; MANUFACTURE PART NUMBER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 DMP2123LQ-7
R1, R4: 5k1; RESC1608X55N; MANUFACTURE PART NUMBER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 RC0603FR-075K1L
R2: 100k; RESC1005X40N; MANUFACTURE PART NUMBER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 RC0402FR-07100KL
R3: 10k; RESC1005X40N; MANUFACTURE PART NUMBER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 RC0402FR-0710KL
R129: 2k7; RESC1005X40N; MANUFACTURE PART NUMBER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 RC0402FR-072K7L
U1: PRTR5V0U2AX; SOT143B

Connections:
GND: C1.2, C2.2, C3.2, C5.2, C116.2, E1.A2, J2.A1-B12 (GND), J2.B1-A12 (GND), Q4.1 (G), Q5.1 (G), R1.2, R3.2, R4.2, R129.2, U1.1 (GND)
unnamed: C4.1, Q1.3 (D), Q5.3 (D)
unnamed: C4.2, Q1.1 (G), R2.2, R3.1
unnamed: C116.1, J2.1 (MNT_1), J2.2 (MNT_2), J2.3 (MNT_3), J2.4 (MNT_4), R129.1
unnamed: E1.A1, Q4.3 (D)
unnamed: J2.A5 (CC1), R1.1
unnamed: J2.B5 (CC2), R4.1
PWRIN_5V: C2.1, C3.1, C5.1, Q4.2 (S), Q5.2 (S)
USB_N: J2.A7 (Dn1), J2.B7 (Dn2), U1.2 (IO1)
USB_P: J2.A6 (Dp1), J2.B6 (Dp2), U1.3 (IO2)
USB_VBUS: C1.1, J2.A4-B9 (VBUS), J2.B4-A9 (VBUS), Q1.2 (S), R2.1, U1.4 (VCC)

Notes on the sheet:
Assumes +5V, only Neopixels use this directly, along with shields. If resistor is removed to isolate Neopixel, the input voltage range increases.
