newaetech/sonata-pcb/sonata-one/sonata_kicad_project/Mechanical.kicad_sch

## KiCad design sonata-one/sonata_kicad_project/Mechanical.kicad_sch (2025-01-31)

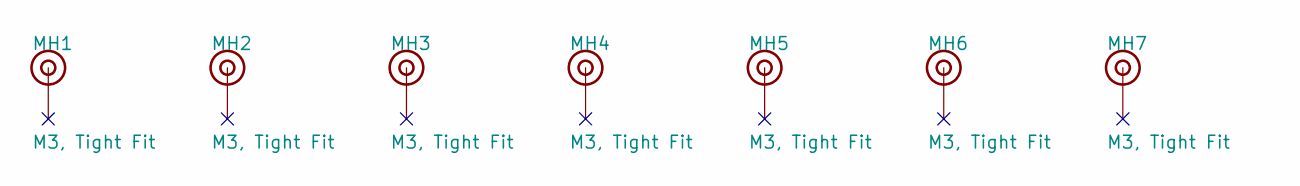
[picture p17: schematic Mechanical.kicad_sch]

Parts:
MH1, MH2, MH3, MH4, MH5, MH6, MH7: M3, Tight Fit; MOUNT_M3_TIGHT
