newaetech/sonata-pcb/sonata-one/sonata_kicad_project/MicroSD.kicad_sch

## KiCad design sonata-one/sonata_kicad_project/MicroSD.kicad_sch (2025-01-31)

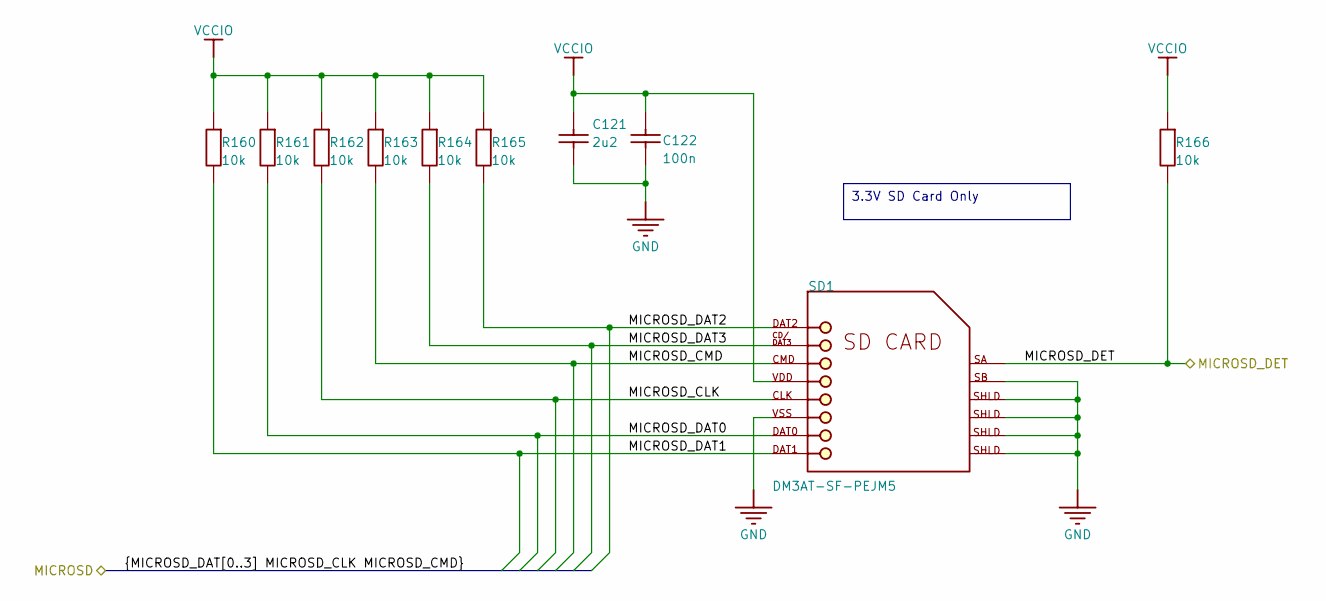
[picture p18: schematic MicroSD.kicad_sch]

Parts:
C121: 2u2; CAPC0603_M; MANUFACTURE PART NUMBER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 CL10B225KP8NNNC
C122: 100n; CAPC0402_M; MANUFACTURE PART NUMBER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 CGA2B3X7R1V104K050BB
R160, R161, R162, R163, R164, R165, R166: 10k; RESC1005X40N; MANUFACTURE PART NUMBER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 RC0402FR-0710KL
SD1: DM3AT-SF-PEJM5; FP-DM3AT-SF-PEJM5-MFG

Connections:
GND: C121.2, C122.2, SD1.6 (VSS), SD1.10 (SB), SD1.11 (SHLD), SD1.12 (SHLD), SD1.13 (SHLD), SD1.14 (SHLD)
MICROSD_CLK: R162.1, SD1.5 (CLK)
MICROSD_CMD: R163.1, SD1.3 (CMD)
MICROSD_DAT0: R161.1, SD1.7 (DAT0)
MICROSD_DAT1: R160.1, SD1.8 (DAT1)
MICROSD_DAT2: R165.1, SD1.1 (DAT2)
MICROSD_DAT3: R164.1, SD1.2 (CD/DAT3)
MICROSD_DET: R166.1, SD1.9 (SA)
VCCIO: C121.1, C122.1, R160.2, R161.2, R162.2, R163.2, R164.2, R165.2, R166.2, SD1.4 (VDD)

Notes on the sheet:
3.3V SD Card Only
