newaetech/sonata-pcb/sonata-one/sonata_kicad_project/RP2040.kicad_sch

## KiCad design sonata-one/sonata_kicad_project/RP2040.kicad_sch (2025-01-31)

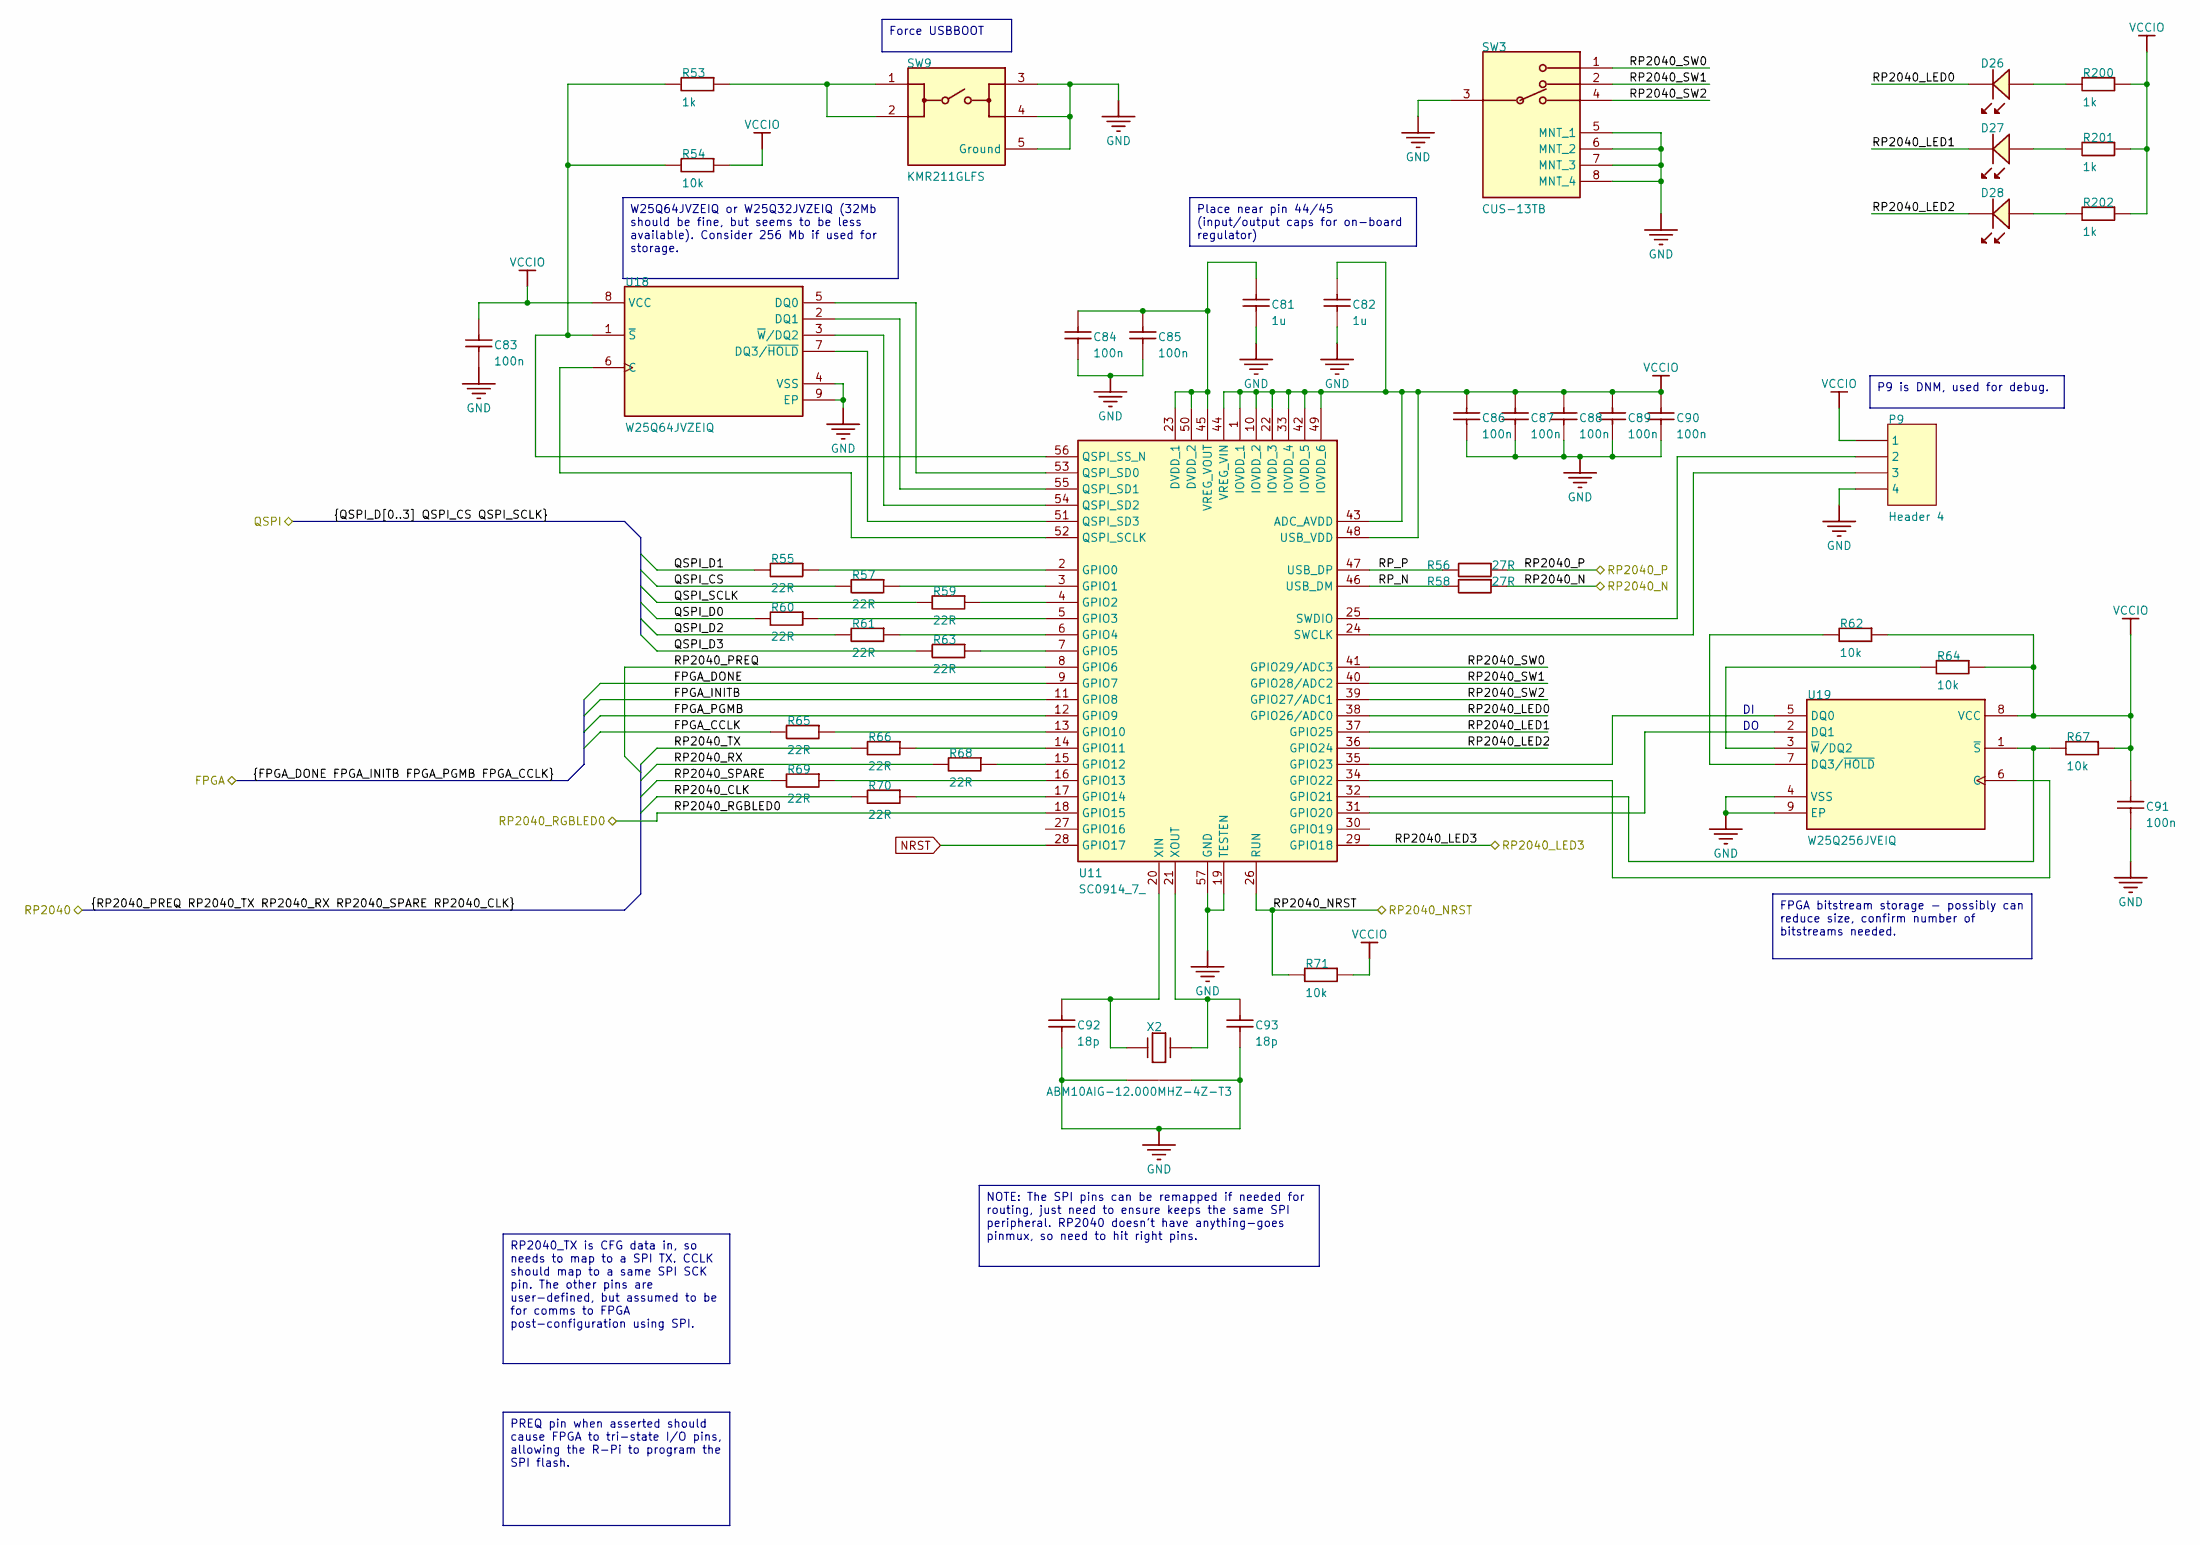
[picture p19: schematic RP2040.kicad_sch]

Parts:
C81, C82: 1u; CAPC0603_M; MANUFACTURE PART NUMBER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 CL10A105KB8NNNC
C83, C84, C85, C86, C87, C88, C89, C90, C91: 100n; CAPC0402_M; MANUFACTURE PART NUMBER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 CGA2B3X7R1V104K050BB
C92, C93: 18p; CAPC0402_M; MANUFACTURE PART NUMBER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 GRM1555C1H180JA01D
D26, D27, D28: LED, 0603, Green; LED-0603-GREEN; MANUFACTURE PART NUMBER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 APT1608CGCK
P9: Header 4; HDR1X4
R53, R200, R201, R202: 1k; RESC1005X40N; MANUFACTURE PART NUMBER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 RC0402FR-071KL
R54, R62, R64, R67, R71: 10k; RESC1005X40N; MANUFACTURE PART NUMBER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 RC0402FR-0710KL
R55, R57, R59, R60, R61, R63, R65, R66, R68, R69, R70: 22R; RESC1005X40N; MANUFACTURE PART NUMBER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 RC0402FR-0722RL
R56, R58: 27R; RESC1005X40N; MANUFACTURE PART NUMBER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 RC0402FR-0727RL
SW3: CUS-13TB; FP-CUS-13TB-MFG
SW9: KMR211GLFS; FP-KMR211GLFS-MFG
U11: SC0914_7_; QFN40P700X700X90-57N-D
U18: W25Q64JVZEIQ; WSON68_Micron; MANUFACTURE PART NUMBER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 W25Q64JVZEIQ
U19: W25Q256JVEIQ; WSON68_Micron; MANUFACTURE PART NUMBER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 W25Q256JVEIQ
X2: ABM10AIG-12.000MHZ-4Z-T3; 2.5x2mm XTAL; MANUFACTURE PART NUMBER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 ABM10AIG-12.000MHZ-4Z-T3

Connections:
FPGA_CCLK: R65.1
FPGA_DONE: U11.9 (GPIO7)
FPGA_INITB: U11.11 (GPIO8)
FPGA_PGMB: U11.12 (GPIO9)
GND: C81.2, C82.2, C83.2, C84.2, C85.2, C86.2, C87.2, C88.2, C89.2, C90.2, C91.2, C92.2, C93.2, P9.4, SW3.3 (C), SW3.5 (MNT_1), SW3.6 (MNT_2), SW3.7 (MNT_3), SW3.8 (MNT_4), SW9.3, SW9.4, SW9.5 (Ground), U11.19 (TESTEN), U11.57 (GND), U18.4 (VSS), U18.9 (EP), U19.4 (VSS), U19.9 (EP), X2.2 (GND), X2.4 (GND)
NRST: U11.28 (GPIO17)
unnamed: C81.1, C84.1, C85.1, U11.23 (DVDD_1), U11.45 (VREG_VOUT), U11.50 (DVDD_2)
unnamed: C92.1, U11.20 (XIN), X2.1 (IN)
unnamed: C93.1, U11.21 (XOUT), X2.3 (OUT)
unnamed: D26.A, R200.1
unnamed: D27.A, R201.1
unnamed: D28.A, R202.1
unnamed: P9.2, U11.25 (SWDIO)
unnamed: P9.3, U11.24 (SWCLK)
unnamed: R53.1, R54.2, U11.56 (QSPI_SS_N), U18.1 (~S)
unnamed: R53.2, SW9.1, SW9.2
unnamed: R55.2, U11.2 (GPIO0)
unnamed: R57.2, U11.3 (GPIO1)
unnamed: R59.2, U11.4 (GPIO2)
unnamed: R60.2, U11.5 (GPIO3)
unnamed: R61.2, U11.6 (GPIO4)
unnamed: R62.2, U19.7 (DQ3/~HOLD)
unnamed: R63.2, U11.7 (GPIO5)
unnamed: R64.2, U19.3 (~W/DQ2)
unnamed: R65.2, U11.13 (GPIO10)
unnamed: R66.2, U11.14 (GPIO11)
unnamed: R67.1, U11.32 (GPIO21), U19.1 (~S)
unnamed: R68.2, U11.15 (GPIO12)
unnamed: R69.2, U11.16 (GPIO13)
unnamed: R70.2, U11.17 (GPIO14)
unnamed: U11.31 (GPIO20), U19.2 (DQ1)
unnamed: U11.34 (GPIO22), U19.6 (C)
unnamed: U11.35 (GPIO23), U19.5 (DQ0)
unnamed: U11.51 (QSPI_SD3), U18.7 (DQ3/~HOLD)
unnamed: U11.52 (QSPI_SCLK), U18.6 (C)
unnamed: U11.53 (QSPI_SD0), U18.5 (DQ0)
unnamed: U11.54 (QSPI_SD2), U18.3 (~W/DQ2)
unnamed: U11.55 (QSPI_SD1), U18.2 (DQ1)
QSPI_CS: R57.1
QSPI_D0: R60.1
QSPI_D1: R55.1
QSPI_D2: R61.1
QSPI_D3: R63.1
QSPI_SCLK: R59.1
RP2040_CLK: R70.1
RP2040_LED0: D26.K, U11.38 (GPIO26/ADC0)
RP2040_LED1: D27.K, U11.37 (GPIO25)
RP2040_LED2: D28.K, U11.36 (GPIO24)
RP2040_LED3: U11.29 (GPIO18)
RP2040_N: R58.1
RP2040_NRST: R71.1, U11.26 (RUN)
RP2040_P: R56.1
RP2040_PREQ: U11.8 (GPIO6)
RP2040_RGBLED0: U11.18 (GPIO15)
RP2040_RX: R68.1
RP2040_SPARE: R69.1
RP2040_SW0: SW3.1, U11.41 (GPIO29/ADC3)
RP2040_SW1: SW3.2, U11.40 (GPIO28/ADC2)
RP2040_SW2: SW3.4, U11.39 (GPIO27/ADC1)
RP2040_TX: R66.1
RP_N: R58.2, U11.46 (USB_DM)
RP_P: R56.2, U11.47 (USB_DP)
VCCIO: C82.1, C83.1, C86.1, C87.1, C88.1, C89.1, C90.1, C91.1, P9.1, R54.1, R62.1, R64.1, R67.2, R71.2, R200.2, R201.2, R202.2, U11.1 (IOVDD_1), U11.10 (IOVDD_2), U11.22 (IOVDD_3), U11.33 (IOVDD_4), U11.42 (IOVDD_5), U11.43 (ADC_AVDD), U11.44 (VREG_VIN), U11.48 (USB_VDD), U11.49 (IOVDD_6), U18.8 (VCC), U19.8 (VCC)

Notes on the sheet:
Force USBBOOT
PREQ pin when asserted should cause FPGA to tri-state I/O pins, allowing the R-Pi to program the SPI flash.
RP2040_TX is CFG data in, so needs to map to a SPI TX. CCLK should map to a same SPI SCK pin. The other pins are user-defined, but assumed to be for comms to FPGA post-configuration using SPI.
Place near pin 44/45 (input/output caps for on-board regulator)
P9 is DNM, used for debug.
NOTE: The SPI pins can be remapped if needed for routing, just need to ensure keeps the same SPI peripheral. RP2040 doesn't have anything-goes pinmux, so need to hit right pins.
FPGA bitstream storage - possibly can reduce size, confirm number of bitstreams needed.
W25Q64JVZEIQ or W25Q32JVZEIQ (32Mb should be fine, but seems to be less available). Consider 256 Mb if used for storage.
