newaetech/sonata-pcb/sonata-one/sonata_kicad_project/RS485_232_ETH.kicad_sch

## KiCad design sonata-one/sonata_kicad_project/RS485_232_ETH.kicad_sch (2025-01-31)

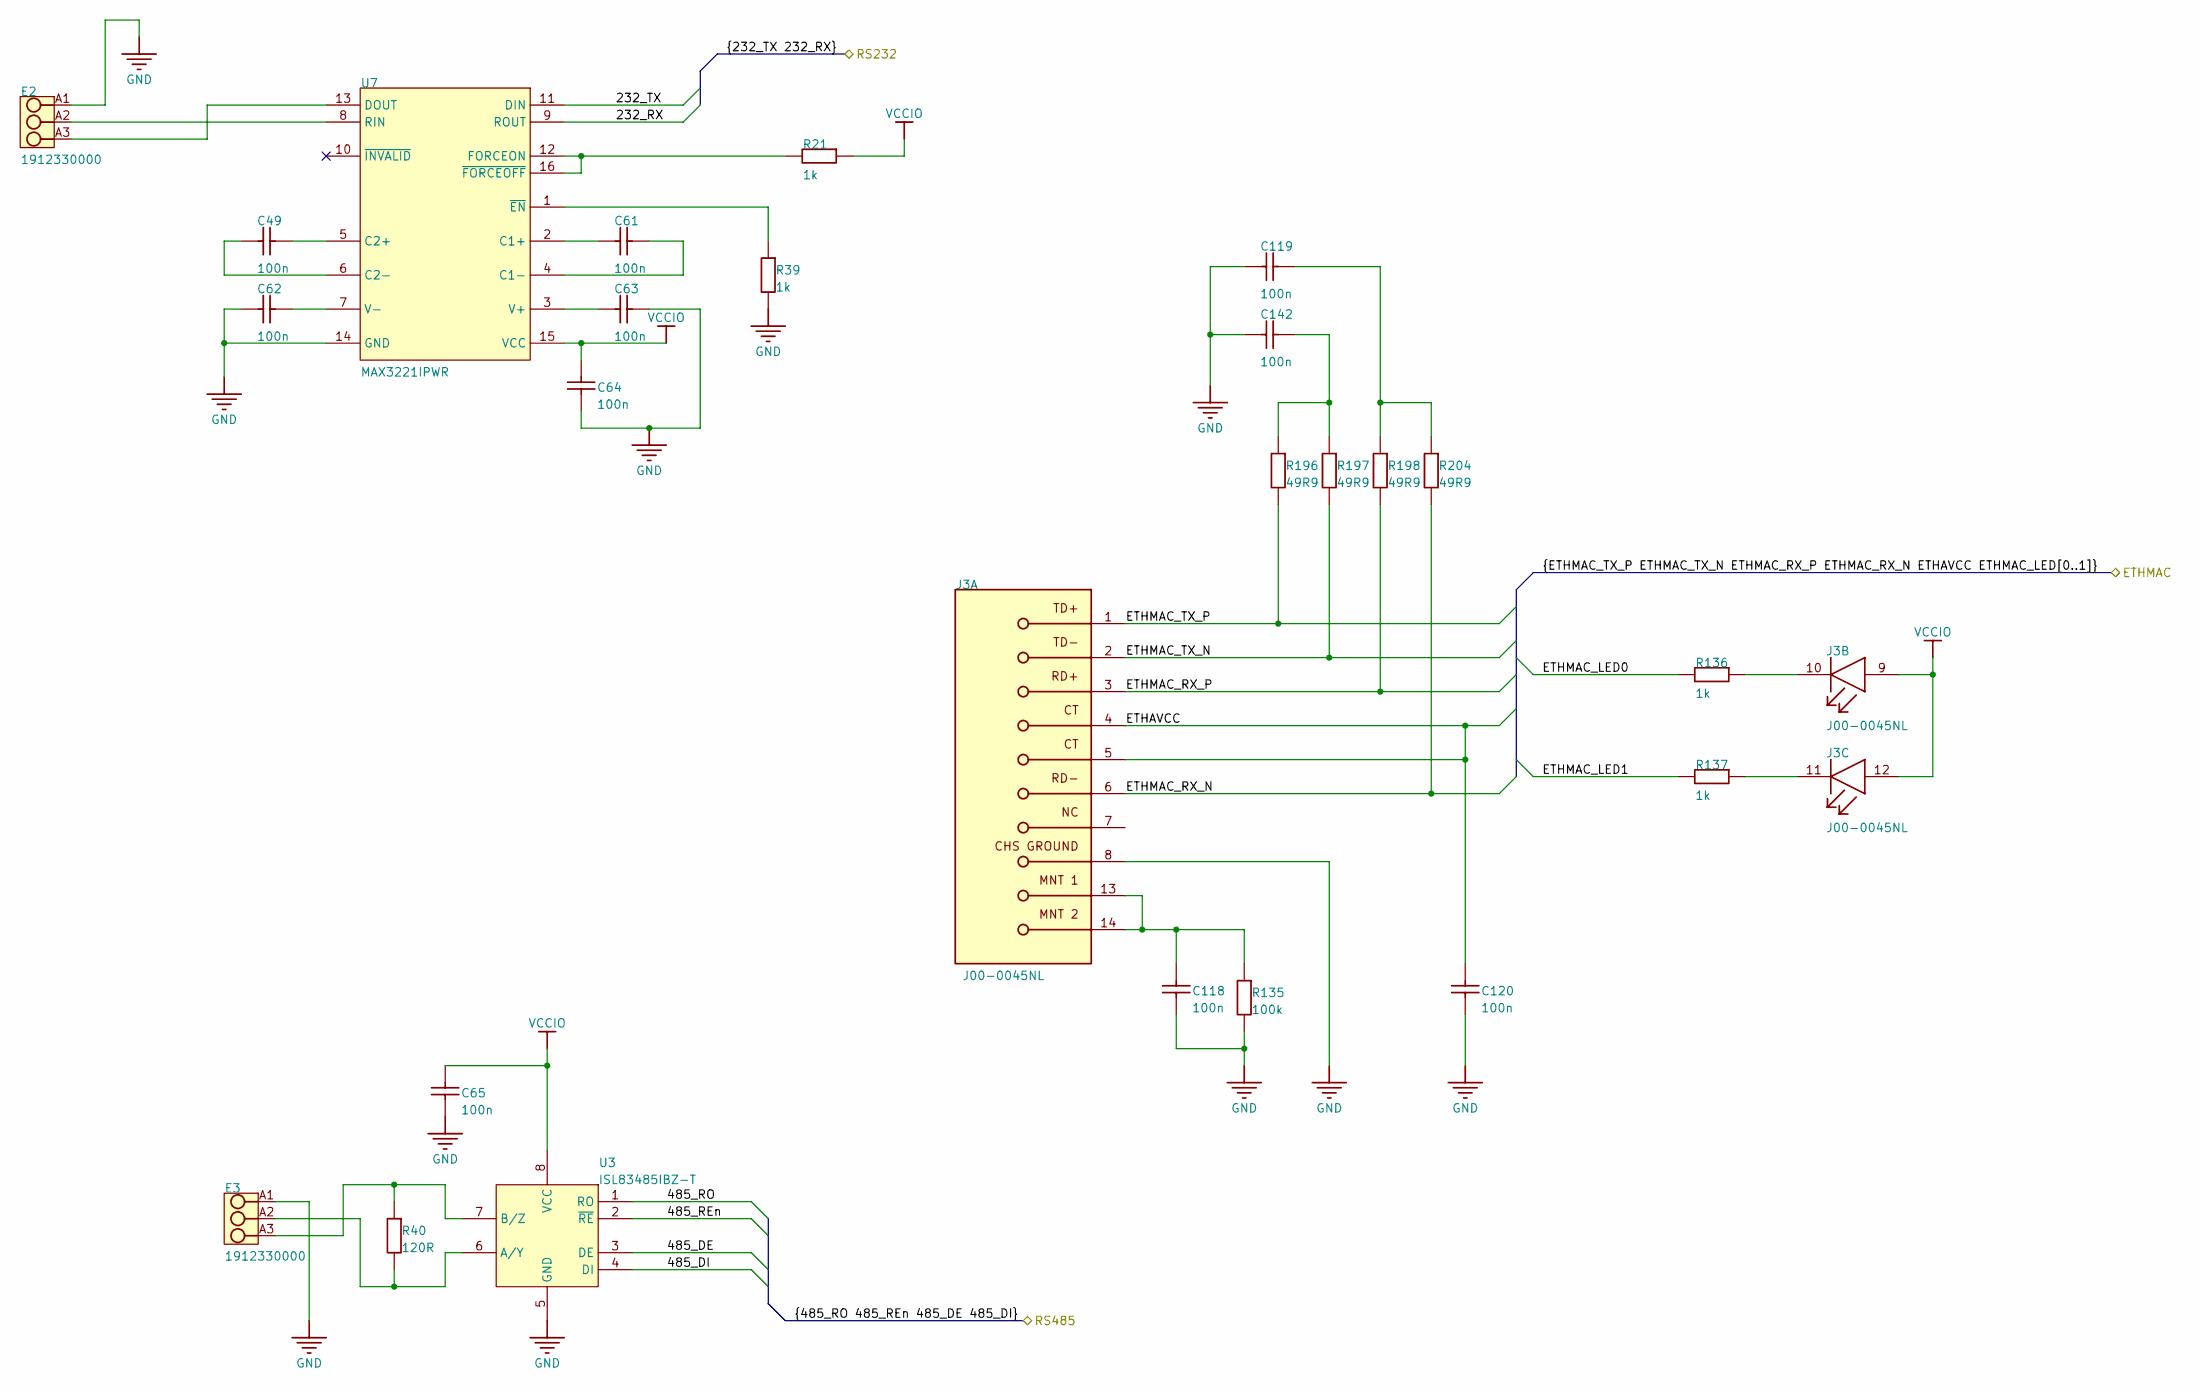
[picture p20: schematic RS485_232_ETH.kicad_sch]

Parts:
C49, C61, C62, C63, C64, C65, C118, C119, C120, C142: 100n; CAPC0402_M; MANUFACTURE PART NUMBER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 CGA2B3X7R1V104K050BB
E2, E3: 1912330000; PS_3_5_90_03
J3: J00-0045NL; FP-J00-0045NL-MFG
R21, R39, R136, R137: 1k; RESC1608X55N; MANUFACTURE PART NUMBER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 RC0603FR-071KL
R40: 120R; RESC1608X55N; MANUFACTURE PART NUMBER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 RC0603FR-07120RL
R135: 100k; RESC1005X40N; MANUFACTURE PART NUMBER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 RC0402FR-07100KL
R196, R197, R198, R204: 49R9; RESC2012X70N; MANUFACTURE PART NUMBER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 RC0805FR-0749R9L
U3: ISL83485IBZ-T; SOIC8_NARROW; MANUFACTURE PART NUMBER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 ISL83485IBZ-T
U7: MAX3221IPWR; PW0016A_L

Connections:
232_RX: U7.9 (ROUT)
232_TX: U7.11 (DIN)
485_DE: U3.3 (DE)
485_DI: U3.4 (DI)
485_REn: U3.2 (~RE)
485_RO: U3.1 (RO)
ETHAVCC: C120.1, J3.4 (CT), J3.5 (CT)
ETHMAC_LED0: R136.1
ETHMAC_LED1: R137.1
ETHMAC_RX_N: J3.6 (RD-), R204.2
ETHMAC_RX_P: J3.3 (RD+), R198.2
ETHMAC_TX_N: J3.2 (TD-), R197.2
ETHMAC_TX_P: J3.1 (TD+), R196.2
GND: C62.2, C63.1, C64.1, C65.2, C118.2, C119.1, C120.2, C142.1, E2.A1, E3.A1, J3.8 (CHS_GROUND), R39.2, R135.2, U3.5 (GND), U7.14 (GND)
unnamed: C49.1, U7.5 (C2+)
unnamed: C49.2, U7.6 (C2-)
unnamed: C61.1, U7.4 (C1-)
unnamed: C61.2, U7.2 (C1+)
unnamed: C62.1, U7.7 (V-)
unnamed: C63.2, U7.3 (V+)
unnamed: C118.1, J3.13 (MNT_1), J3.14 (MNT_2), R135.1
unnamed: C119.2, R198.1, R204.1
unnamed: C142.2, R196.1, R197.1
unnamed: E2.A2, U7.8 (RIN)
unnamed: E2.A3, U7.13 (DOUT)
unnamed: E3.A2, R40.2, U3.6 (A/Y)
unnamed: E3.A3, R40.1, U3.7 (B/Z)
unnamed: J3.10 (GREEN_C), R136.2
unnamed: J3.11 (YELLOW_CATHODE), R137.2
unnamed: R21.1, U7.12 (FORCEON), U7.16 (~FORCEOFF)
unnamed: R39.1, U7.1 (~EN)
VCCIO: C64.2, C65.1, J3.9 (GREEN_A), J3.12 (YELLOW_ANODE), R21.2, U3.8 (VCC), U7.15 (VCC)
