newaetech/sonata-pcb/sonata-one/sonata_kicad_project/SMPS.kicad_sch

## KiCad design sonata-one/sonata_kicad_project/SMPS.kicad_sch (2025-01-31)

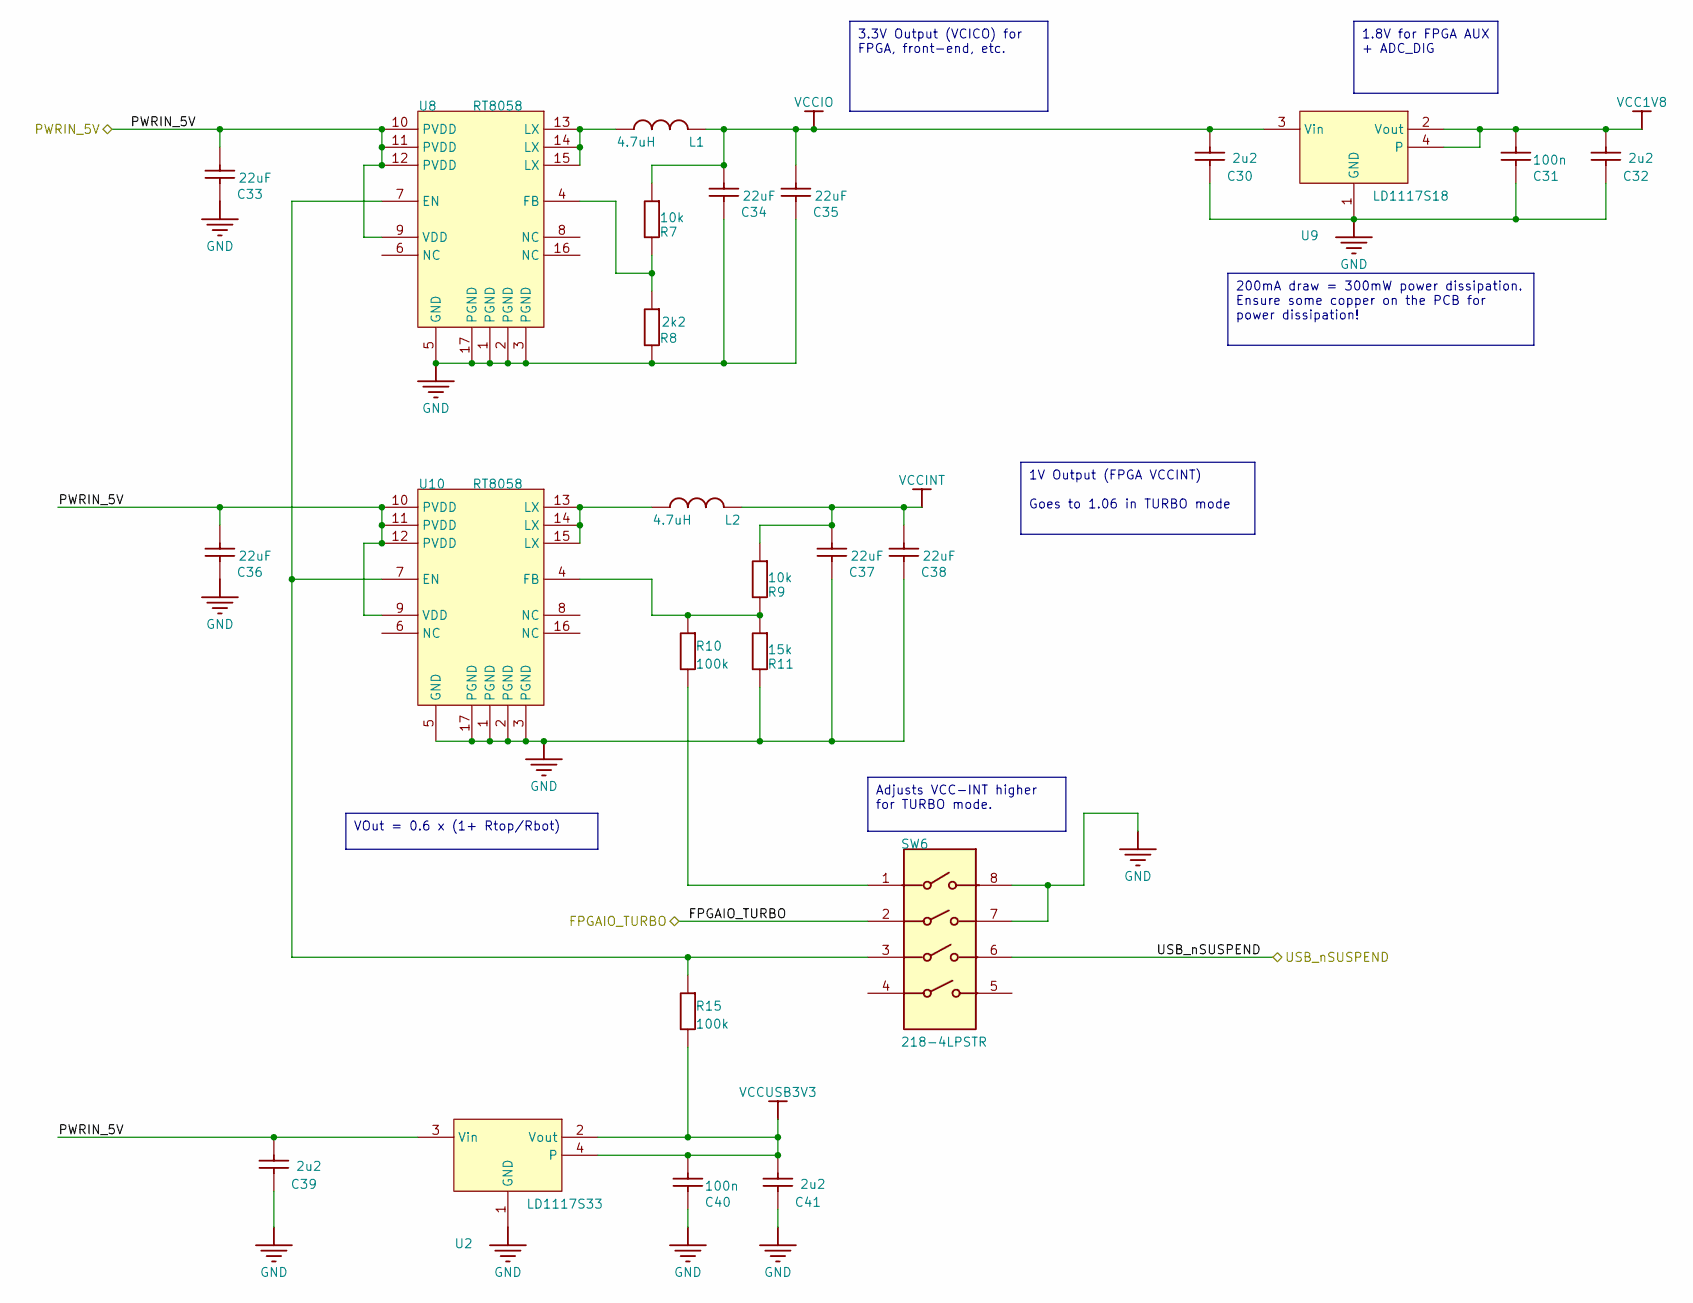
[picture p21: schematic SMPS.kicad_sch]

Parts:
C30, C32, C39, C41: 2u2; CAPC0603_M; MANUFACTURE PART NUMBER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 CL10B225KP8NNNC
C31, C40: 100n; CAPC0402_M
C33, C34, C35, C36, C37, C38: 22uF; CAPC0805_M; MANUFACTURE PART NUMBER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 CL21A226MOCLRNC
L1, L2: 4.7uH; NR6028; MANUFACTURE PART NUMBER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 NR6028T4R7M
R7, R9: 10k; RESC1005X40N; MANUFACTURE PART NUMBER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 RC0402FR-0710KL
R8: 2k2; RESC1005X40N; MANUFACTURE PART NUMBER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 RC0402FR-072K2L
R10: 100k; RESC1005X40N; MANUFACTURE PART NUMBER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 RC0402FR-07100KL
R11: 15k; RESC1005X40N; MANUFACTURE PART NUMBER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 RC0402FR-0715KL
R15: 100k; RESC1608X55N; MANUFACTURE PART NUMBER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 RC0603FR-07100KL
SW6: 218-4LPSTR; FP-218-4LPSTR-MFG
U2: LD1117S33; SOT-223; MANUFACTURE PART NUMBER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 LD1117S33TR
U8, U10: RT8058; QFN16_50P300X300X100_HS-17M; MANUFACTURE PART NUMBER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 RT8058
U9: LD1117S18; SOT-223; MANUFACTURE PART NUMBER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 LD1117S18TR

Connections:
FPGAIO_TURBO: SW6.2
GND: C30.2, C31.2, C32.2, C33.2, C34.2, C35.2, C36.2, C37.2, C38.2, C39.2, C40.2, C41.2, R8.2, R11.2, SW6.7, SW6.8, U2.1 (GND), U8.1 (PGND), U8.2 (PGND), U8.3 (PGND), U8.5 (GND), U8.17 (PGND), U9.1 (GND), U10.1 (PGND), U10.2 (PGND), U10.3 (PGND), U10.5 (GND), U10.17 (PGND)
unnamed: L1.1, U8.13 (LX), U8.14 (LX), U8.15 (LX)
unnamed: L2.1, U10.13 (LX), U10.14 (LX), U10.15 (LX)
unnamed: R7.2, R8.1, U8.4 (FB)
unnamed: R9.2, R10.1, R11.1, U10.4 (FB)
unnamed: R10.2, SW6.1
unnamed: R15.2, SW6.3, U8.7 (EN), U10.7 (EN)
PWRIN_5V: C33.1, C36.1, C39.1, U2.3 (Vin), U8.9 (VDD), U8.10 (PVDD), U8.11 (PVDD), U8.12 (PVDD), U10.9 (VDD), U10.10 (PVDD), U10.11 (PVDD), U10.12 (PVDD)
USB_nSUSPEND: SW6.6
VCC1V8: C31.1, C32.1, U9.2 (Vout), U9.4
VCCINT: C37.1, C38.1, L2.2, R9.1
VCCIO: C30.1, C34.1, C35.1, L1.2, R7.1, U9.3 (Vin)
VCCUSB3V3: C40.1, C41.1, R15.1, U2.2 (Vout), U2.4

Notes on the sheet:
VOut = 0.6 x (1+ Rtop/Rbot)
1V Output (FPGA VCCINT) Goes to 1.06 in TURBO mode
1.8V for FPGA AUX + ADC_DIG
3.3V Output (VCICO) for FPGA, front-end, etc.
Adjusts VCC-INT higher for TURBO mode.
200mA draw = 300mW power dissipation. Ensure some copper on the PCB for power dissipation!
