newaetech/sonata-pcb/sonata-one/sonata_kicad_project/USBPhy.kicad_sch

## KiCad design sonata-one/sonata_kicad_project/USBPhy.kicad_sch (2025-01-31)

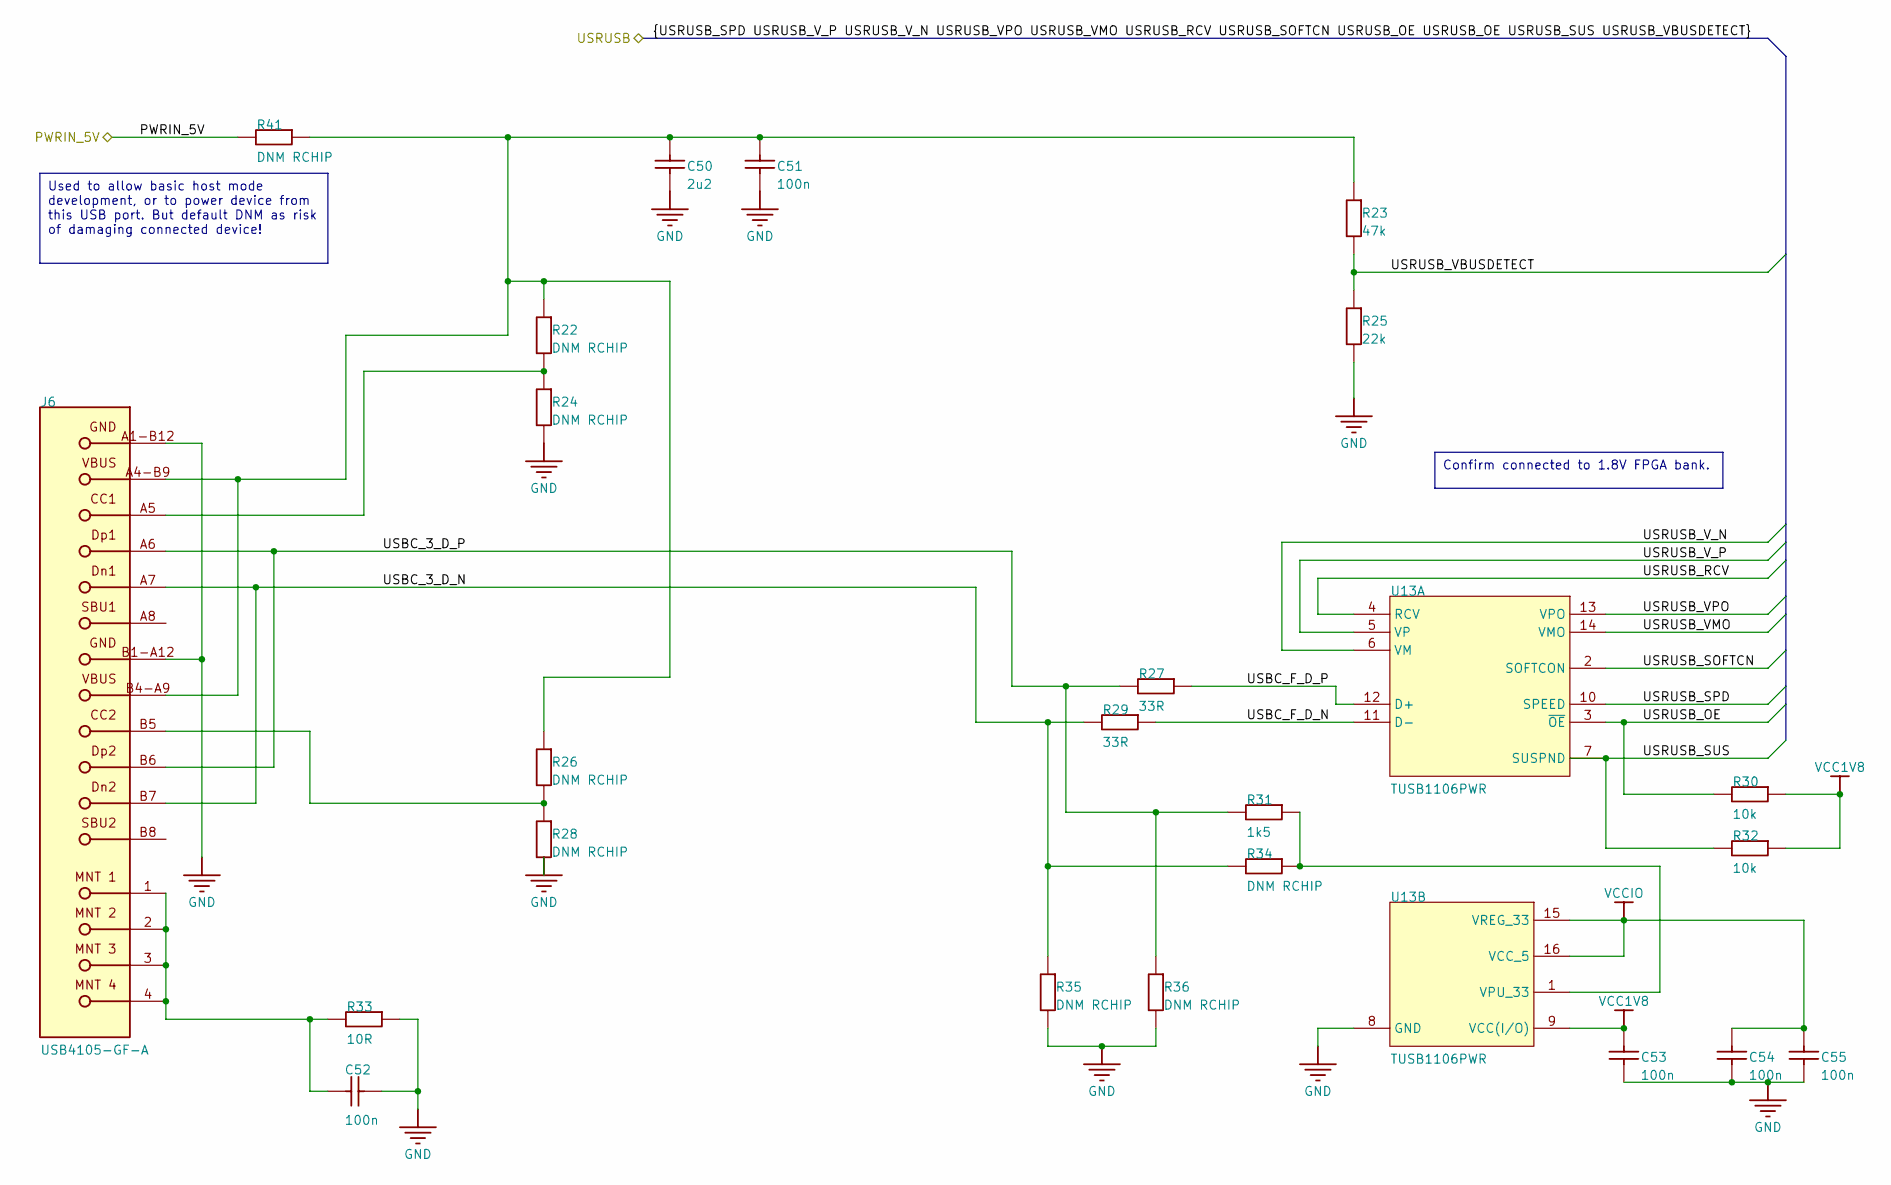
[picture p22: schematic USBPhy.kicad_sch]

Parts:
C50: 2u2; CAPC0603_M; MANUFACTURE PART NUMBER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 CL10B225KP8NNNC
C51, C53, C54, C55: 100n; CAPC0402_M; MANUFACTURE PART NUMBER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 CGA2B3X7R1V104K050BB
C52: 100n; CAPC0603_M; MANUFACTURE PART NUMBER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 C0603C104K5RACTU
J6: USB4105-GF-A; FP-USB4105-GF-A-MFG
R22, R24, R26, R28, R34, R35, R36, R41: DNM RCHIP; RESC1608X55N
R23: 47k; RESC1005X40N; MANUFACTURE PART NUMBER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 RC0402FR-0747KL
R25: 22k; RESC1005X40N; MANUFACTURE PART NUMBER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 RC0402FR-0722KL
R27, R29: 33R; RESC1608X55N; MANUFACTURE PART NUMBER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 RC0603FR-0733RL
R30, R32: 10k; RESC1005X40N; MANUFACTURE PART NUMBER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 RC0402FR-0710KL
R31: 1k5; RESC1608X55N; MANUFACTURE PART NUMBER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 RC0603FR-071K5L
R33: 10R; RESC1608X55N; MANUFACTURE PART NUMBER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 RC0603FR-0710RL
U13: TUSB1106PWR; PW0016A_L

Connections:
GND: C50.2, C51.2, C52.2, C53.2, C54.2, C55.2, J6.A1-B12 (GND), J6.B1-A12 (GND), R24.2, R25.2, R28.2, R33.2, R35.1, R36.1, U13.8 (GND)
unnamed: C50.1, C51.1, J6.A4-B9 (VBUS), J6.B4-A9 (VBUS), R22.1, R23.1, R26.1, R41.1
unnamed: C52.1, J6.1 (MNT_1), J6.2 (MNT_2), J6.3 (MNT_3), J6.4 (MNT_4), R33.1
unnamed: J6.A5 (CC1), R22.2, R24.1
unnamed: J6.B5 (CC2), R26.2, R28.1
unnamed: R31.2, R34.2, U13.1 (VPU_33)
PWRIN_5V: R41.2
USBC_3_D_N: J6.A7 (Dn1), J6.B7 (Dn2), R29.1, R34.1, R35.2
USBC_3_D_P: J6.A6 (Dp1), J6.B6 (Dp2), R27.1, R31.1, R36.2
USBC_F_D_N: R29.2, U13.11 (D-)
USBC_F_D_P: R27.2, U13.12 (D+)
USRUSB_OE: R30.1, U13.3 (~OE)
USRUSB_RCV: U13.4 (RCV)
USRUSB_SOFTCN: U13.2 (SOFTCON)
USRUSB_SPD: U13.10 (SPEED)
USRUSB_SUS: R32.1, U13.7 (SUSPND)
USRUSB_VBUSDETECT: R23.2, R25.1
USRUSB_VMO: U13.14 (VMO)
USRUSB_VPO: U13.13 (VPO)
USRUSB_V_N: U13.6 (VM)
USRUSB_V_P: U13.5 (VP)
VCC1V8: C53.1, R30.2, R32.2, U13.9 (VCC(I/O))
VCCIO: C54.1, C55.1, U13.15 (VREG_33), U13.16 (VCC_5)

Notes on the sheet:
Confirm connected to 1.8V FPGA bank.
Used to allow basic host mode development, or to power device from this USB port. But default DNM as risk of damaging connected device!
